Servacek/numeri/docs/pictures/dokumentacne_foto/final.jpg

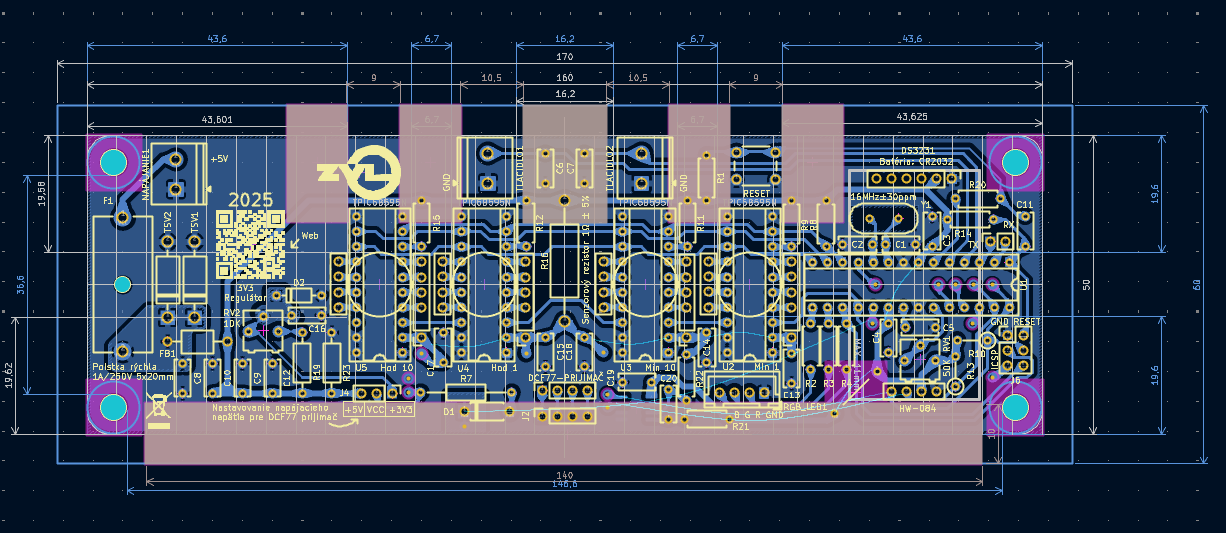
docs/pictures/dokumentacne_foto/final.jpg
