Servacek/numeri/docs/pictures/dokumentacne_foto/photo_1_2026-05-26_11-01-23.jpg

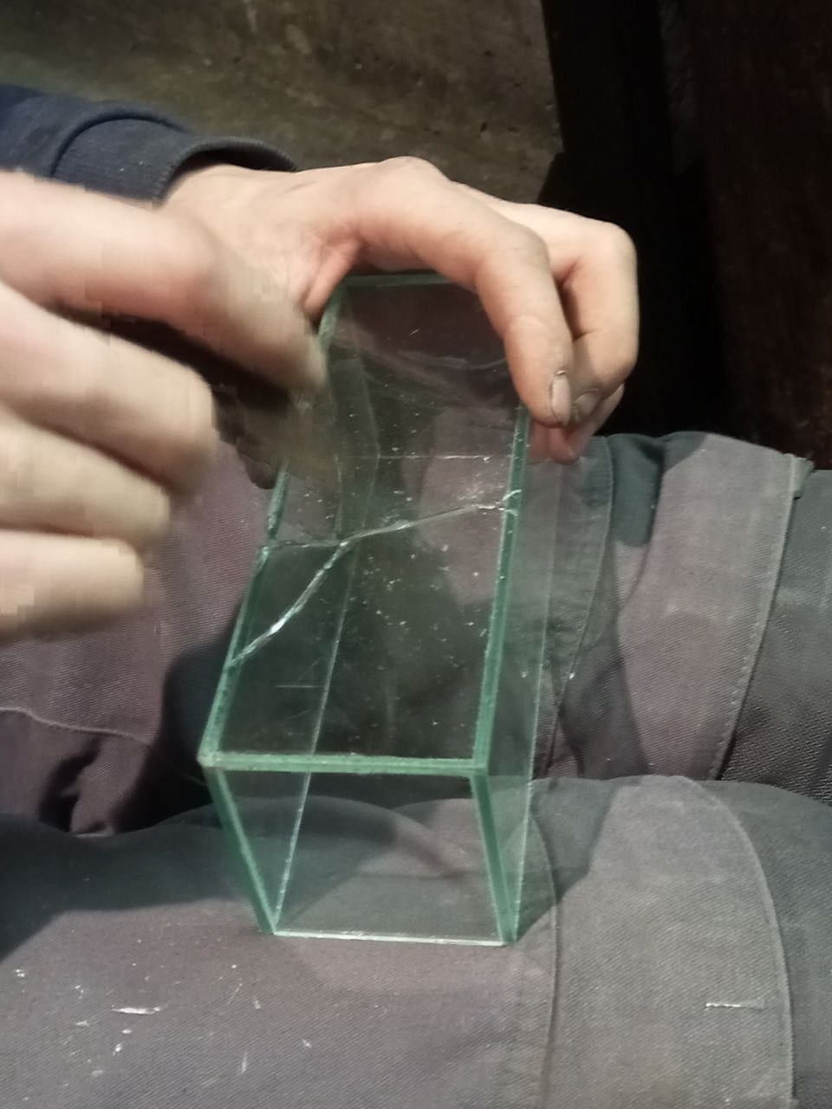
docs/pictures/dokumentacne_foto/photo_1_2026-05-26_11-01-23.jpg
