Servacek/numeri/docs/pictures/dokumentacne_foto/photo_1_2026-05-26_11-02-10.jpg

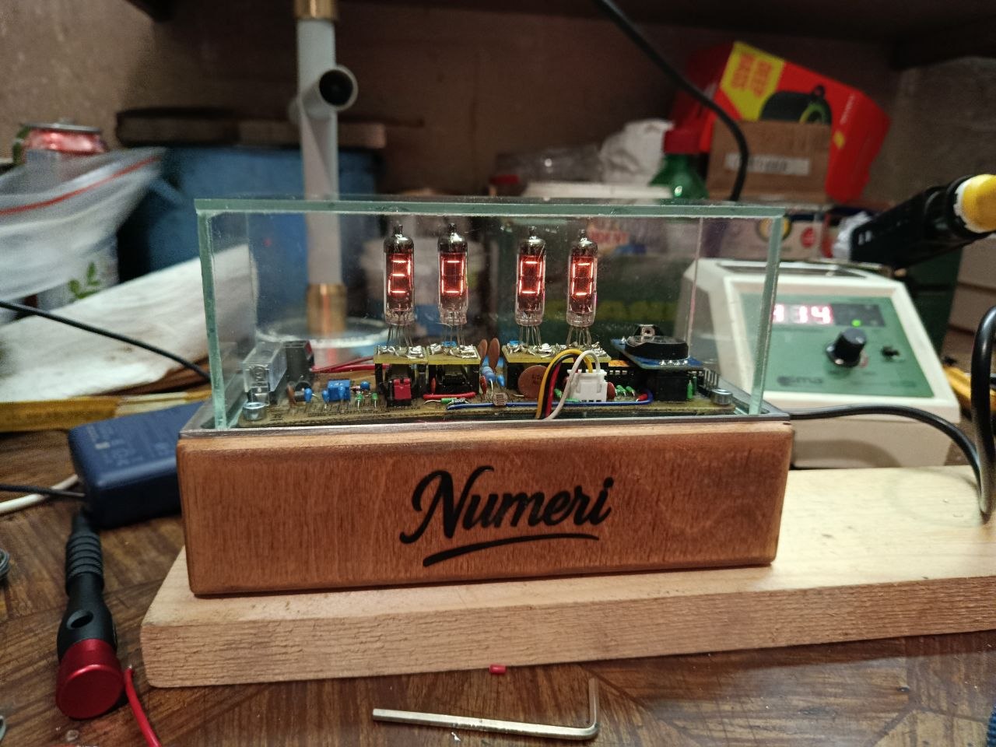
docs/pictures/dokumentacne_foto/photo_1_2026-05-26_11-02-10.jpg
