Servacek/numeri/docs/pictures/dokumentacne_foto/photo_3_2025-08-24_12-32-02.jpg

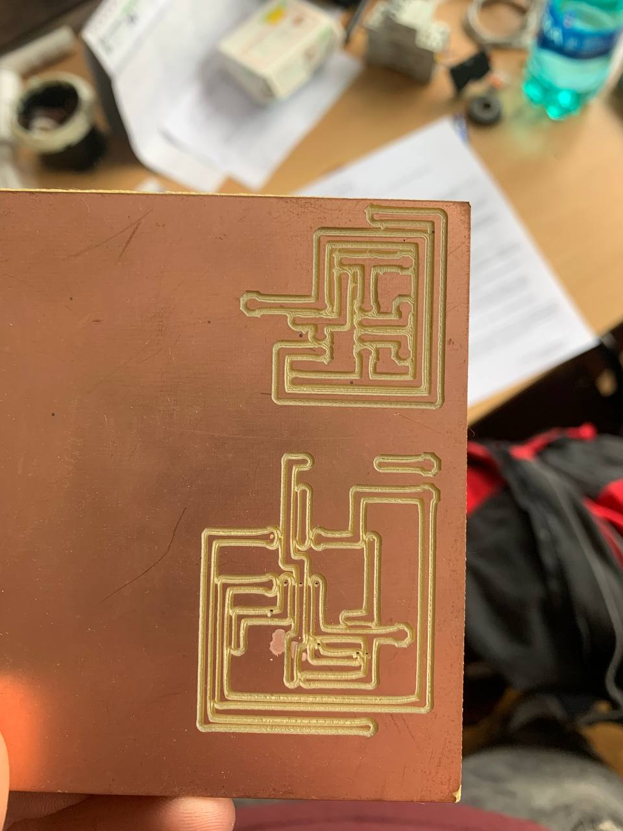
docs/pictures/dokumentacne_foto/photo_3_2025-08-24_12-32-02.jpg
