Servacek/numeri/docs/pictures/dokumentacne_foto/photo_3_2025-09-08_17-15-10.jpg

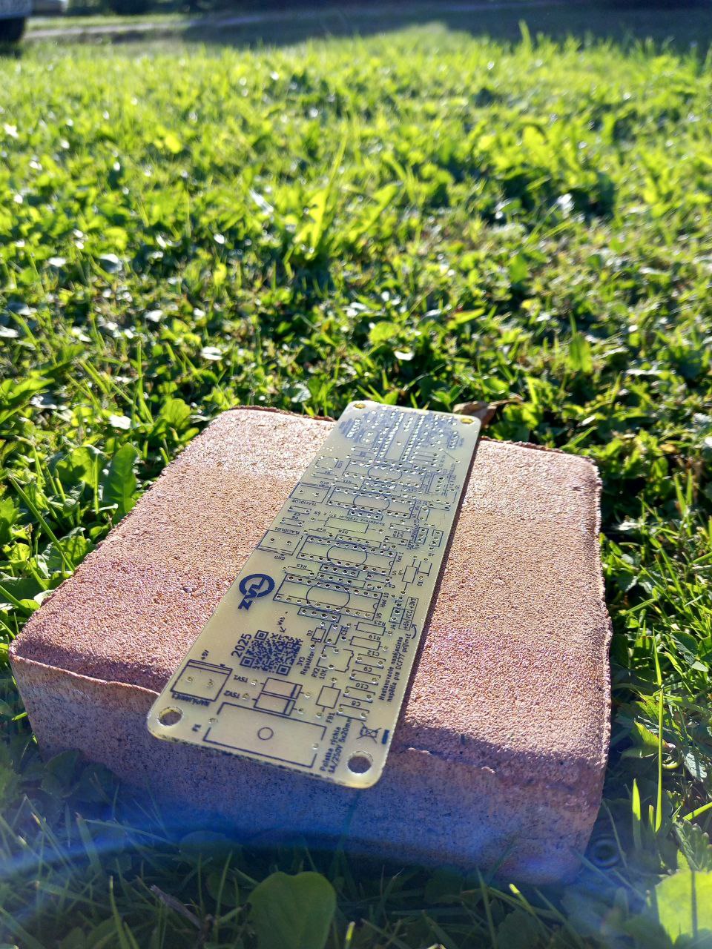
docs/pictures/dokumentacne_foto/photo_3_2025-09-08_17-15-10.jpg
