Servacek/numeri/docs/pictures/dokumentacne_foto/photo_6_2025-09-08_17-15-54.jpg

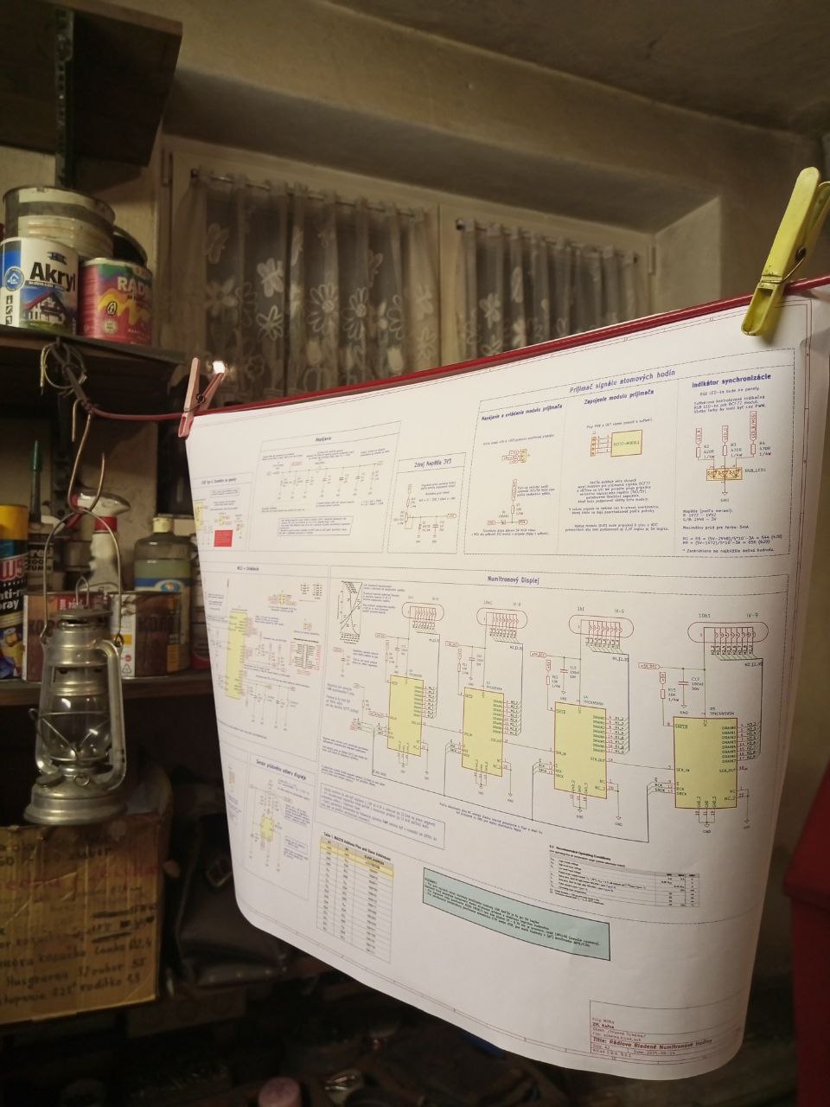
docs/pictures/dokumentacne_foto/photo_6_2025-09-08_17-15-54.jpg
