Servacek/numeri/docs/pictures/dokumentacne_foto/photo_15_2025-08-24_12-28-27.jpg

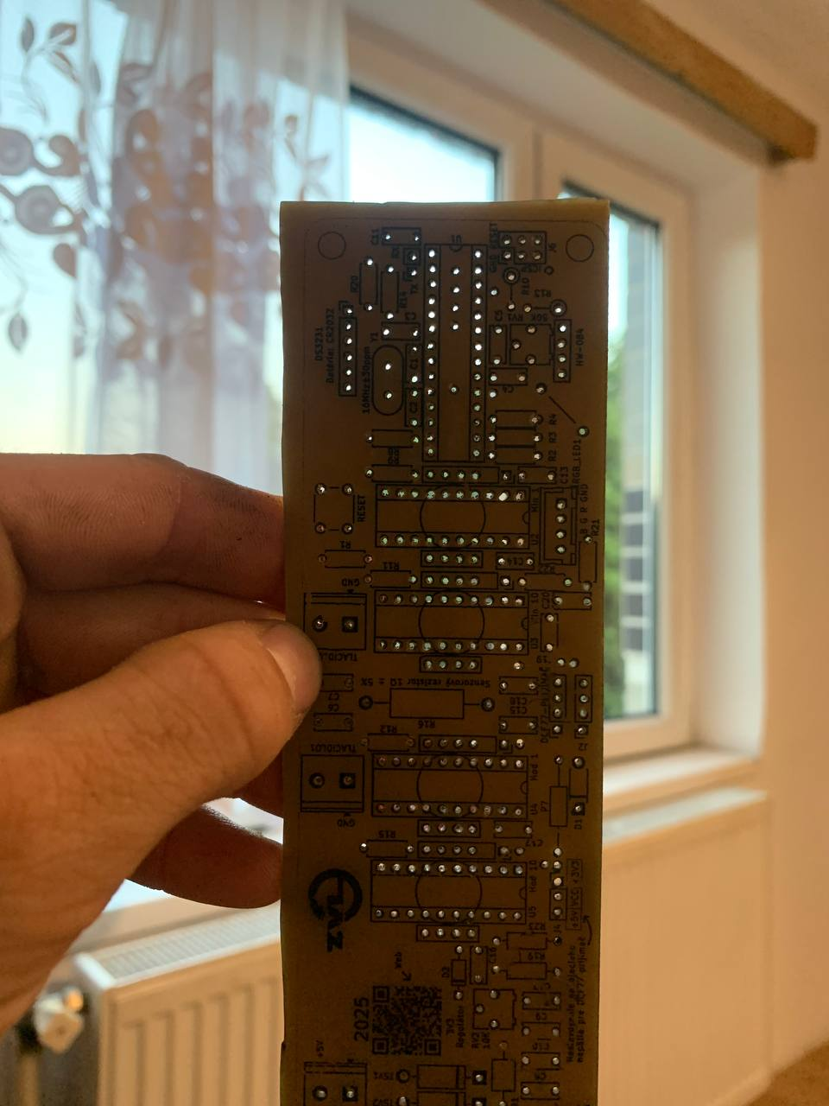
docs/pictures/dokumentacne_foto/photo_15_2025-08-24_12-28-27.jpg
