Servacek/numeri/docs/pictures/dokumentacne_foto/photo_2025-08-12_21-58-07.jpg

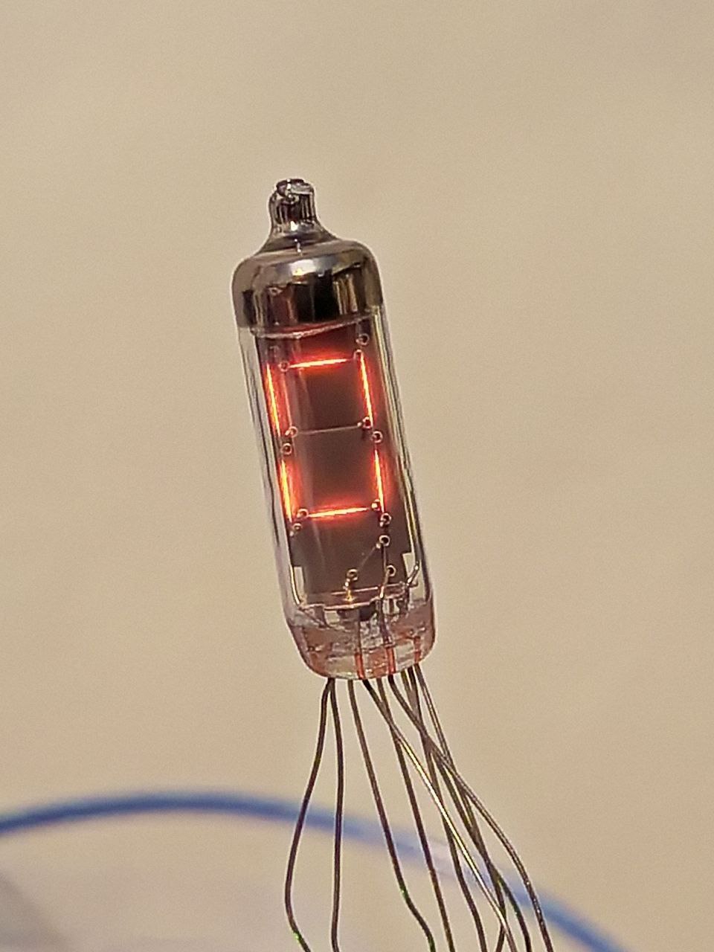
docs/pictures/dokumentacne_foto/photo_2025-08-12_21-58-07.jpg
