Servacek/numeri/docs/pictures/dokumentacne_foto/photo_2025-09-02_12-14-27.jpg

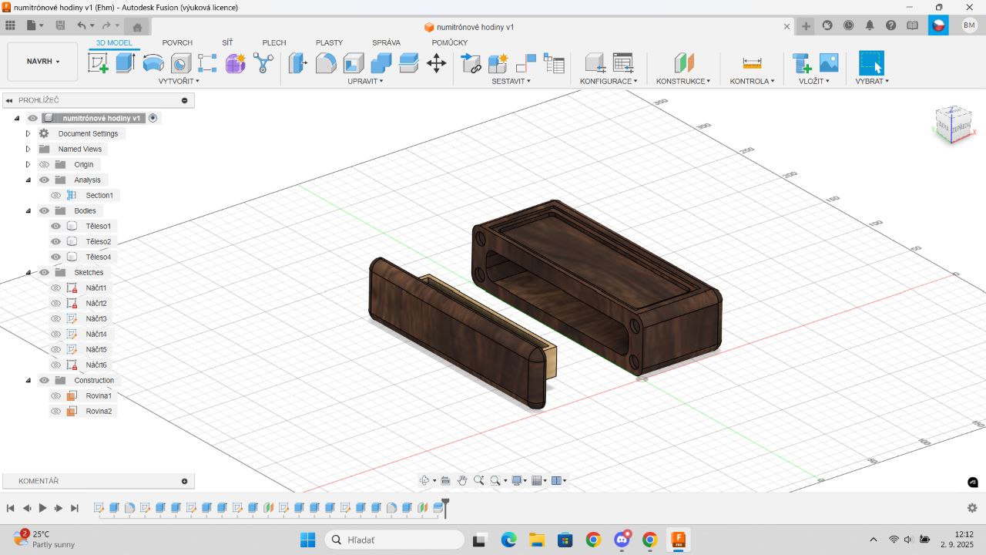
docs/pictures/dokumentacne_foto/photo_2025-09-02_12-14-27.jpg
