Servacek/numeri/docs/pictures/dokumentacne_foto/photo_2025-09-03_09-06-06.jpg

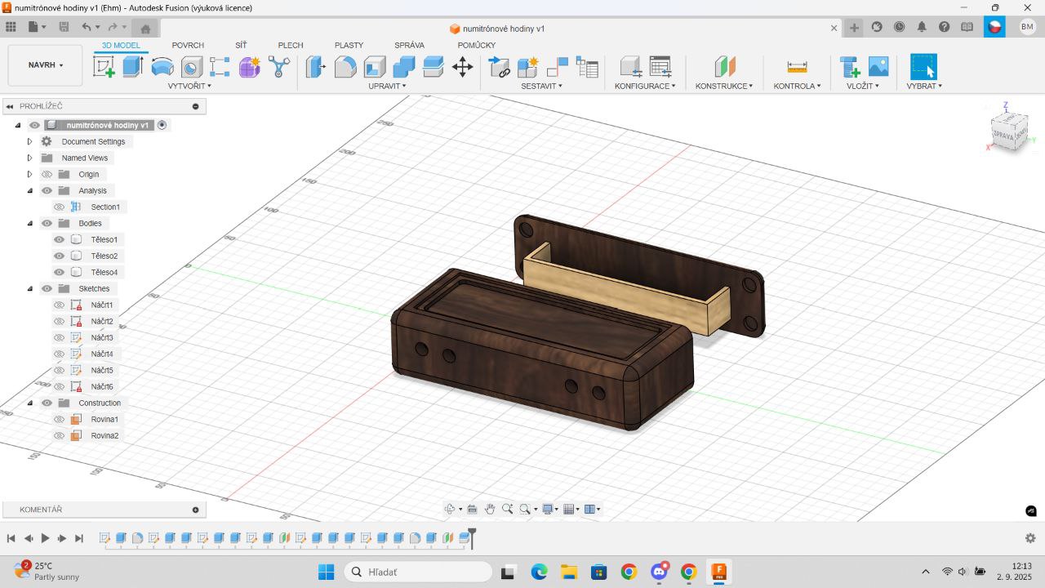
docs/pictures/dokumentacne_foto/photo_2025-09-03_09-06-06.jpg
