Servacek/numeri/docs/pictures/dokumentacne_foto/photo_2025-09-08_14-59-17.jpg

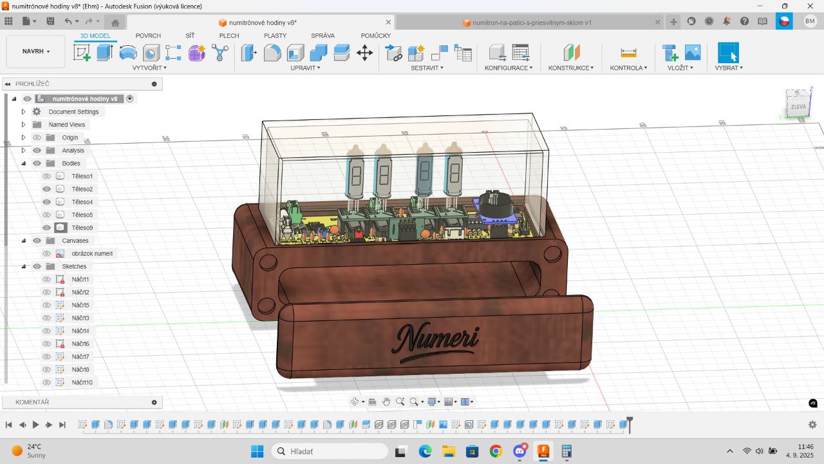
docs/pictures/dokumentacne_foto/photo_2025-09-08_14-59-17.jpg
