Servacek/numeri/docs/pictures/dokumentacne_foto/photo_2025-09-08_15-00-24.jpg

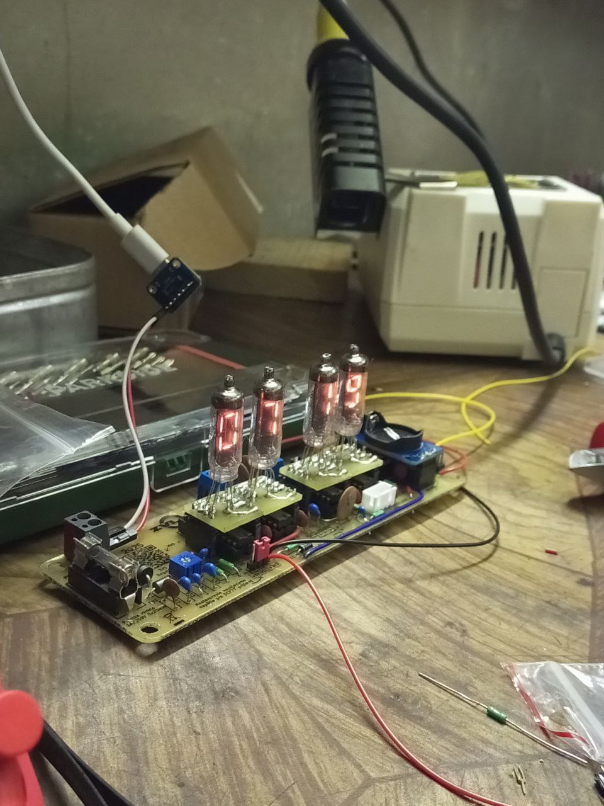
docs/pictures/dokumentacne_foto/photo_2025-09-08_15-00-24.jpg
