Servacek/numeri/docs/pictures/dokumentacne_foto/photo_2025-09-08_15-01-26.jpg

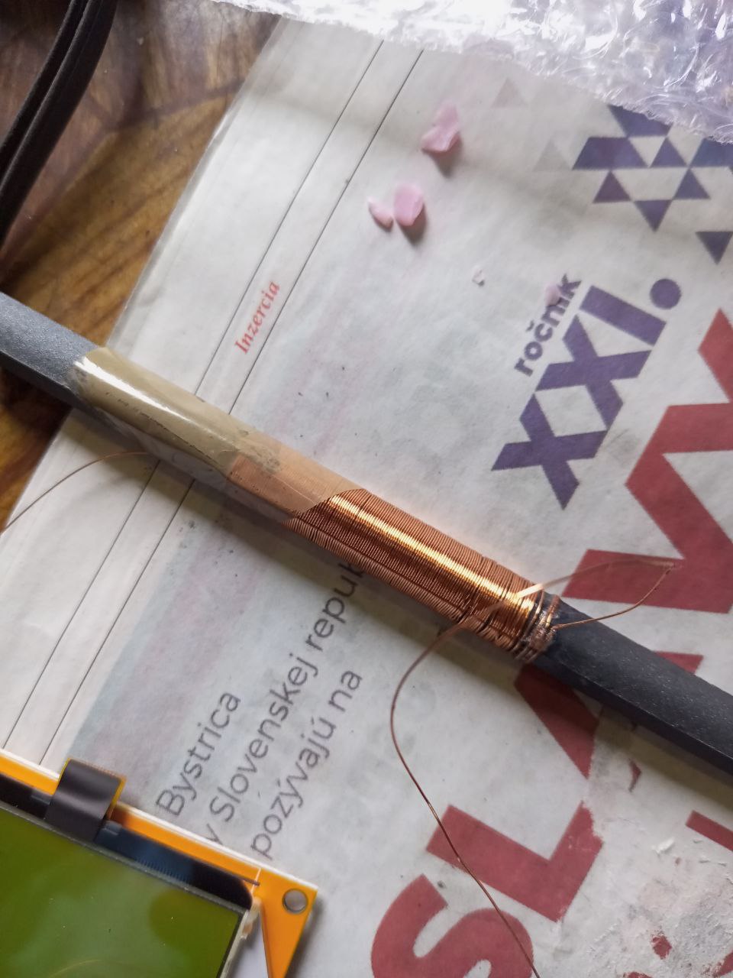
docs/pictures/dokumentacne_foto/photo_2025-09-08_15-01-26.jpg
