Servacek/numeri/docs/pictures/dokumentacne_foto/photo_2026-01-26_16-45-37.jpg

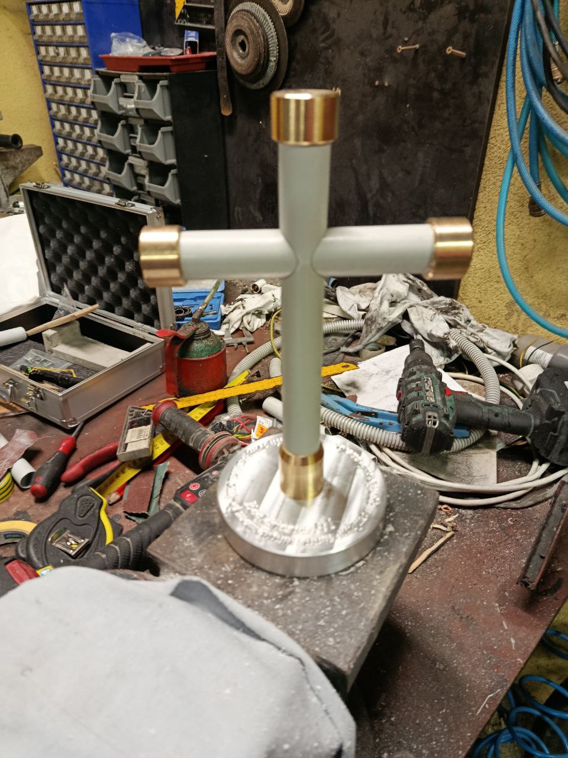
docs/pictures/dokumentacne_foto/photo_2026-01-26_16-45-37.jpg
