Servacek/numeri/docs/pictures/dokumentacne_foto/photo_2026-05-26_11-03-04.jpg

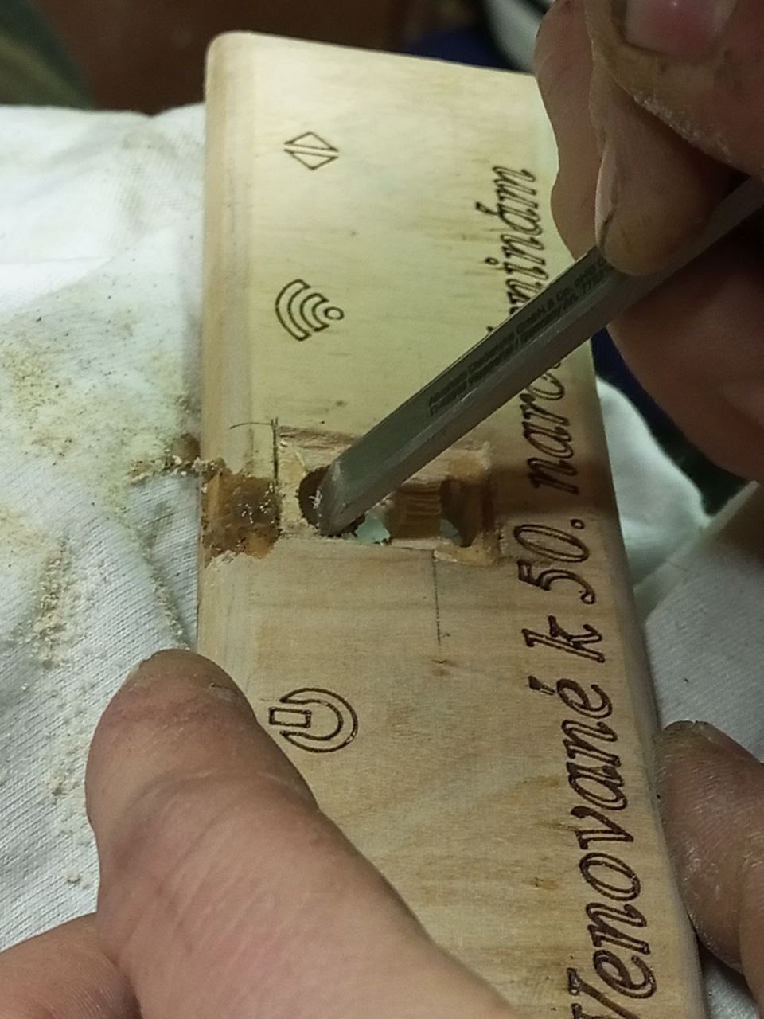
docs/pictures/dokumentacne_foto/photo_2026-05-26_11-03-04.jpg
