Servacek/numeri/docs/pictures/dokumentacne_foto/photo_2026-05-26_11-04-05.jpg

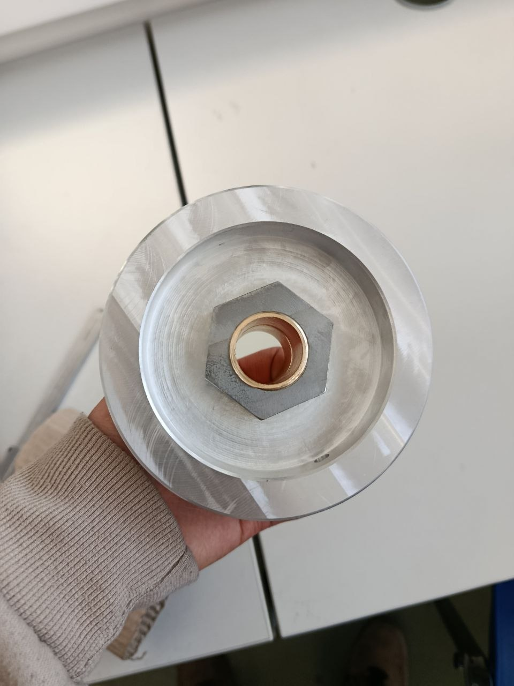
docs/pictures/dokumentacne_foto/photo_2026-05-26_11-04-05.jpg
