Servacek/numeri/docs/pictures/dokumentacne_foto/photo_2026-05-26_11-06-12.jpg

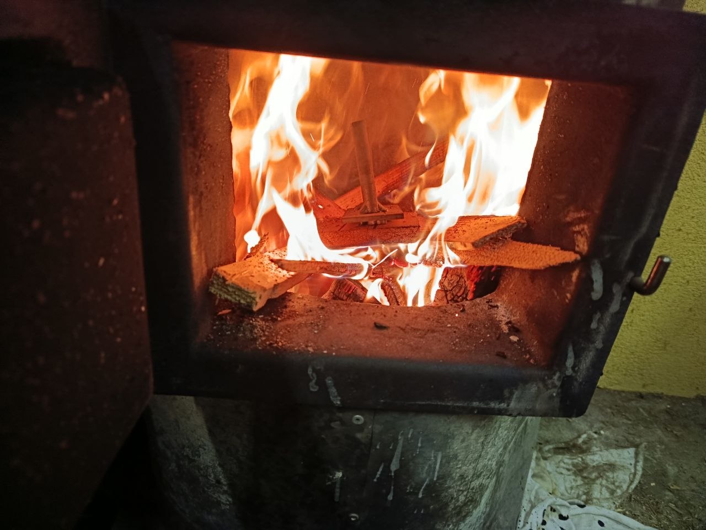
docs/pictures/dokumentacne_foto/photo_2026-05-26_11-06-12.jpg
