Servacek/numeri/docs/pictures/dokumentacne_foto/photo_2026-05-27_07-15-26.jpg

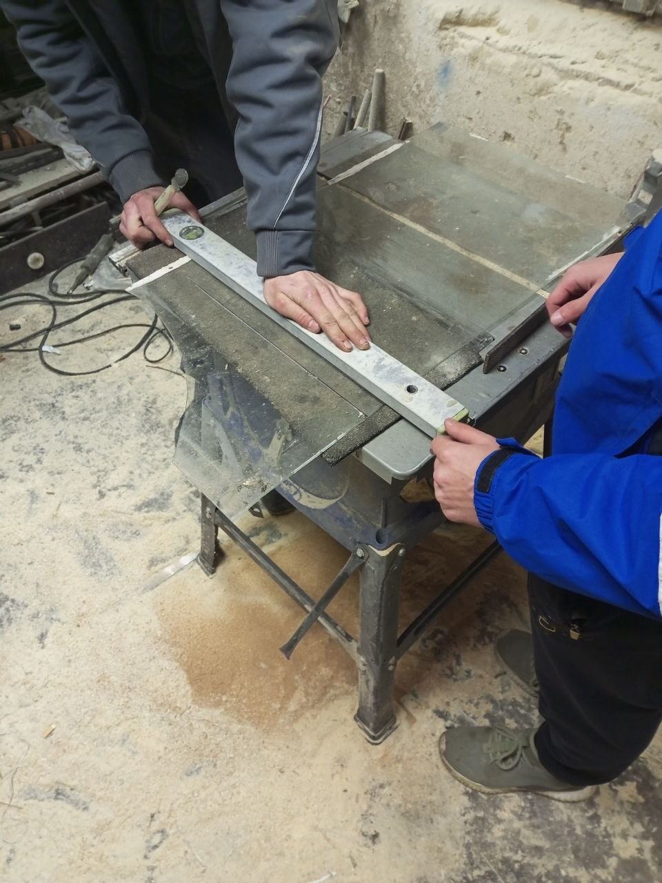
docs/pictures/dokumentacne_foto/photo_2026-05-27_07-15-26.jpg
