Servacek/numeri/docs/pictures/uvod.png

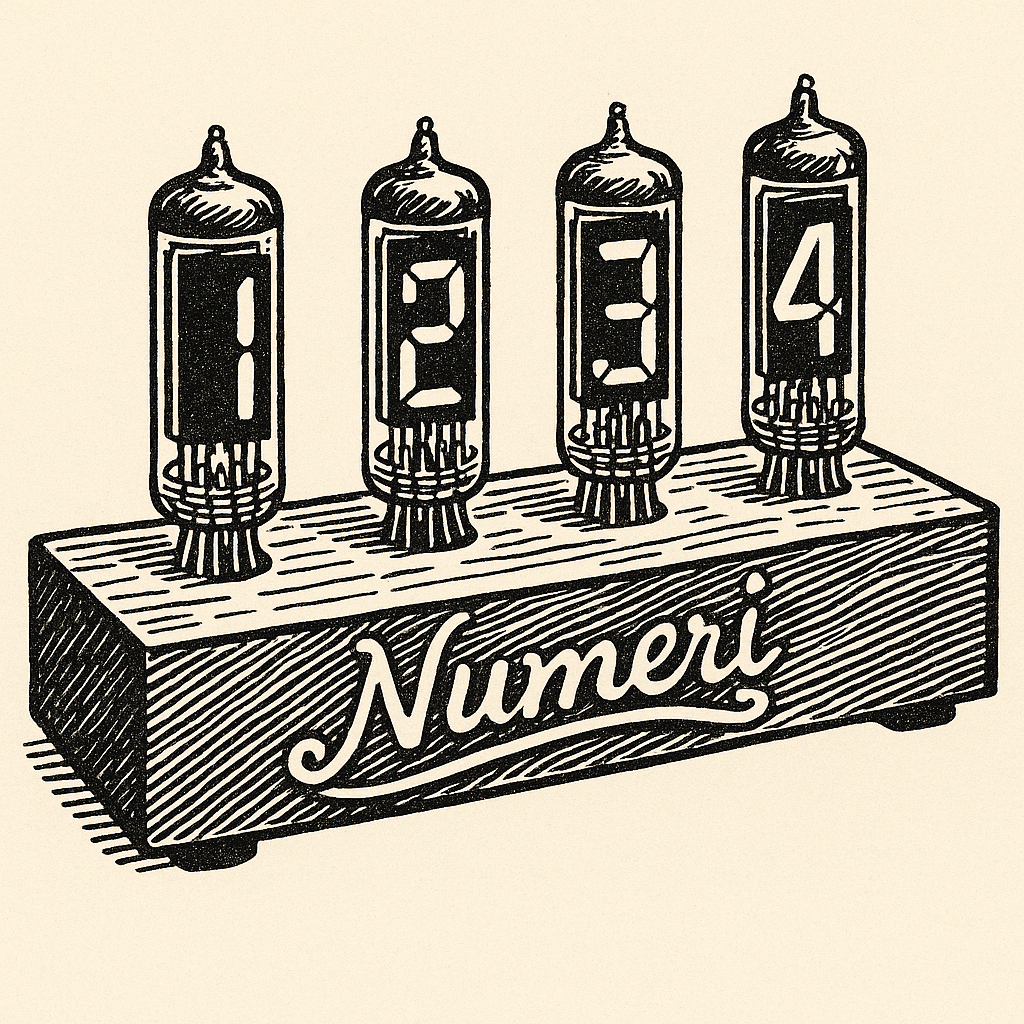
docs/pictures/uvod.png
