Servacek/numeri/3dmodels/external-iv9-socket v13 v6.step

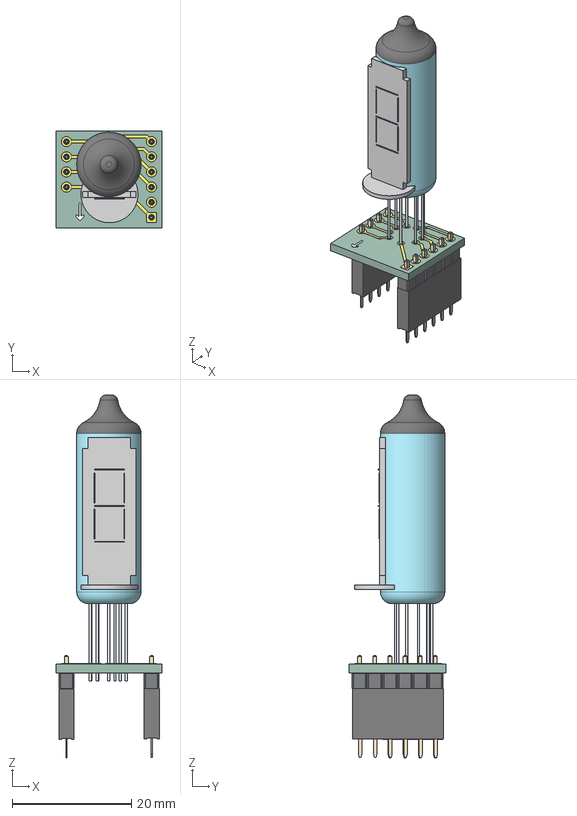
[picture p64: CAD file, 2025-06-27]
3dmodels/external-iv9-socket v13 v6.step
17.8 x 16.3 x 60.9 mm
PinHeader_1x04_P2.54mm_Vertical
PinHeader_1x06_P2.54mm_Vertical
external-iv9-socket_copper
external-iv9-socket_silkscreen
external-iv9-socket_PCB
PinSocket_1x06_P2.54mm_Vertical
PinSocket_1x04_P2.54mm_Vertical
podstava
segment-6 x 7
