Servacek/numeri/3dmodels/HW-84 v7.step

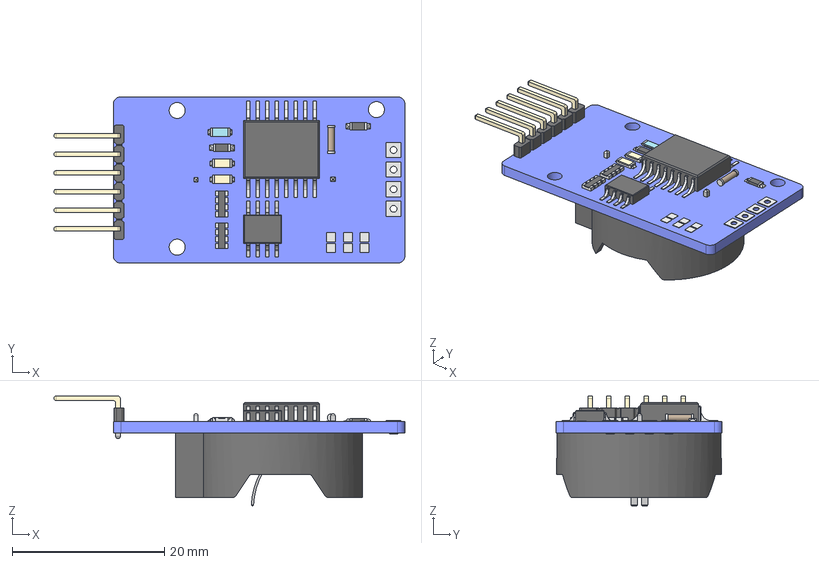
[picture p65: CAD file, 2025-06-27]
3dmodels/HW-84 v7.step
46.1 x 21.9 x 14.4 mm
