Servacek/numeri/3dmodels/Battery Holder Top with CR2032.stp

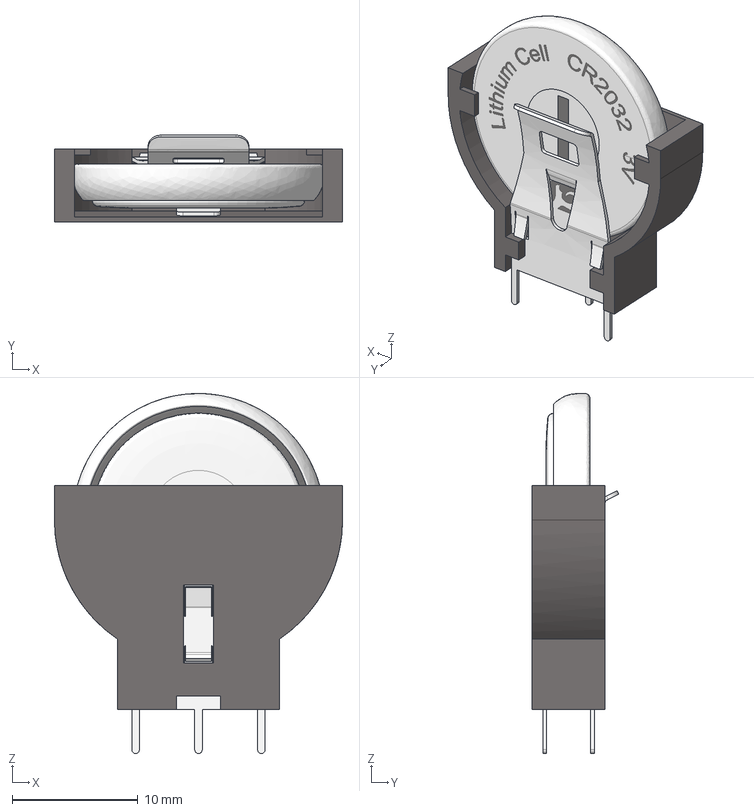
[picture p66: CAD file, 2025-06-18]
3dmodels/Battery Holder Top with CR2032.stp
22.9 x 6.89 x 28.6 mm
