Servacek/numeri/3dmodels/external-iv9-socket-exposed.step

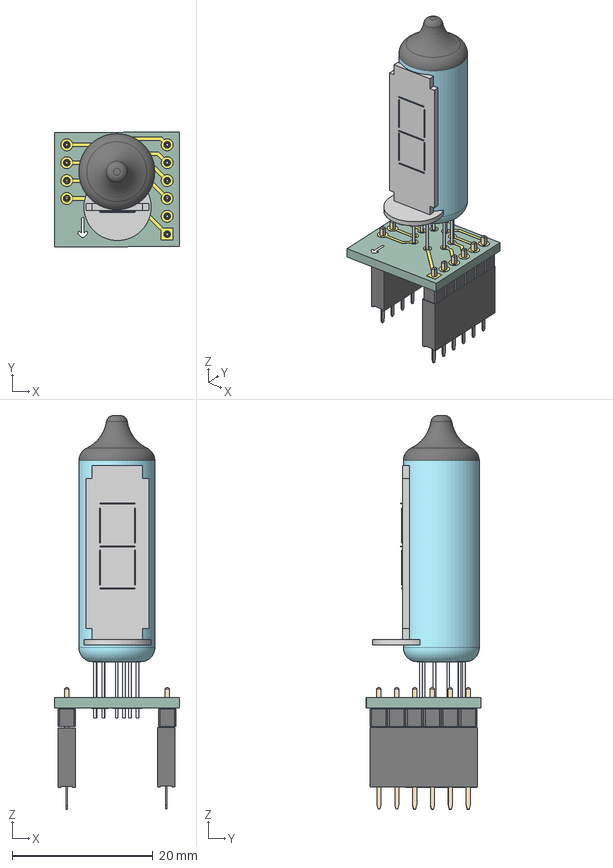
[picture p67: CAD file, 2025-06-18]
3dmodels/external-iv9-socket-exposed.step
17.8 x 16.3 x 56.0 mm
podstava
segment-6 x 7
PinHeader_1x04_P2.54mm_Vertical
PinHeader_1x06_P2.54mm_Vertical
external-iv9-socket_copper
external-iv9-socket_silkscreen
external-iv9-socket_PCB
PinSocket_1x06_P2.54mm_Vertical
PinSocket_1x04_P2.54mm_Vertical
