Servacek/numeri/3dmodels/BH-642.STEP

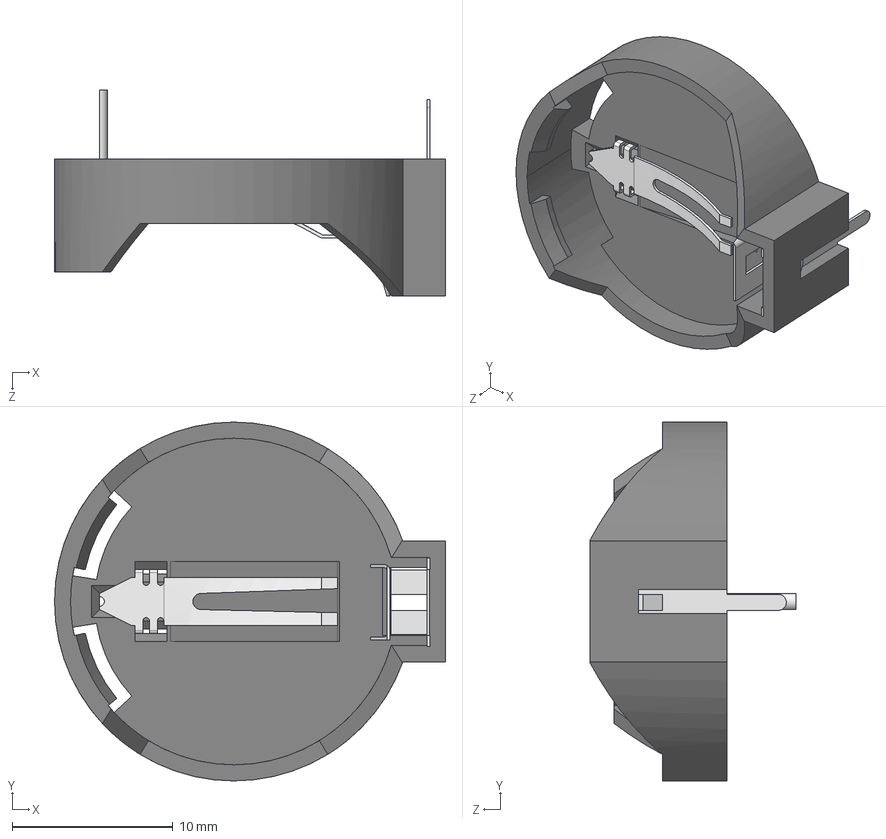
[picture p68: CAD file, 2025-06-18]
3dmodels/BH-642.STEP
24.3 x 22.3 x 12.8 mm
BH-642_Plastic
BH-642_Metal_minus
BH-642_Metal_plus
