Servacek/numeri/firmver/src/modules/dcf77.cpp

//
//  www.blinkenlight.net
//
//  Copyright 2016 Udo Klein
//
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
#include "modules/dcf77.h"


namespace Internal { namespace Debug {
    void debug_helper(char data) {
        (void)data; // Nepouzivame, ale nechceme warning.
        sprint(data == 0? 'S': data == 1? '?': data - 2 + '0', 0);
    }

    void bcddigit(uint8_t data) {
        if (data <= 0x09) {
            sprint(data, HEX);
        } else {
            sprint('?');
        }
    }

    void bcddigits(uint8_t data) {
        bcddigit(data >>  4);
        bcddigit(data & 0xf);
    }

    void hexdump(uint8_t data) {
        if (data < 0x10) { sprint('0'); }
        sprint(data, HEX);
    }

    void sprintpp16m(int16_t pp16m) {
        const int16_t ppm = pp16m / 16;
        sprint(ppm);
        sprint('.');
        const int16_t residue = ABS(pp16m - 16 * ppm);
        if (residue == 0) {
            sprint(F("0000"));
        } else
        if (residue == 1) {
            sprint(F("0625"));
        } else {
            // 1/16 = .0625
            sprint(residue * 625);
        }
        sprint(F(" ppm"));
    }
}}

namespace BCD {
    void print(const bcd_t value) {
        (void)value; // Nepouzivame, ale nechceme warning.
        sprint(value.val >> 4 & 0xF, HEX);
        sprint(value.val >> 0 & 0xF, HEX);
    }

    void increment(bcd_t &value) {
        if (value.digit.lo < 9) {
            ++value.digit.lo;
        } else {
            value.digit.lo = 0;

            if (value.digit.hi < 9) {
                ++value.digit.hi;
            } else {
                value.digit.hi = 0;
            }
        }
    }

    bcd_t int_to_bcd(const uint8_t value) {
        const uint8_t hi = value / 10;

        bcd_t result;
        result.digit.hi = hi;
        result.digit.lo = value-10*hi;

        return result;
    }

    uint8_t bcd_to_int(const bcd_t value) {
        return value.digit.lo + 10*value.digit.hi;
    }

    bool operator == (const bcd_t a, const bcd_t b) {
        return a.val == b.val;
    }
    bool operator != (const bcd_t a, const bcd_t b) {
        return a.val != b.val;
    }
    bool operator >= (const bcd_t a, const bcd_t b) {
        return a.val >= b.val;
    }
    bool operator <= (const bcd_t a, const bcd_t b) {
        return a.val <= b.val;
    }
    bool operator > (const bcd_t a, const bcd_t b) {
        return a.val > b.val;
    }
    bool operator < (const bcd_t a, const bcd_t b) {
        return a.val < b.val;
    }
}

namespace Internal { namespace Arithmetic_Tools {
    void bounded_add(uint8_t &value, const uint8_t amount) {
        if (value >= 255-amount) { value = 255; } else { value += amount; }
    }

    void bounded_sub(uint8_t &value, const uint8_t amount) {
        if (value <= amount) { value = 0; } else { value -= amount; }
    }

    uint8_t bit_count(const uint8_t value) {
        const uint8_t tmp1 = (value & 0x55) + ((value>>1) & 0x55);
        const uint8_t tmp2 = (tmp1  & 0x33) + ((tmp1>>2) & 0x33);
        return (tmp2 & 0x0f) + (tmp2>>4);
    }

    uint8_t parity(const uint8_t value) {
        uint8_t tmp = value;

        tmp = (tmp & 0xf) ^ (tmp >> 4);
        tmp = (tmp & 0x3) ^ (tmp >> 2);
        tmp = (tmp & 0x1) ^ (tmp >> 1);

        return tmp;
    }

    uint8_t set_bit(const uint8_t data, const uint8_t number, const uint8_t value) {
        return value? data|(1<<number): data & ~(1<<number);
    }
}}

namespace Internal {  // DCF77_Flag_Decoder
    void DCF77_Flag_Decoder::setup() {
        uses_summertime = 0;
        abnormal_transmitter_operation = 0;
        timezone_change_scheduled = 0;
        leap_second_scheduled = 0;
        date_parity = 0;
    }

    void DCF77_Flag_Decoder::cummulate(int8_t &average, const bool count_up) {
        if (count_up) {
            average += (average < 127);
        } else {
            average -= (average > -127);
        }
    }

    void DCF77_Flag_Decoder::process_tick(const uint8_t current_second, const uint8_t tick_value) {
        switch (current_second) {
            case 15: abnormal_transmitter_operation = tick_value;      break;
            case 16: cummulate(timezone_change_scheduled, tick_value); break;
            case 17: cummulate(uses_summertime, tick_value);           break;
            case 18: cummulate(uses_summertime, 1-tick_value);         break;
            case 19: cummulate(leap_second_scheduled, tick_value);     break;
            case 58: cummulate(date_parity, tick_value);               break;
        }
    }

    void DCF77_Flag_Decoder::reset_after_previous_hour() {
        // HH := hh+1
        // timezone_change_scheduled will be set from hh:01 to HH:00
        // leap_second_scheduled will be set from hh:01 to HH:00

        if (timezone_change_scheduled > 0) {
            uses_summertime = 0;
        }
        timezone_change_scheduled = 0;
        leap_second_scheduled = 0;
    }

    void DCF77_Flag_Decoder::reset_before_new_day() {
        // date_parity will stay the same 00:00-23:59
        date_parity = 0;
    }

    bool DCF77_Flag_Decoder::get_uses_summertime() {
        return uses_summertime >= 0;
    }

    bool DCF77_Flag_Decoder::get_abnormal_transmitter_operation() {
        return abnormal_transmitter_operation;
    }

    bool DCF77_Flag_Decoder::get_timezone_change_scheduled() {
        return timezone_change_scheduled > 0;
    }

    bool DCF77_Flag_Decoder::get_leap_second_scheduled() {
        return leap_second_scheduled > 0;
    }

    uint8_t DCF77_Flag_Decoder::get_date_parity() {
        return date_parity > 0;
    }


    void DCF77_Flag_Decoder::get_quality(uint8_t &uses_summertime_quality,
                                         uint8_t &timezone_change_scheduled_quality,
                                         uint8_t &leap_second_scheduled_quality) {
        uses_summertime_quality           = ABS(uses_summertime);
        timezone_change_scheduled_quality = ABS(timezone_change_scheduled);
        leap_second_scheduled_quality     = ABS(leap_second_scheduled);
    }

    void DCF77_Flag_Decoder::debug() {
        sprint(F("Backup Antenna, TZ change, TZ, Leap scheduled, Date parity: "));
        sprint(abnormal_transmitter_operation, BIN);
        sprint(',');
        sprint(timezone_change_scheduled, DEC);
        sprint(',');
        sprint(uses_summertime, DEC);
        sprint(',');
        sprint(leap_second_scheduled, DEC);
        sprint(',');
        sprintln(date_parity, DEC);
    }
}

namespace Internal {  // DCF77_Decade_Decoder
    /*
    void DCF77_Decade_Decoder::process_tick(const uint8_t current_second, const uint8_t tick_value) {
        switch (current_second) {
            case 54: decade_data.val +=      tick_value; break;
            case 55: decade_data.val += 0x02*tick_value; break;
            case 56: decade_data.val += 0x04*tick_value; break;
            case 57: decade_data.val += 0x08*tick_value;
            hamming_binning<4, false>(decade_data); break;

            case 58: compute_max_index();
            // fall through on purpose
            default: decade_data.val = 0;
        }
    }
    */

    void DCF77_Decade_Decoder::process_tick(const uint8_t current_second, const uint8_t tick_value) {
        BCD_binning<DCF77_Decade_template_parameters::BCD_binning_t> (current_second, tick_value);
    }

    void DCF77_Decade_Decoder::debug() {
        sprint(F("Decade: "));
        this->Binning::Decoder<DCF77_Decade_template_parameters::decoder_t::data_type,
                               DCF77_Decade_template_parameters::decoder_t::number_of_bins>::debug();
    }
}

namespace Internal { // DCF77_Year_Decoder
    void DCF77_Year_Decoder::advance_tick() {
        Binning::Decoder<DCF77_Year_template_parameters::decoder_t::data_type,
                         DCF77_Year_template_parameters::decoder_t::number_of_bins>::advance_tick();
        if (Binning::Decoder<DCF77_Year_template_parameters::decoder_t::data_type,
                             DCF77_Year_template_parameters::decoder_t::number_of_bins>::get_time_value().val == 0) {
            Decade_Decoder.advance_tick();
        }
    }

/*
    void DCF77_Year_Decoder::process_tick(const uint8_t current_second, const uint8_t tick_value) {
        switch (current_second) {
            case 50: year_data.val +=      tick_value; break;
            case 51: year_data.val +=  0x2*tick_value; break;
            case 52: year_data.val +=  0x4*tick_value; break;
            case 53: year_data.val +=  0x8*tick_value;
            hamming_binning<4, false>(year_data); break;

            case 54: compute_max_index();
            // fall through on purpose
            default: year_data.val = 0;
        }

        Decade_Decoder.process_tick(current_second, tick_value);
    }
*/
    void DCF77_Year_Decoder::process_tick(const uint8_t current_second, const uint8_t tick_value) {
        BCD_binning<DCF77_Year_template_parameters::BCD_binning_t> (current_second, tick_value);

        Decade_Decoder.process_tick(current_second, tick_value);
    }

    void DCF77_Year_Decoder::get_quality(lock_quality_t &lock_quality) {
        Binning::Decoder<DCF77_Year_template_parameters::decoder_t::data_type,
                         DCF77_Year_template_parameters::decoder_t::number_of_bins>::get_quality(lock_quality);

        lock_quality_t decade_lock_quality;
        Decade_Decoder.get_quality(decade_lock_quality);

        const uint8_t lock_max  = MAX(lock_quality.lock_max, decade_lock_quality.lock_max);
        const uint8_t noise_max = lock_max - MIN(lock_quality.lock_max - lock_quality.noise_max,
                                                 decade_lock_quality.lock_max - decade_lock_quality.noise_max);
        lock_quality.lock_max  = lock_max;
        lock_quality.noise_max = noise_max;
    }

    uint8_t DCF77_Year_Decoder::get_quality_factor() {
        const uint8_t qf_years = Binning::Decoder<DCF77_Year_template_parameters::decoder_t::data_type,
                                                  DCF77_Year_template_parameters::decoder_t::number_of_bins>::get_quality_factor();
        const uint8_t qf_decades = Decade_Decoder.get_quality_factor();
        return MIN(qf_years, qf_decades);
    }

    BCD::bcd_t DCF77_Year_Decoder::get_time_value() {
        BCD::bcd_t year = Binning::Decoder<DCF77_Year_template_parameters::decoder_t::data_type,
                                           DCF77_Year_template_parameters::decoder_t::number_of_bins>::get_time_value();
        BCD::bcd_t decade = Decade_Decoder.get_time_value();

        if (year.val == 0xff || decade.val == 0xff) {
            // undefined handling
            year.val = 0xff;
        } else {
            year.val += decade.val << 4;
        }

        return year;
    }

    void DCF77_Year_Decoder::setup() {
        Binning::Decoder<DCF77_Year_template_parameters::decoder_t::data_type,
                         DCF77_Year_template_parameters::decoder_t::number_of_bins>::setup();
        Decade_Decoder.setup();
    }

    void DCF77_Year_Decoder::dump() {
        Binning::Decoder<DCF77_Year_template_parameters::decoder_t::data_type,
                         DCF77_Year_template_parameters::decoder_t::number_of_bins>::dump();
        sprint('/');
        Decade_Decoder.dump();
    }

    void DCF77_Year_Decoder::debug() {
        sprint(F("Year: "));
        Binning::Decoder<DCF77_Year_template_parameters::decoder_t::data_type,
                         DCF77_Year_template_parameters::decoder_t::number_of_bins>::debug();
        Decade_Decoder.debug();
    }
}

namespace Internal {  // DCF77_Month_Decoder
/*
    void DCF77_Month_Decoder::process_tick(const uint8_t current_second, const uint8_t tick_value) {
        switch (current_second) {
            case 45: month_data.val +=      tick_value; break;
            case 46: month_data.val +=  0x2*tick_value; break;
            case 47: month_data.val +=  0x4*tick_value; break;
            case 48: month_data.val +=  0x8*tick_value; break;
            case 49: month_data.val += 0x10*tick_value;
            hamming_binning<5, false>(month_data); break;

            case 50: compute_max_index();
            // fall through on purpose
            default: month_data.val = 0;
        }
    }
*/
    void DCF77_Month_Decoder::process_tick(const uint8_t current_second, const uint8_t tick_value) {
        BCD_binning<DCF77_Month_template_parameters::BCD_binning_t> (current_second, tick_value);
    }

    void DCF77_Month_Decoder::debug() {
        sprint(F("Month: "));
        Binning::Decoder<DCF77_Month_template_parameters::decoder_t::data_type,
                         DCF77_Month_template_parameters::decoder_t::number_of_bins>::debug();
    }
}

namespace Internal {  // DCF77_Weekday_Decoder
/*
    void DCF77_Weekday_Decoder::process_tick(const uint8_t current_second, const uint8_t tick_value) {
        switch (current_second) {
            case 42: weekday_data.val +=      tick_value; break;
            case 43: weekday_data.val +=  0x2*tick_value; break;
            case 44: weekday_data.val +=  0x4*tick_value;
            hamming_binning<3, false>(weekday_data); break;
            case 45: compute_max_index();
            // fall through on purpose
            default: weekday_data.val = 0;
        }
    }
*/

    void DCF77_Weekday_Decoder::process_tick(const uint8_t current_second, const uint8_t tick_value) {
        BCD_binning<DCF77_Weekday_template_parameters::BCD_binning_t> (current_second, tick_value);
}

    void DCF77_Weekday_Decoder::debug() {
        sprint(F("Weekday: "));
        Binning::Decoder<DCF77_Weekday_template_parameters::decoder_t::data_type,
                         DCF77_Weekday_template_parameters::decoder_t::number_of_bins>::debug();
    }
}

namespace Internal {  // DCF77_Day_Decoder
/*
    void DCF77_Day_Decoder::process_tick(const uint8_t current_second, const uint8_t tick_value) {
        switch (current_second) {
            case 36: day_data.val +=      tick_value; break;
            case 37: day_data.val +=  0x2*tick_value; break;
            case 38: day_data.val +=  0x4*tick_value; break;
            case 39: day_data.val +=  0x8*tick_value; break;
            case 40: day_data.val += 0x10*tick_value; break;
            case 41: day_data.val += 0x20*tick_value;
            hamming_binning<6, false>(day_data); break;
            case 42: compute_max_index();
            // fall through on purpose
            default: day_data.val = 0;
        }
    }
*/

    void DCF77_Day_Decoder::process_tick(const uint8_t current_second, const uint8_t tick_value) {
        BCD_binning<DCF77_Day_template_parameters::BCD_binning_t> (current_second, tick_value);
    }

    void DCF77_Day_Decoder::debug() {
        sprint(F("Day: "));
        Binning::Decoder<DCF77_Day_template_parameters::decoder_t::data_type,
                         DCF77_Day_template_parameters::decoder_t::number_of_bins>::debug();
    }
}

namespace Internal {  // DCF77_Hour_Decoder
/*
    void DCF77_Hour_Decoder::process_tick(const uint8_t current_second, const uint8_t tick_value) {
        switch (current_second) {
            case 29: hour_data.val +=      tick_value; break;
            case 30: hour_data.val +=  0x2*tick_value; break;
            case 31: hour_data.val +=  0x4*tick_value; break;
            case 32: hour_data.val +=  0x8*tick_value; break;
            case 33: hour_data.val += 0x10*tick_value; break;
            case 34: hour_data.val += 0x20*tick_value; break;
            case 35: hour_data.val += 0x80*tick_value;        // Parity !!!
                    hamming_binning<7, true>(hour_data); break;

            case 36: compute_max_index();
            // fall through on purpose
            default: hour_data.val = 0;
        }
    }
*/
    void DCF77_Hour_Decoder::process_tick(const uint8_t current_second, const uint8_t tick_value) {
        BCD_binning<DCF77_Hour_template_parameters::BCD_binning_t> (current_second, tick_value);
    }

    void DCF77_Hour_Decoder::debug() {
        sprint(F("Hour: "));
        Binning::Decoder<DCF77_Hour_template_parameters::decoder_t::data_type,
                         DCF77_Hour_template_parameters::decoder_t::number_of_bins>::debug();
    }
}

namespace Internal {  // DCF77_Minute_Decoder
/*
    void DCF77_Minute_Decoder::process_tick(const uint8_t current_second, const uint8_t tick_value) {
        switch (current_second) {
            case 21: minute_data.val +=      tick_value; break;
            case 22: minute_data.val +=  0x2*tick_value; break;
            case 23: minute_data.val +=  0x4*tick_value; break;
            case 24: minute_data.val +=  0x8*tick_value; break;
            case 25: minute_data.val += 0x10*tick_value; break;
            case 26: minute_data.val += 0x20*tick_value; break;
            case 27: minute_data.val += 0x40*tick_value; break;
            case 28: minute_data.val += 0x80*tick_value;        // Parity !!!
                        hamming_binning<8, true>(minute_data);
                        break;
            case 29: compute_max_index();
            // fall through on purpose
            default: minute_data.val = 0;
        }
    }
*/

    void DCF77_Minute_Decoder::process_tick(const uint8_t current_second, const uint8_t tick_value) {
        BCD_binning<DCF77_Minute_template_parameters::BCD_binning_t> (current_second, tick_value);
    }

    void DCF77_Minute_Decoder::debug() {
        sprint(F("Minute: "));
        Binning::Decoder<DCF77_Minute_template_parameters::decoder_t::data_type,
                         DCF77_Minute_template_parameters::decoder_t::number_of_bins>::debug();
    }
}

namespace Internal {  // DCF77_Second_Decoder
    void DCF77_Second_Decoder::setup() {
        Binning::Decoder<DCF77_Second_template_parameters::decoder_t::data_type,
                         DCF77_Second_template_parameters::decoder_t::number_of_bins>::setup();
        prediction_match = convolution_binning_not_ready;
        buffered_match = convolution_binning_not_ready;
    }

    uint8_t DCF77_Second_Decoder::get_prediction_match() {
        return buffered_match;
    }

    void DCF77_Second_Decoder::set_convolution_time(const DCF77_Encoder &now) {
        DCF77_Encoder convolution_clock = now;

        // we are always decoding the data for the NEXT minute
        convolution_clock.advance_minute();

        // the convolution kernel shall have proper flag settings
        convolution_clock.autoset_control_bits();

        convolution_clock.get_serialized_clock_stream(convolution_kernel);
        prediction_match = 0;
    }

    void DCF77_Second_Decoder::convolution_binning(const uint8_t tick_data) {
        using namespace Arithmetic_Tools;

        // determine sync lock
        if (this->signal_max - this->noise_max <= lock_threshold || get_time_value() == 3) {
            // after a lock is acquired this happens only once per minute and it is
            // reasonable cheap to process,
            //
            // that is: after we have a "lock" this will be processed whenever
            // the sync mark was detected

            compute_max_index();

            const uint8_t convolution_weight = 50;
            if (this->signal_max > 255-convolution_weight) {
                // If we know we can not raise the maximum any further we
                // will lower the noise floor instead.
                for (uint8_t bin_index = 0; bin_index < seconds_per_minute; ++bin_index) {
                    bounded_decrement<convolution_weight>(this->data[bin_index]);
                }
                this->signal_max -= convolution_weight;
                bounded_decrement<convolution_weight>(this->noise_max);
            }

            buffered_match = prediction_match;
        }

        if (tick_data == DCF77::sync_mark) {
            bounded_increment<6>(this->data[this->tick]);
            if (this->tick == this->signal_max_index) {
                prediction_match += 6;
            }
        } else if (tick_data == DCF77::short_tick || tick_data == DCF77::long_tick) {
            uint8_t decoded_bit = (tick_data == DCF77::long_tick);

            // bit 0 always 0
            uint8_t bin = this->tick>0? this->tick-1: seconds_per_minute-1;
            const bool is_match = (decoded_bit == 0);
            this->data[bin] += is_match;
            if (bin == this->signal_max_index) {
                prediction_match += is_match;
            }

            // bit 16 is where the convolution kernel starts
            bin = bin>15? bin-16: bin + seconds_per_minute-16;
            uint8_t current_byte_index = 0;
            uint8_t current_bit_index = 3;
            uint8_t current_byte_value = convolution_kernel.byte_0 >> 3;
            while (current_byte_index < 6) {
                while (current_bit_index < 8) {
                    const uint8_t current_bit_value = current_byte_value & 1;
                    const bool is_match = (decoded_bit == current_bit_value);

                    this->data[bin] += is_match;
                    if (bin == this->signal_max_index) {
                        prediction_match += is_match;
                    }

                    bin = bin>0? bin-1: seconds_per_minute-1;

                    current_byte_value >>= 1;
                    ++current_bit_index;

                    if (current_byte_index == 5 && current_bit_index > 5) {
                        break;
                    }
                }
                current_bit_index = 0;
                ++current_byte_index;
                current_byte_value = (&(convolution_kernel.byte_0))[current_byte_index];
            }
        }

        this->tick = this->tick<seconds_per_minute-1? this->tick+1: 0;
    }

    void DCF77_Second_Decoder::sync_mark_binning(const uint8_t tick_data) {
        // We use a binning approach to find out the proper phase.
        // The goal is to localize the sync_mark. Due to noise
        // there may be wrong marks of course. The idea is to not
        // only look at the statistics of the marks but to exploit
        // additional data properties:

        // Bit position  0 after a proper sync is a 0.
        // Bit position 20 after a proper sync is a 1.

        // The binning will work as follows:

        //   1) A sync mark will score +6 points for the current bin
        //      it will also score -2 points for the previous bin
        //                         -2 points for the following bin
        //                     and -2 points 20 bins later
        //  In total this will ensure that a completely lost signal
        //  will not alter the buffer state (on average)

        //   2) A 0 will score +1 point for the previous bin
        //      it also scores -2 point 20 bins back
        //                 and -2 points for the current bin

        //   3) A 1 will score +1 point 20 bins back
        //      it will also score -2 point for the previous bin
        //                     and -2 points for the current bin

        //   4) An undefined value will score -2 point for the current bin
        //                                    -2 point for the previous bin
        //                                    -2 point 20 bins back

        //   5) Scores have an upper limit of 255 and a lower limit of 0.

        // Summary: sync mark earns 6 points, a 0 in position 0 and a 1 in position 20 earn 1 bonus point
        //          anything that allows to infer that any of the "connected" positions is not a sync will remove 2 points

        // It follows that the score of a sync mark (during good reception)
        // may move up/down the whole scale in slightly below 64 minutes.
        // If the receiver should glitch for whatever reason this implies
        // that the clock will take about 33 minutes to recover the proper
        // phase (during phases of good reception). During bad reception things
        // are more tricky.
        using namespace Arithmetic_Tools;

        const uint8_t previous_tick = this->tick>0? this->tick-1: seconds_per_minute-1;
        const uint8_t previous_21_tick = this->tick>20? this->tick-21: this->tick + seconds_per_minute-21;

        switch (tick_data) {
            case DCF77::sync_mark:
                bounded_increment<6>(this->data[this->tick]);

                bounded_decrement<2>(this->data[previous_tick]);
                bounded_decrement<2>(this->data[previous_21_tick]);

                { const uint8_t next_tick = this->tick< seconds_per_minute-1? this->tick+1: 0;
                bounded_decrement<2>(this->data[next_tick]); }
                break;

            case DCF77::short_tick:
                bounded_increment<1>(this->data[previous_tick]);

                bounded_decrement<2>(this->data[this->tick]);
                bounded_decrement<2>(this->data[previous_21_tick]);
                break;

            case DCF77::long_tick:
                bounded_increment<1>(this->data[previous_21_tick]);

                bounded_decrement<2>(this->data[this->tick]);
                bounded_decrement<2>(this->data[previous_tick]);
                break;

            case DCF77::undefined:
            default:
                bounded_decrement<2>(this->data[this->tick]);
                bounded_decrement<2>(this->data[previous_tick]);
                bounded_decrement<2>(this->data[previous_21_tick]);
        }
        this->tick = this->tick<seconds_per_minute-1? this->tick+1: 0;

        // determine sync lock
        if (this->signal_max - this->noise_max <=lock_threshold ||
            get_time_value() == 3) {
            // after a lock is acquired this happens only once per minute and it is
            // reasonable cheap to process,
            //
            // that is: after we have a "lock" this will be processed whenever
            // the sync mark was detected

            compute_max_index();
        }
    }

    uint8_t DCF77_Second_Decoder::get_time_value() {
        if (this->signal_max - this->noise_max >= lock_threshold) {
            // at least one sync mark and a 0 and a 1 seen
            // the threshold is tricky:
            //   higher --> takes longer to acquire an initial lock, but higher probability of an accurate lock
            //
            //   lower  --> higher probability that the lock will oscillate at the beginning
            //              and thus spoil the downstream stages

            // we have to subtract 2 seconds
            //   1 because the seconds already advanced by 1 tick
            //   1 because the sync mark is not second 0 but second 59

            uint8_t second = 2*seconds_per_minute + this->tick - 2 - this->signal_max_index;
            while (second >= seconds_per_minute) { second-= seconds_per_minute; }

            return second;
        } else {
            return 0xff;
        }
    }

    void DCF77_Second_Decoder::binning(const DCF77::tick_t tick_data) {
        if (prediction_match == convolution_binning_not_ready) {
            sync_mark_binning(tick_data);
        } else {
            convolution_binning(tick_data);
        }
    }

    void DCF77_Second_Decoder::debug() {
        static uint8_t prev_tick;

        if (prev_tick == this->tick) {
            return;
        } else {
            prev_tick = this->tick;

            sprint(F("second: "));
            sprint(get_time_value(), DEC);
            sprint(F(" Sync mark index "));
            Binning::Decoder<DCF77_Second_template_parameters::decoder_t::data_type,
                             DCF77_Second_template_parameters::decoder_t::number_of_bins>::debug();
            sprint(F("Prediction Match: "));
            sprintln(prediction_match, DEC);
            sprintln();
        }
    }
}

namespace Internal {  // DCF77_Encoder
    uint8_t DCF77_Encoder::days_per_month() const {
        switch (month.val) {
            case 0x02:
                // valid till 31.12.2399, but not for year 2000
                // notice year mod 4 == year & 0x03
                return 28 + ((year.val != 0) && ((bcd_to_int(year) & 0x03) == 0)? 1: 0);
            case 0x01: case 0x03: case 0x05: case 0x07: case 0x08: case 0x10: case 0x12: return 31;
            case 0x04: case 0x06: case 0x09: case 0x11:                                  return 30;
            default: return 0;
        }
    }

    void DCF77_Encoder::reset() {
        second      = 0;
        minute.val  = 0x00;
        hour.val    = 0x00;
        day.val     = 0x01;
        month.val   = 0x01;
        year.val    = 0x00;
        weekday.val = 0x01;
        uses_summertime                = false;
        abnormal_transmitter_operation = false;
        timezone_change_scheduled      = false;
        leap_second_scheduled          = false;

        undefined_minute_output                         = false;
        undefined_uses_summertime_output                = false;
        undefined_abnormal_transmitter_operation_output = false;
        undefined_timezone_change_scheduled_output      = false;
    }

    uint8_t DCF77_Encoder::get_weekday() const {
        // attention: sunday will be ==0 instead of 7
        using namespace BCD;

        if (day.val <= 0x31 && month.val <= 0x12 && year.val <= 0x99) {
            // This will compute the weekday for each year in 2001-2099.
            // If you really plan to use my code beyond 2099 take care of this
            // on your own. My assumption is that it is even unclear if DCF77
            // will still exist then.

            // http://de.wikipedia.org/wiki/Gau%C3%9Fsche_Wochentagsformel
            const uint8_t  d = bcd_to_int(day);
            const uint16_t m = month.val <= 0x02? month.val + 10:
            bcd_to_int(month) - 2;
            const uint8_t  y = bcd_to_int(year) - (month.val <= 0x02);
            // m must be of type uint16_t otherwise this will compute crap
            uint8_t day_mod_7 = d + (26*m - 2)/10 + y + y/4;
            // We exploit 8 mod 7 = 1
            while (day_mod_7 >= 7) {
                day_mod_7 -= 7;
                day_mod_7 = (day_mod_7 >> 3) + (day_mod_7 & 7);
            }

            return day_mod_7;  // attention: sunday will be == 0 instead of 7
        } else {
            return 0xff;
        }
    }

    BCD::bcd_t DCF77_Encoder::get_bcd_weekday() const {
        BCD::bcd_t today;

        today.val = get_weekday();
        if (today.val == 0) {
            today.val = 7;
        }

        return today;
    }

    void DCF77_Encoder::autoset_weekday() {
        weekday = get_bcd_weekday();
    }

    void DCF77_Encoder::autoset_timezone() {
        // timezone change may only happen at the last sunday of march / october
        // the last sunday is always somewhere in [25-31]

        // Wintertime --> Summertime happens at 01:00 UTC == 02:00 CET == 03:00 CEST,
        // Summertime --> Wintertime happens at 01:00 UTC == 02:00 CET == 03:00 CEST

        if (month.val < 0x03) {
            // January or February
            uses_summertime = false;
        } else
        if (month.val == 0x03) {
            // March
            if (day.val < 0x25) {
                // Last Sunday of March must be 0x25-0x31
                // Thus still to early for summertime
                uses_summertime = false;
            } else
            if (uint8_t wd = get_weekday()) {
                // wd != 0 --> not a Sunday
                if (day.val - wd < 0x25) {
                    // early March --> wintertime
                    uses_summertime = false;
                } else {
                    // late march summertime
                    uses_summertime = true;
                }
            } else {
                // last sunday of march
                // decision depends on the current hour
                uses_summertime = (hour.val >= 2);
            }
        } else
            if (month.val < 0x10) {
                // April - September
                uses_summertime = true;
            } else
            if (month.val == 0x10) {
                // October
                if (day.val < 0x25) {
                    // early October
                    uses_summertime = true;
                } else
                if (uint8_t wd = get_weekday()) {
                    // wd != 0 --> not a Sunday
                    if (day.val - wd < 0x25) {
                        // early October --> summertime
                        uses_summertime = true;
                    } else {
                        // late October --> wintertime
                        uses_summertime = false;
                    }
                } else {  // last sunday of october
                if (hour.val == 2) {
                    // can not derive the flag from time data
                    // this is the only time the flag is derived
                    // from the flag vector
                } else {
                    // decision depends on the current hour
                    uses_summertime = (hour.val < 2);
                }
            }
        } else {
            // November and December
            uses_summertime = false;
        }
    }

    void DCF77_Encoder::autoset_timezone_change_scheduled() {
        // summer/wintertime change will always happen
        // at clearly defined hours
        // http://www.gesetze-im-internet.de/sozv/__2.html
        // in doubt have a look here: http://www.dcf77logs.de/
        if (day.val < 0x25 || get_weekday() != 0) {
            // timezone change may only happen at the last sunday of march / october
            // the last sunday is always somewhere in [25-31]

            // notice that undefined (==0xff) day/weekday data will not cause any action
            timezone_change_scheduled = false;
        } else {
            if (month.val == 0x03) {
                if (uses_summertime) {
                    timezone_change_scheduled = (hour.val == 0x03 && minute.val == 0x00); // wintertime to summertime, preparing first minute of summertime
                } else {
                    timezone_change_scheduled = (hour.val == 0x01 && minute.val != 0x00); // wintertime to summertime
                }
            } else if (month.val == 0x10) {
                if (uses_summertime) {
                    timezone_change_scheduled = (hour.val == 0x02 && minute.val != 0x00); // summertime to wintertime
                } else {
                    timezone_change_scheduled = (hour.val == 0x02 && minute.val == 0x00); // summertime to wintertime, preparing first minute of wintertime
                }
            } else if (month.val <= 0x12) {
                timezone_change_scheduled = false;
            }
        }
    }

    bool DCF77_Encoder::verify_leap_second_scheduled(const bool assume_leap_second) const {
        // If day or month are unknown we default to "no leap second" because this is alway a very good guess.
        // If we do not know for sure we are either acquiring a lock right now --> we will easily recover from a wrong guess
        // or we have very noisy data --> the leap second bit is probably noisy as well --> we should assume the most likely case

        bool leap_second_scheduled = day.val == 0x01 && (assume_leap_second || this->leap_second_scheduled);

        // leap seconds will always happen
        // after 23:59:59 UTC and before 00:00 UTC == 01:00 CET == 02:00 CEST
        if (month.val == 0x01) {
            leap_second_scheduled &= ((hour.val == 0x00 && minute.val != 0x00) ||
                                      (hour.val == 0x01 && minute.val == 0x00));
        } else if (month.val == 0x07 || month.val == 0x04 || month.val == 0x10) {
            leap_second_scheduled &= ((hour.val == 0x01 && minute.val != 0x00) ||
                                      (hour.val == 0x02 && minute.val == 0x00));
        } else {
            leap_second_scheduled = false;
        }

        return leap_second_scheduled;
    }

    void DCF77_Encoder::autoset_control_bits() {
        autoset_weekday();
        autoset_timezone();
        autoset_timezone_change_scheduled();
        // we can not compute leap seconds, we can only verify if they might happen
        leap_second_scheduled = verify_leap_second_scheduled(false);
    }

    void DCF77_Encoder::advance_minute() {
        if (minute.val < 0x59) {
            increment(minute);
        } else if (minute.val == 0x59) {
            minute.val = 0x00;
            // in doubt have a look here: http://www.dcf77logs.de/
            if (timezone_change_scheduled && !uses_summertime && hour.val == 0x01) {
                // Wintertime --> Summertime happens at 01:00 UTC == 02:00 CET == 03:00 CEST,
                // the clock must be advanced from 01:59 CET to 03:00 CEST
                increment(hour);
                increment(hour);
                uses_summertime = true;
            }  else if (timezone_change_scheduled && uses_summertime && hour.val == 0x02) {
                // Summertime --> Wintertime happens at 01:00 UTC == 02:00 CET == 03:00,
                // the clock must be advanced from 02:59 CEST to 02:00 CET
                uses_summertime = false;
            } else {
                if (hour.val < 0x23) {
                    increment(hour);
                } else if (hour.val == 0x23) {
                    hour.val = 0x00;

                    if (weekday.val < 0x07) {
                        increment(weekday);
                    } else if (weekday.val == 0x07) {
                        weekday.val = 0x01;
                    }

                    if (bcd_to_int(day) < days_per_month()) {
                        increment(day);
                    } else if (bcd_to_int(day) == days_per_month()) {
                        day.val = 0x01;

                        if (month.val < 0x12) {
                            increment(month);
                        } else if (month.val == 0x12) {
                            month.val = 0x01;

                            if (year.val < 0x99) {
                                increment(year);
                            } else if (year.val == 0x99) {
                                year.val = 0x00;
                            }
                        }
                    }
                }
            }
        }
    }

    void DCF77_Encoder::advance_second() {
        // in case some value is out of range it will not be advanced
        // this is on purpose
        if (second < 59) {
            ++second;
            if (second == 15) {
                autoset_control_bits();
            }

        } else if (leap_second_scheduled && second == 59 && minute.val == 0x00) {
            second = 60;
            leap_second_scheduled = false;
        } else if (second == 59 || second == 60) {
            second = 0;
            advance_minute();
        }
    }

    DCF77::tick_t DCF77_Encoder::get_current_signal() const {
        using namespace DCF77;
        using namespace Arithmetic_Tools;

        if (second >= 1 && second <= 14) {
            // weather data or other stuff we can not compute
            return undefined;
        }

        bool result;
        switch (second) {
            case 0:  // start of minute
                return short_tick;

            case 15:
                if (undefined_abnormal_transmitter_operation_output) { return undefined; }
                result = abnormal_transmitter_operation; break;

            case 16:
                if (undefined_timezone_change_scheduled_output) { return undefined; }
                result = timezone_change_scheduled; break;

            case 17:
                if (undefined_uses_summertime_output) {return undefined; }
                result = uses_summertime; break;

            case 18:
                if (undefined_uses_summertime_output) {return undefined; }
                result = !uses_summertime; break;

            case 19:
                result = leap_second_scheduled; break;

            case 20:  // start of time information
                return long_tick;

            case 21:
                if (undefined_minute_output || minute.val > 0x59) { return undefined; }
                result = minute.digit.lo & 0x1; break;
            case 22:
                if (undefined_minute_output || minute.val > 0x59) { return undefined; }
                result = minute.digit.lo & 0x2; break;
            case 23:
                if (undefined_minute_output || minute.val > 0x59) { return undefined; }
                result = minute.digit.lo & 0x4; break;
            case 24:
                if (undefined_minute_output || minute.val > 0x59) { return undefined; }
                result = minute.digit.lo & 0x8; break;

            case 25:
                if (undefined_minute_output || minute.val > 0x59) { return undefined; }
                result = minute.digit.hi & 0x1; break;
            case 26:
                if (undefined_minute_output || minute.val > 0x59) { return undefined; }
                result = minute.digit.hi & 0x2; break;
            case 27:
                if (undefined_minute_output || minute.val > 0x59) { return undefined; }
                result = minute.digit.hi & 0x4; break;

            case 28:
                if (undefined_minute_output || minute.val > 0x59) { return undefined; }
                result = parity(minute.val); break;


            case 29:
                if (hour.val > 0x23) { return undefined; }
                result = hour.digit.lo & 0x1; break;
            case 30:
                if (hour.val > 0x23) { return undefined; }
                result = hour.digit.lo & 0x2; break;
            case 31:
                if (hour.val > 0x23) { return undefined; }
                result = hour.digit.lo & 0x4; break;
            case 32:
                if (hour.val > 0x23) { return undefined; }
                result = hour.digit.lo & 0x8; break;

            case 33:
                if (hour.val > 0x23) { return undefined; }
                result = hour.digit.hi & 0x1; break;
            case 34:
                if (hour.val > 0x23) { return undefined; }
                result = hour.digit.hi & 0x2; break;

            case 35:
                if (hour.val > 0x23) { return undefined; }
                result = parity(hour.val); break;

            case 36:
                if (day.val > 0x31) { return undefined; }
                result = day.digit.lo & 0x1; break;
            case 37:
                if (day.val > 0x31) { return undefined; }
                result = day.digit.lo & 0x2; break;
            case 38:
                if (day.val > 0x31) { return undefined; }
                result = day.digit.lo & 0x4; break;
            case 39:
                if (day.val > 0x31) { return undefined; }
                result = day.digit.lo & 0x8; break;

            case 40:
                if (day.val > 0x31) { return undefined; }
                result = day.digit.hi & 0x1; break;
            case 41:
                if (day.val > 0x31) { return undefined; }
                result = day.digit.hi & 0x2; break;

            case 42:
                if (weekday.val > 0x7) { return undefined; }
                result = weekday.val & 0x1; break;
            case 43:
                if (weekday.val > 0x7) { return undefined; }
                result = weekday.val & 0x2; break;
            case 44:
                if (weekday.val > 0x7) { return undefined; }
                result = weekday.val & 0x4; break;

            case 45:
                if (month.val > 0x12) { return undefined; }
                result = month.digit.lo & 0x1; break;
            case 46:
                if (month.val > 0x12) { return undefined; }
                result = month.digit.lo & 0x2; break;
            case 47:
                if (month.val > 0x12) { return undefined; }
                result = month.digit.lo & 0x4; break;
            case 48:
                if (month.val > 0x12) { return undefined; }
                result = month.digit.lo & 0x8; break;

            case 49:
                if (month.val > 0x12) { return undefined; }
                result = month.digit.hi & 0x1; break;

            case 50:
                if (year.val > 0x99) { return undefined; }
                result = year.digit.lo & 0x1; break;
            case 51:
                if (year.val > 0x99) { return undefined; }
                result = year.digit.lo & 0x2; break;
            case 52:
                if (year.val > 0x99) { return undefined; }
                result = year.digit.lo & 0x4; break;
            case 53:
                if (year.val > 0x99) { return undefined; }
                result = year.digit.lo & 0x8; break;

            case 54:
                if (year.val > 0x99) { return undefined; }
                result = year.digit.hi & 0x1; break;
            case 55:
                if (year.val > 0x99) { return undefined; }
                result = year.digit.hi & 0x2; break;
            case 56:
                if (year.val > 0x99) { return undefined; }
                result = year.digit.hi & 0x4; break;
            case 57:
                if (year.val > 0x99) { return undefined; }
                result = year.digit.hi & 0x8; break;

            case 58:
                if (weekday.val > 0x07 ||
                    day.val     > 0x31 ||
                    month.val   > 0x12 ||
                    year.val    > 0x99) { return undefined; }

                    result = parity(day.digit.lo)   ^
                             parity(day.digit.hi)   ^
                             parity(month.digit.lo) ^
                             parity(month.digit.hi) ^
                             parity(weekday.val)    ^
                             parity(year.digit.lo)  ^
                             parity(year.digit.hi); break;

            case 59:
                // special handling for leap seconds
                if (leap_second_scheduled && minute.val == 0) { result = 0; break; }
                return sync_mark;
            case 60:
                return sync_mark;

            default:
                return undefined;
        }

        return result? long_tick: short_tick;
    }

    void DCF77_Encoder::get_serialized_clock_stream(DCF77::serialized_clock_stream &data) const {
        using namespace Arithmetic_Tools;

        // bit 16-20  // flags
        data.byte_0 = 0;
        data.byte_0 = set_bit(data.byte_0, 3, timezone_change_scheduled );
        data.byte_0 = set_bit(data.byte_0, 4, uses_summertime);
        data.byte_0 = set_bit(data.byte_0, 5, !uses_summertime);
        data.byte_0 = set_bit(data.byte_0, 6, leap_second_scheduled);
        data.byte_0 = set_bit(data.byte_0, 7, 1);

        // bit 21-28  // minutes
        data.byte_1 = set_bit(minute.val, 7, parity(minute.val));

        // bit 29-36  // hours, bit 0 of day
        data.byte_2 = set_bit(hour.val, 6, parity(hour.val));
        data.byte_2 = set_bit(data.byte_2, 7, day.bit.b0);


        // bit 37-44  // day + weekday
        data.byte_3 = day.val>>1 | weekday.val<<5;

        // bit 45-52  // month + bit 0-2 of year
        data.byte_4 = month.val | year.val<<5;

        const uint8_t date_parity = parity(day.digit.lo)   ^
                                    parity(day.digit.hi)   ^
                                    parity(month.digit.lo) ^
                                    parity(month.digit.hi) ^
                                    parity(weekday.val)    ^
                                    parity(year.digit.lo)  ^
                                    parity(year.digit.hi);
        // bit 53-58  // year + parity
        data.byte_5 = set_bit(year.val>>3, 5, date_parity);
    }

    void DCF77_Encoder::debug() const {
        using namespace Debug;

        sprint(F("  "));
        bcddigits(year.val);
        sprint('.');
        bcddigits(month.val);
        sprint('.');
        bcddigits(day.val);
        sprint('(');
        bcddigit(weekday.val);
        sprint(',');
        bcddigit(get_weekday());
        sprint(')');
        bcddigits(hour.val);
        sprint(':');
        bcddigits(minute.val);
        sprint(':');
        if (second < 10) {
            sprint('0');
        }
        sprint(second, DEC);
        if (uses_summertime) {
            sprint(F(" CEST "));
        } else {
            sprint(F(" CET "));
        }
        sprint(leap_second_scheduled);
        sprint(',');
        sprint(timezone_change_scheduled);
        sprint(' ');
    }

    void DCF77_Encoder::debug(const uint16_t cycles) const {
        DCF77_Encoder local_clock = *this;
        DCF77_Encoder decoded_clock;

        sprint(F("M ?????????????? RAZZA S mmmmMMMP hhhhHHP ddddDD www mmmmM yyyyYYYYP S"));
        for (uint16_t second = 0; second < cycles; ++second) {
            switch (local_clock.second) {
                case  0: sprintln(); break;
                case  1: case 15: case 20: case 21: case 29:
                case 36: case 42: case 45: case 50: case 59: sprint(' ');
            }

            const DCF77::tick_t tick_data = local_clock.get_current_signal();
            Debug::debug_helper(tick_data);

            DCF77_Naive_Bitstream_Decoder::set_bit(local_clock.second, tick_data, decoded_clock);

            local_clock.advance_second();

            if (local_clock.second == 0) {
                decoded_clock.debug();
            }
        }

        sprintln();
        sprintln();
    }
}

namespace Internal {
    namespace DCF77_Naive_Bitstream_Decoder {
        using namespace DCF77;

        void set_bit(const uint8_t second, const uint8_t value, DCF77_Encoder &now) {
            // The naive value is a way to guess a value for unclean decoded data.
            // It is obvious that this is not necessarily a good value but better
            // than nothing.
            const uint8_t naive_value = (value == long_tick || value == undefined)? 1: 0;
            const uint8_t is_value_bad = value != long_tick && value != short_tick;

            now.second = second;

            switch (second) {
                case 15: now.abnormal_transmitter_operation = naive_value; break;
                case 16: now.timezone_change_scheduled      = naive_value; break;

                case 17:
                    now.uses_summertime = naive_value;
                    now.undefined_uses_summertime_output = is_value_bad;
                    break;

                case 18:
                    if (now.uses_summertime == naive_value) {
                        // if values of bit 17 and 18 match we will enforce a mapping
                        if (!is_value_bad) {
                            now.uses_summertime = !naive_value;
                        }
                    }
                    now.undefined_uses_summertime_output = false;
                    break;

                case 19:
                    // leap seconds are seldom, in doubt we assume none is scheduled
                    now.leap_second_scheduled = naive_value && !is_value_bad;
                    break;


                case 20:
                    // start to decode minute data
                    now.minute.val = 0x00;
                    now.undefined_minute_output = false;
                    break;

                case 21: now.minute.val +=      naive_value; break;
                case 22: now.minute.val +=  0x2*naive_value; break;
                case 23: now.minute.val +=  0x4*naive_value; break;
                case 24: now.minute.val +=  0x8*naive_value; break;
                case 25: now.minute.val += 0x10*naive_value; break;
                case 26: now.minute.val += 0x20*naive_value; break;
                case 27: now.minute.val += 0x40*naive_value; break;

                case 28: now.hour.val = 0; break;
                case 29: now.hour.val +=      naive_value; break;
                case 30: now.hour.val +=  0x2*naive_value; break;
                case 31: now.hour.val +=  0x4*naive_value; break;
                case 32: now.hour.val +=  0x8*naive_value; break;
                case 33: now.hour.val += 0x10*naive_value; break;
                case 34: now.hour.val += 0x20*naive_value; break;

                case 35:
                    now.day.val = 0x00;
                    now.month.val = 0x00;
                    now.year.val = 0x00;
                    now.weekday.val = 0x00;
                    break;

                case 36: now.day.val +=      naive_value; break;
                case 37: now.day.val +=  0x2*naive_value; break;
                case 38: now.day.val +=  0x4*naive_value; break;
                case 39: now.day.val +=  0x8*naive_value; break;
                case 40: now.day.val += 0x10*naive_value; break;
                case 41: now.day.val += 0x20*naive_value; break;

                case 42: now.weekday.val +=     naive_value; break;
                case 43: now.weekday.val += 0x2*naive_value; break;
                case 44: now.weekday.val += 0x4*naive_value; break;

                case 45: now.month.val +=      naive_value; break;
                case 46: now.month.val +=  0x2*naive_value; break;
                case 47: now.month.val +=  0x4*naive_value; break;
                case 48: now.month.val +=  0x8*naive_value; break;
                case 49: now.month.val += 0x10*naive_value; break;

                case 50: now.year.val +=      naive_value; break;
                case 51: now.year.val +=  0x2*naive_value; break;
                case 52: now.year.val +=  0x4*naive_value; break;
                case 53: now.year.val +=  0x8*naive_value; break;
                case 54: now.year.val += 0x10*naive_value; break;
                case 55: now.year.val += 0x20*naive_value; break;
                case 56: now.year.val += 0x40*naive_value; break;
                case 57: now.year.val += 0x80*naive_value; break;
            }
        }
    }
}

namespace Internal {  // DCF77_Clock_Controller<Configuration, Frequency_Control>
    // static member definitions for DCF77_Clock_Controller<Configuration, Frequency_Control>
    template <typename Configuration, typename Frequency_Control> Clock::output_handler_t DCF77_Clock_Controller<Configuration, Frequency_Control>::output_handler = 0;

    template <typename Configuration, typename Frequency_Control> DCF77_Second_Decoder  DCF77_Clock_Controller<Configuration, Frequency_Control>::Second_Decoder;
    template <typename Configuration, typename Frequency_Control> DCF77_Minute_Decoder  DCF77_Clock_Controller<Configuration, Frequency_Control>::Minute_Decoder;
    template <typename Configuration, typename Frequency_Control> DCF77_Hour_Decoder    DCF77_Clock_Controller<Configuration, Frequency_Control>::Hour_Decoder;
    template <typename Configuration, typename Frequency_Control> DCF77_Weekday_Decoder DCF77_Clock_Controller<Configuration, Frequency_Control>::Weekday_Decoder;
    template <typename Configuration, typename Frequency_Control> DCF77_Day_Decoder     DCF77_Clock_Controller<Configuration, Frequency_Control>::Day_Decoder;
    template <typename Configuration, typename Frequency_Control> DCF77_Month_Decoder   DCF77_Clock_Controller<Configuration, Frequency_Control>::Month_Decoder;
    template <typename Configuration, typename Frequency_Control> DCF77_Year_Decoder    DCF77_Clock_Controller<Configuration, Frequency_Control>::Year_Decoder;
    template <typename Configuration, typename Frequency_Control> DCF77_Flag_Decoder    DCF77_Clock_Controller<Configuration, Frequency_Control>::Flag_Decoder;

    template <typename Configuration, typename Frequency_Control> uint8_t       DCF77_Clock_Controller<Configuration, Frequency_Control>::leap_second;
    template <typename Configuration, typename Frequency_Control> DCF77_Encoder DCF77_Clock_Controller<Configuration, Frequency_Control>::decoded_time;

    template <typename Configuration, typename Frequency_Control> DCF77_Local_Clock<DCF77_Clock_Controller<Configuration, Frequency_Control> >
        DCF77_Clock_Controller<Configuration, Frequency_Control>::Local_Clock;

    template <typename Configuration, typename Frequency_Control> DCF77_Demodulator<DCF77_Clock_Controller<Configuration, Frequency_Control> >
        DCF77_Clock_Controller<Configuration, Frequency_Control>::Demodulator;
}

namespace DCF77_Clock {
    using namespace Internal;

    typedef DCF77_Clock_Controller<Configuration, DCF77_Frequency_Control> Clock_Controller;

    void setup() {
        Clock_Controller::setup();
    }

    void setup(const Clock::input_provider_t input_provider) {
        Clock_Controller::setup();
        // Clock_Controller::set_output_handler(output_handler);
        Generic_1_kHz_Generator::setup(input_provider);
    }

    void debug() {
        Clock_Controller::debug();
    }

    void set_input_provider(const Clock::input_provider_t input_provider) {
        Generic_1_kHz_Generator::setup(input_provider);
    }

    void set_output_handler(const Clock::output_handler_t output_handler) {
        Clock_Controller::set_output_handler(output_handler);
    }

    void convert_time(const DCF77_Encoder &current_time, Clock::time_t &now) {
        now.second                    = BCD::int_to_bcd(current_time.second);
        now.minute                    = current_time.minute;
        now.hour                      = current_time.hour;
        now.weekday                   = current_time.weekday;
        now.day                       = current_time.day;
        now.month                     = current_time.month;
        now.year                      = current_time.year;
        now.uses_summertime           = current_time.uses_summertime;
        now.leap_second_scheduled     = current_time.leap_second_scheduled;
        now.timezone_change_scheduled = current_time.timezone_change_scheduled;
    }

    void get_current_time(Clock::time_t &now) {
        DCF77_Encoder current_time;
        Clock_Controller::get_current_time(current_time);

        convert_time(current_time, now);
    }

    void read_current_time(Clock::time_t &now) {
        DCF77_Encoder current_time;
        Clock_Controller::read_current_time(current_time);

        convert_time(current_time, now);
    }

    void read_future_time(Clock::time_t &now_plus_1s) {
        DCF77_Encoder current_time;
        Clock_Controller::read_current_time(current_time);
        current_time.advance_second();

        convert_time(current_time, now_plus_1s);
    }

    void set_current_time(const Clock::time_t &time) {
        DCF77_Encoder encoder;
        encoder.reset();

        encoder.second  = BCD::bcd_to_int(time.second);
        encoder.minute  = time.minute;
        encoder.hour    = time.hour;
        encoder.day     = time.day;
        encoder.month   = time.month;
        encoder.year    = time.year;
        encoder.weekday = time.weekday;

        encoder.autoset_weekday();
        encoder.autoset_control_bits();

        CRITICAL_SECTION {
            Clock_Controller::Local_Clock.local_clock_time = encoder;
            Clock_Controller::Local_Clock.clock_state      = Clock::dirty;
            Clock_Controller::Local_Clock.tick             = 0;
        }
    }

    void print(Clock::time_t time) {
        BCD::print(time.year);
        sprint('-');
        BCD::print(time.month);
        sprint('-');
        BCD::print(time.day);
        sprint(' ');
        sprint(time.weekday.val & 0xF, HEX);
        sprint(' ');
        BCD::print(time.hour);
        sprint(':');
        BCD::print(time.minute);
        sprint(':');
        BCD::print(time.second);

        if (time.uses_summertime) {
            sprint(F(" CEST "));
        } else {
            sprint(F(" CET "));
        }

        sprint(time.timezone_change_scheduled? '*': '.');
        sprint(time.leap_second_scheduled    ? 'L': '.');
    }

    uint8_t get_overall_quality_factor() {
        return Clock_Controller::get_overall_quality_factor();
    }

    Clock::clock_state_t get_clock_state() {
        return Clock_Controller::get_clock_state();
    }

    uint8_t get_prediction_match() {
        return Clock_Controller::get_prediction_match();
    }
}

namespace Internal {  // DCF77_Frequency_Control
    volatile int8_t DCF77_Frequency_Control::confirmed_precision = 0;
    // get the adjust step that was used for the last adjustment
    //   if there was no adjustment or if the phase drift was poor it will return 0
    int8_t DCF77_Frequency_Control::get_confirmed_precision() {
        return confirmed_precision;
    }

    void DCF77_Frequency_Control::qualify_calibration() {
        calibration_state.qualified = true;
    }

    void DCF77_Frequency_Control::unqualify_calibration() {
        calibration_state.qualified = false;
    }

    DCF77_Frequency_Control::deviation_tracker_t DCF77_Frequency_Control::deviation_tracker;
    int16_t DCF77_Frequency_Control::compute_phase_deviation(uint8_t current_second, uint8_t current_minute_mod_10) {
        return deviation_tracker.compute_phase_deviation(current_second, current_minute_mod_10);
    }

    volatile DCF77_Frequency_Control::calibration_state_t DCF77_Frequency_Control::calibration_state = {false ,false};
    DCF77_Frequency_Control::calibration_state_t DCF77_Frequency_Control::get_calibration_state() {
        return *(calibration_state_t *)&calibration_state;
    }

    volatile int16_t DCF77_Frequency_Control::deviation;
    int16_t DCF77_Frequency_Control::get_current_deviation() {
        return deviation;
    }

    void DCF77_Frequency_Control::adjust() {
        int16_t total_adjust = Generic_1_kHz_Generator::read_adjustment();
        // The proper formula would be
        //     int32_t adjust == (16 000 000 / (elapsed_minutes * 60 * phase_lock_resolution)) * new_deviation;
        // The total error of the formula below is ~ 1/(3*elapsed_minutes)
        //     which is  ~ 1/1000 (for centisecond resolution) and ~1/100 for millisecond resolution
        // Also notice that 2667*deviation will not overflow even if the
        // local clock would deviate by more than 400 ppm or 6 kHz
        // from its nominal frequency.
        // Finally notice that the frequency_offset will always be rounded towards zero
        // while the confirmed_precision is rounded away from zero. The first should
        // be considered a kind of relaxation while the second should be considered
        // a defensive computation.
        const int16_t minutes_per_16000000_ticks = 16000000uL / 60 / Configuration::phase_lock_resolution;
        const int16_t frequency_offset = ((minutes_per_16000000_ticks * (int32_t)deviation) /
                                           deviation_tracker.elapsed_minutes);
        // In doubt confirmed precision will be slightly larger than the true value
        confirmed_precision = ((minutes_per_16000000_ticks - 1) + deviation_tracker.elapsed_minutes) /
                                deviation_tracker.elapsed_minutes;
        if (confirmed_precision == 0) { confirmed_precision = 1; }

        total_adjust -= frequency_offset;

        if (total_adjust >  max_total_adjust) { total_adjust =  max_total_adjust; }
        if (total_adjust < -max_total_adjust) { total_adjust = -max_total_adjust; }

        Generic_1_kHz_Generator::adjust(total_adjust);
    }

    void DCF77_Frequency_Control::process_1_Hz_tick(const DCF77_Encoder &decoded_time) {
        const int16_t deviation_to_trigger_readjust = 5;

        deviation = compute_phase_deviation(decoded_time.second, decoded_time.minute.digit.lo);

        if (decoded_time.second == calibration_second) {
            // We might be in an unqualified state and thus the leap second information
            // we have might be wrong.
            // However if we fail to detect an actual leap second, calibration will be wrong
            // by 1 second.
            // Therefore we assume a leap second and verify_leap_second_scheduled()
            // will tell us if our assumption could actually be a leap second.
            if (decoded_time.verify_leap_second_scheduled(true)) {
                // Leap seconds will mess up our frequency computations.
                // Handling them properly would be slightly more complicated.
                // Since leap seconds may only happen every 3 months we just
                // stop calibration for leap seconds and do nothing else.
                calibration_state.running = false;
            }

            if (calibration_state.running) {
                if (calibration_state.qualified) {
                    if ((Configuration::has_stable_ambient_temperature && deviation_tracker.good_enough() && ABS(deviation) >= deviation_to_trigger_readjust) ||
                         deviation_tracker.timeout()) {
                        adjust();
                        DCF77_Clock_Controller<Configuration, DCF77_Frequency_Control>::on_tuned_clock();

                        // restart calibration next second
                        calibration_state.running = false;
                    }
                } else {
                    // unqualified
                    if (deviation_tracker.timeout()) {
                        // running unqualified for more than tau minutes
                        //   --> the current calibration attempt is doomed
                        calibration_state.running = false;
                    }
                    // else running but unqualified --> wait for better state
                }
            } else {
                // (calibration_state.running == false) --> waiting
                if (calibration_state.qualified) {
                    deviation_tracker.start(decoded_time.minute.digit.lo);
                    calibration_state.running = true;
                }
                // else waiting but unqualified --> nothing to do
            }
        }
    }

    void DCF77_Frequency_Control::process_1_kHz_tick() {
        deviation_tracker.process_tick();
    }

    void DCF77_Frequency_Control::setup() {}

    void DCF77_Frequency_Control::debug() {
        using namespace Debug;
        sprintln(F("confirmed_precision ?? adjustment, deviation, elapsed"));
        sprintpp16m(confirmed_precision);
        sprint(F(", "));
        sprint(calibration_state.running? '@': '.');
        sprint(calibration_state.qualified? '+': '-');
        sprint(' ');

        sprint(F(", "));
        sprintpp16m(Generic_1_kHz_Generator::read_adjustment());
        sprint(F(", "));

        sprint(deviation);
        sprint(F(" ticks, "));

        sprint(deviation_tracker.elapsed_minutes);
        sprint(F(" min + "));
        sprint(deviation_tracker.elapsed_ticks_mod_60000);
        sprintln(F(" ticks mod 60000"));
    }

    void DCF77_No_Frequency_Control::process_1_Hz_tick() {}
    void DCF77_No_Frequency_Control::process_1_kHz_tick() {}
    void DCF77_No_Frequency_Control::qualify_calibration() {}
    void DCF77_No_Frequency_Control::unqualify_calibration() {}
    void DCF77_No_Frequency_Control::setup() {}
}

namespace Internal {
    namespace Generic_1_kHz_Generator {
        uint8_t zero_provider() {
            return 0;
        }

        static Clock::input_provider_t the_input_provider = zero_provider;
        static int16_t adjust_pp16m = 0;
        static int32_t cumulated_phase_deviation = 0;

        void adjust(const int16_t pp16m) {
             {
                // positive_value --> increase frequency
                adjust_pp16m = pp16m;
            }
        }

        int16_t read_adjustment() {
            // positive_value --> increase frequency
            CRITICAL_SECTION {
                const int16_t pp16m = adjust_pp16m;
                return pp16m;
            }
            // #if defined(ARDUINO_ARCH_ESP8266)
            //Workaround to [-Werror=return-type]
            return 0;
            // #endif
        }

        #if defined(__AVR_ATmega168__)  || \
            defined(__AVR_ATmega48__)   || \
            defined(__AVR_ATmega88__)   || \
            defined(__AVR_ATmega328P__) || \
            defined(__AVR_ATmega1280__) || \
            defined(__AVR_ATmega2560__) || \
            defined(__AVR_AT90USB646__) || \
            defined(__AVR_AT90USB1286__)

        // 249 + 1 == 250 == 250 000 / 1000 =  (16 000 000 / 64) / 1000
        // For 16 MHz this will result in 1 ms ticks, for 8 Mhz it will result
        // in 2 ms ticks.
        const uint8_t OCR2A_standard = 249;
        #if (F_CPU == 16000000L) or (F_CPU == 8000000L)
            // 250 / 16 000 000 = 1 / 64 000
            const uint16_t inverse_timer_resolution = 64000uL;
        #else
            #error Unsupported CPU clock frequency, only 8 MHz or 16 MHz clocks are supported.
        #endif
        const uint8_t OCR2A_slower = OCR2A_standard + 1;
        const uint8_t OCR2A_faster = OCR2A_standard - 1;

        void setup(const Clock::input_provider_t input_provider) {
            the_input_provider = input_provider;
        }

        void isr_handler() {
            cumulated_phase_deviation += adjust_pp16m;
            // 250 / 16 000 000 = 1 / 64 000
            if (cumulated_phase_deviation >= inverse_timer_resolution) {
                cumulated_phase_deviation -= inverse_timer_resolution;
                // cumulated drift exceeds 1 timer step
                // drop one timer step to realign
                OCR2A = OCR2A_faster;
            } else
            if (cumulated_phase_deviation <= -inverse_timer_resolution) {
                // cumulated drift exceeds 1 timer step
                // insert one timer step to realign
                cumulated_phase_deviation += inverse_timer_resolution;
                OCR2A = OCR2A_slower;
            } else {
                OCR2A = OCR2A_standard;
            }

            Clock_Controller::process_1_kHz_tick_data(the_input_provider());
        }
        #endif
    }
}
