Servacek/numeri/firmver/src/edit.cpp

#include "utils/math.h"

#include "utils/utils.h"
#include "clock.h"
#include "edit.h"
#include "services/logging.h"
#include "services/views.h"
#include "modules.h"
#include "drivers/display.h"
#include "drivers/led.h"
#include "timers.h"
#include "const.h"
#include "fading.h"
#include "state.h"
#include "night_mode.h"
#include "services/sync.h"


namespace Edit {

//////////////////////////////
/// Sukromne premenne
//////////////////////////////

static uint8_t  _cur_page_index = 0;
static uint16_t _idle_seconds   = 0;

// Zaciname nastavovat cas od desiatok hodin.
static uint8_t  _selected_digit = DIGIT_HOR_TENS;

// Pocet stranok dostupnych uzivatelovi (vynechava interne stranky ulozenia casovacov).
static constexpr uint8_t _USER_PAGE_COUNT = Config::YEAR_D1 / CONFIG_PAGE_SIZE + 1u;

// Dlhe drzanie prav. tlacidla pri minimalnom jase - vstup do nocneho rezimu.
static uint8_t _night_hold_cnt = 0;
static constexpr uint8_t _NIGHT_MODE_HOLD_TICKS = 3;

static bool _time_page_dirty = false;
static bool _date_page_dirty = false;
static bool _year_page_dirty = false;

//////////////////////////////
/// Sukromne funkcie
//////////////////////////////

bool isEditingLedBrightness() {
    return _cur_page_index == Config::page(Config::LED_BRIGHTNESS_LEVEL)
        && _selected_digit  == Config::indexInPage(Config::LED_BRIGHTNESS_LEVEL);
}

// Pocas editacie jasu LED-ky drzime LED-ku zamknutu na bielej, aby ju
// ziadny iny vlastnik (DCF77 sync, atd.) nemohol pocas preview prepisat.
static void _updateLedPreview() {
    Led::unlock(); // bezpecne aj ak nebola zamknuta
    if (isEditingLedBrightness()) {
        Led::setRGB(255, 255, 255);
        Led::lock();
    } else {
        Led::setRGB(0, 0, 0);
    }
}

static void _setSelectedDigit(uint8_t digit) {
    // Presunieme kurzor na novu vybranu cifru.
    Display::addNumitronSegmentMask(_selected_digit, S2, OFF);
    Display::addNumitronSegmentMask(digit, S2, ON);
    _selected_digit = digit;
    _updateLedPreview();
}

static void _setSymbolOnNumitronWithCursor(uint8_t numitron_index, uint8_t symbol_index) {
    Display::setSymbolOnNumitron(numitron_index, symbol_index);
    if (numitron_index == _selected_digit && Clock::State::inEditMode()) {
        Display::_DIGITS[numitron_index] |= S2; // Uistime sa, ze kurzor je vzdy viditelny.
    }
}

static void _displayConfigPage(uint8_t page_index) {
    sprint("STRANKA: ");
    sprint(page_index);
    sprint(" HODNOTY NUMITRONOV:");
    for (uint8_t conf_index = 0; conf_index < CONFIG_PAGE_SIZE; conf_index++) {
        sprint(" ");
        sprint(Config::get(Config::toID(page_index, conf_index)));
        _setSymbolOnNumitronWithCursor(
            conf_index, Config::get(Config::toID(page_index, conf_index))
        );
    }
    sprintln("");

    Display::Crossfading::startTransition();
    _updateLedPreview();
}

static void _signalizeInvalidConfig() {
    // Zablikame displejom pre signalizaciu neplatnych nastaveni.
    Display::setBrightnessRampDuration(300);
    Display::setBrightness(Display::MIN_BRIGHTNESS);
    Utils::waitUntil([]{ return !Display::isBrightnessTransitioning(); });
    Display::setBrightness(Display::MAX_BRIGHTNESS);
    Utils::waitUntil([]{ return !Display::isBrightnessTransitioning(); });
    Display::setBrightness(Display::getConfigBrightness());
    Utils::waitUntil([]{ return !Display::isBrightnessTransitioning(); });
    Display::setBrightnessRampDuration(BRIGHTNESS_MAX_RAMP_DUR);
}

static void _onLedBrightnessSet(uint8_t /*page_index*/, uint8_t /*conf_index*/) {
    // const uint8_t val = MAP_CLAMPED(
    //     Config::get(Config::LED_BRIGHTNESS_LEVEL),
    //     (uint8_t)0, (uint8_t)8,
    //     (uint8_t)0, (uint8_t)MAX_LED_BRIGHTNESS
    // );
    const uint8_t val = Led::getBrightnessForLevel(Config::get(Config::LED_BRIGHTNESS_LEVEL));
    // setBrightness obchadza zamok, takze sa prejavi aj pocas LED-brightness preview.
    Led::setBrightness(val);
}

static void _markTimeDirty(uint8_t, uint8_t) { _time_page_dirty = true; }
static void _markDateDirty(uint8_t, uint8_t) { _date_page_dirty = true; }
static void _markYearDirty(uint8_t, uint8_t) { _year_page_dirty = true; }

#if DCF77_ENABLED
static void _onDcf77SyncEnabledSet(uint8_t /*page*/, uint8_t /*conf_index*/) {
    if (!Config::get(Config::DCF77_SYNC_ENABLED)) {
        DCF77Sync::stopSynchronization();
    }
}
#endif

//////////////////////////////
/// Sprava konfiguracii
//////////////////////////////

static void loadTimePage(uint8_t page_index) {
    // Uistime sa, ze pocidla hodin a minut su aktualne.
    Clock::updateTimeCountersFromTimeSources();

    sprintln("Nastavujem cas...");
    for (uint8_t digit_index = 0; digit_index < DIGIT_COUNT; digit_index++) {
        Config::set(
            Config::toID(page_index, digit_index),
            Display::getTimeDigitWithIndex(
                digit_index, Clock::t_counter_minutes, Clock::t_counter_hours
            )
        );
    }
    _time_page_dirty = false;
}

static bool saveTimePage(uint8_t) {
    if (!_time_page_dirty) return true;
    // Je pocet hodin v nastavenom case platny? Minuty su platne vzdy (od 00-59).
    const uint8_t hours = Config::get(Config::TIME_H1) + Config::get(Config::TIME_H10) * 10u;
    if (hours >= MAX_HOURS_COUNT) {
        // Cas je neplatny,
        return false;
    }

    const uint8_t minutes = Config::get(Config::TIME_M1) + Config::get(Config::TIME_M10) * 10u;
    Clock::setCurrentTime(hours, minutes, 0); // V momente ulozenia zaciname pocitat od 0 sekund.

    Clock::updateTimeSourceFromTimeCounters(); // TODO: Hodne pochybna ficurka.
    return true;
}

static void loadDatePage(uint8_t page_index) {
    uint8_t month = 1, day = 1;
    Modules::DS3231::DateTime now{};
    if (Modules::DS3231::now(now)) {
        month = now.month;
        day   = now.day;
    }

    Config::set(Config::toID(page_index, 0), day / 10);
    Config::set(Config::toID(page_index, 1), day % 10);
    Config::set(Config::toID(page_index, 2), month / 10);
    Config::set(Config::toID(page_index, 3), month % 10);
    _date_page_dirty = false;
}

static bool saveDatePage(uint8_t) {
    if (!_date_page_dirty) return true;
    if (!Modules::isConnected(Modules::MODULE_DS3231)) {
        return true;
    }




    Modules::DS3231::DateTime now {};
    if (!Modules::DS3231::now(now)) {
        return false; // Neplatny datum.
    }

    Modules::DS3231::DateTime updated{
        /*second=*/now.second,
        /*minute=*/now.minute,
        /*hour=*/now.hour,
        /*day=*/(uint8_t)(Config::get(Config::DATE_DAY_D10) * 10 + Config::get(Config::DATE_DAY_D1)),
        /*month=*/(uint8_t)(Config::get(Config::DATE_MONTH_D10) * 10 + Config::get(Config::DATE_MONTH_D1)),
        /*year=*/now.year,
    };

    if (!Modules::DS3231::isDateTimeValid(updated)) {
        return false; // Neplatny datum.
    }

    Modules::DS3231::adjust(updated);
    return true;
}

static void loadYearPage(uint8_t page_index) {
    Modules::DS3231::DateTime now{};
    if (!Modules::DS3231::now(now)) {
        return;
    }

    const uint16_t year = now.year;

    Config::set(Config::toID(page_index, 0), (year / 1000) % 10);
    Config::set(Config::toID(page_index, 1), (year / 100) % 10);
    Config::set(Config::toID(page_index, 2), (year / 10) % 10);
    Config::set(Config::toID(page_index, 3), year % 10);
    _year_page_dirty = false;
}

static bool saveYearPage(uint8_t) {
    if (!_year_page_dirty) return true;
    const uint16_t year = Config::get(Config::YEAR_D1000) * 1000
                        + Config::get(Config::YEAR_D100) * 100
                        + Config::get(Config::YEAR_D10) * 10
                        + Config::get(Config::YEAR_D1);

    if (!Modules::isConnected(Modules::MODULE_DS3231)) {
        return true; // Nemame co riesit, modul nie je dostupny.
    }

    Modules::DS3231::DateTime now{};
    if (!Modules::DS3231::now(now)) {
        return true; // Nepodarilo sa nam ziskat referency cas, pustime uzivatela dalej.
    }

    Modules::DS3231::DateTime updated{
        /*second=*/now.second,
        /*minute=*/now.minute,
        /*hour=*/now.hour,
        /*day=*/now.day,
        /*month=*/now.month,
        /*year=*/year,
    };

    if (!Modules::DS3231::isDateTimeValid(updated)) {
        return false; // Neplatny datum.
    }

    Modules::DS3231::adjust(updated);
    return true;
}

//////////////////////////////
/// Verejne funkcie
//////////////////////////////

void enter() {
    sprintln(F("enterEditMode"));
    // Vybrany numitron sa uklada napriec nastavovacimi relaciami.
    _setSelectedDigit(_selected_digit);

    _idle_seconds   = 0;
    _cur_page_index = 0; // Zaciname vzdy od prvej stranky - nastavovanie casu.

    // Pocas editacneho rezimu svieti displej minimalne na DEFAULT_BRIGHTNESS
    // (napr. po prechode z nocneho rezimu kde je _target_brightness == 0).
    Display::setBrightness(
        Display::getConfigBrightness() < Display::DEFAULT_BRIGHTNESS
            ? Display::DEFAULT_BRIGHTNESS
            : Display::getConfigBrightness()
    );

    Config::loadForPage(_cur_page_index);
}

void exit() {
    sprintln(F("exitEditMode"));
    _cur_page_index = 0;
}

void setupAllConfigurations() {
    // Registrujeme vlastne save/load funkcie pre stranku casu,
    // ktore synchronizuju hodnoty s RTC / countrami namiesto priameho zapisu do EEPROM.
    Config::setSaveCallbackForPage(Config::page(Config::TIME_H10), saveTimePage);
    Config::setLoadCallbackForPage(Config::page(Config::TIME_H10), loadTimePage);

    Config::setSaveCallbackForPage(Config::page(Config::DATE_DAY_D10),     saveDatePage);
    Config::setLoadCallbackForPage(Config::page(Config::DATE_DAY_D10),     loadDatePage);

    Config::setLoadCallbackForPage(Config::page(Config::YEAR_D1000),         loadYearPage);
    Config::setSaveCallbackForPage(Config::page(Config::YEAR_D1000),         saveYearPage);

    Config::setCallback(Config::LED_BRIGHTNESS_LEVEL, _onLedBrightnessSet);
#if DCF77_ENABLED
    Config::setCallback(Config::DCF77_SYNC_ENABLED, _onDcf77SyncEnabledSet);
#endif
    Config::setCallbackForPage(Config::page(Config::TIME_H10),     _markTimeDirty);
    Config::setCallbackForPage(Config::page(Config::DATE_DAY_D10), _markDateDirty);
    Config::setCallbackForPage(Config::page(Config::YEAR_D1000),   _markYearDirty);

    Timers::setup();

    Config::loadAll(); // Nacitajme konfiguracie z EEPROM pri startupe.
    _onLedBrightnessSet(0, 0); // Aplikuj ulozenu hodnotu jasu LED.
}

//////////////////////////////
/// Sekundovy handler
//////////////////////////////

void onSecondTick() {
    if (Clock::State::inEditMode() && ++_idle_seconds >= _EDIT_MODE_TIMEOUT_S) {
        sprintln(F("Ukoncovanie edit rezimu kvoli casovemu limitu..."));
        Config::loadForPage(_cur_page_index);
        Clock::State::dispatch(Clock::State::EVT_EDIT_TIMEOUT);
        return;
    }

    if (Clock::updateTimeCountersFromTimeSources()) {
        if (Clock::State::inNormalMode()) {
            Display::displayTimeFromCounters(Clock::t_counter_minutes, Clock::t_counter_hours);
        }
    }
}

} // namespace Edit

//////////////////////////////
/// Handlery tlacidiel
//////////////////////////////
// Su mimo namespace pretoze ich deklaracie su v buttons.

using namespace Edit;

void onAnyButtonPressed() {
    sprintln(F("ANY BUTTON PRESSED"));

    if (Clock::State::inEditMode()) {
        _idle_seconds = 0;
    } else if (Clock::State::inNightMode()) {
        // V nocnom rezime kazde stlacenie zobrazi cas a obnovi odpocet preview.
        NightMode::startPreview();
    }
}

void onLeftButtonReleased() {
    sprintln(F("LEFT BUTTON RELEASED"));
    if (Clock::State::inEditMode()) {
        _setSelectedDigit((_selected_digit + 1) % DIGIT_COUNT);
        sprint(F("VYBRATY NUMITRON CISLO: "));
        sprintln(_selected_digit);
    } else if (!Clock::State::inNightMode()) {
        // Tlacidla upravuju jasovy strop v oboch rezimoch:
        // - MANUAL: strop = aktualny jas (setConfigBrightness ho aplikuje hned).
        // - AUTO:   strop = horna hranica pre LDR slucku (uplatni sa na nasl. ticku).
        const int16_t current = Display::getConfigBrightness();
        const int16_t next = CONSTRAIN(current + Display::BRIGHTNESS_STEP, 0, 255);
        Display::setConfigBrightness(uint8_t(next));
    }
}

void onLeftButtonLongPressed() {
    sprintln(F("LEFT BUTTON LONG PRESSED"));
    onLeftButtonReleased();
}

void onRightButtonReleased() {
    sprintln(F("RIGHT BUTTON RELEASED"));
    if (Clock::State::inEditMode()) {
        Config::increment(Config::toID(_cur_page_index, _selected_digit));
        _displayConfigPage(_cur_page_index);
    } else if (!Clock::State::inNightMode()) {
        // Znizenie stropu jasu (v oboch rezimoch).
        _night_hold_cnt = 0;
        const int16_t current = Display::getConfigBrightness();
        const int16_t next = CONSTRAIN(current - Display::BRIGHTNESS_STEP, 0, 255);
        Display::setConfigBrightness(uint8_t(next));
    }
}

void onRightButtonLongPressed() {
    sprintln(F("RIGHT BUTTON LONG PRESSED"));
    // Pri minimalnom strope dlhe drzanie vstupuje do nocneho rezimu (s oneskorenim).
    // Strop, nie target, aby v AUTO rezime tmavej miestnosti nehrozilo nahodne
    // prepnutie do noci ked LDR znizi jas k MIN_BRIGHTNESS.
    if (!Clock::State::inEditMode() &&
        !Clock::State::inNightMode() &&
        Display::getConfigBrightness() <= Display::MIN_BRIGHTNESS
    ) {
        if (++_night_hold_cnt >= _NIGHT_MODE_HOLD_TICKS) {
            _night_hold_cnt = 0;
            Clock::State::dispatch(Clock::State::EVT_ENTER_NIGHT);
        }
        return;
    }
    onRightButtonReleased();
}

// Kratke stlacenie oboch tlacidiel naraz, zobraz dalsi view
void onBothButtonsReleased() {
    sprintln(F("BOTH BUTTONS RELEASED"));

    if (!Clock::State::inEditMode()) {
        if (Clock::State::inViewMode()) {
            Views::showNextView();
        } else {
            Clock::State::dispatch(Clock::State::EVT_ENTER_VIEW);
        }
    }

    // V editacnom rezime kratkym stlacenim oboch tlacidiel prepiname medzi strankami nastaveni.
    if (Clock::State::inEditMode()) {
        if (!Config::saveForPage(_cur_page_index)) {
            _signalizeInvalidConfig();
            return; // Nepodarilo sa ulozit nastavenia pre danu stranku (su neplatne).
        }
        _cur_page_index = (_cur_page_index + 1u) % _USER_PAGE_COUNT;
        Config::loadForPage(_cur_page_index);
        _displayConfigPage(_cur_page_index);
    }
}

// Vykonavame bez opakovani
void onBothButtonsLongPressed() {
    sprintln(F("BOTH BUTTONS LONG PRESSED"));
    if (Clock::State::inEditMode()) {
        if (!Config::saveForPage(_cur_page_index)) {
            _signalizeInvalidConfig();
            return; // Nepodarilo sa ulozit nastavenia pre danu stranku (su neplatne).
        }

        Clock::State::dispatch(Clock::State::EVT_EXIT_EDIT);
    } else if (Clock::State::dispatch(Clock::State::EVT_ENTER_EDIT)) {
        _displayConfigPage(_cur_page_index);
    }
}
