Servacek/numeri/firmver/firmware.asm

.pio/build/uno_usbasp_dev/firmware.elf:     file format elf32-avr


Disassembly of section .text:

00000000 <__vectors>:
       0:	7d c0       	rjmp	.+250    	; 0xfc <__ctors_end>
       2:	00 00       	nop
       4:	0c 94 f8 13 	jmp	0x27f0	; 0x27f0 <__vector_1>
       8:	0c 94 02 14 	jmp	0x2804	; 0x2804 <__vector_2>
       c:	9f c0       	rjmp	.+318    	; 0x14c <__bad_interrupt>
       e:	00 00       	nop
      10:	9d c0       	rjmp	.+314    	; 0x14c <__bad_interrupt>
      12:	00 00       	nop
      14:	9b c0       	rjmp	.+310    	; 0x14c <__bad_interrupt>
      16:	00 00       	nop
      18:	99 c0       	rjmp	.+306    	; 0x14c <__bad_interrupt>
      1a:	00 00       	nop
      1c:	0c 94 0c 14 	jmp	0x2818	; 0x2818 <__vector_7>
      20:	95 c0       	rjmp	.+298    	; 0x14c <__bad_interrupt>
      22:	00 00       	nop
      24:	93 c0       	rjmp	.+294    	; 0x14c <__bad_interrupt>
      26:	00 00       	nop
      28:	91 c0       	rjmp	.+290    	; 0x14c <__bad_interrupt>
      2a:	00 00       	nop
      2c:	8f c0       	rjmp	.+286    	; 0x14c <__bad_interrupt>
      2e:	00 00       	nop
      30:	8d c0       	rjmp	.+282    	; 0x14c <__bad_interrupt>
      32:	00 00       	nop
      34:	8b c0       	rjmp	.+278    	; 0x14c <__bad_interrupt>
      36:	00 00       	nop
      38:	89 c0       	rjmp	.+274    	; 0x14c <__bad_interrupt>
      3a:	00 00       	nop
      3c:	87 c0       	rjmp	.+270    	; 0x14c <__bad_interrupt>
      3e:	00 00       	nop
      40:	85 c0       	rjmp	.+266    	; 0x14c <__bad_interrupt>
      42:	00 00       	nop
      44:	83 c0       	rjmp	.+262    	; 0x14c <__bad_interrupt>
      46:	00 00       	nop
      48:	81 c0       	rjmp	.+258    	; 0x14c <__bad_interrupt>
      4a:	00 00       	nop
      4c:	7f c0       	rjmp	.+254    	; 0x14c <__bad_interrupt>
      4e:	00 00       	nop
      50:	7d c0       	rjmp	.+250    	; 0x14c <__bad_interrupt>
      52:	00 00       	nop
      54:	7b c0       	rjmp	.+246    	; 0x14c <__bad_interrupt>
      56:	00 00       	nop
      58:	79 c0       	rjmp	.+242    	; 0x14c <__bad_interrupt>
      5a:	00 00       	nop
      5c:	77 c0       	rjmp	.+238    	; 0x14c <__bad_interrupt>
      5e:	00 00       	nop
      60:	0c 94 64 13 	jmp	0x26c8	; 0x26c8 <__vector_24>
      64:	73 c0       	rjmp	.+230    	; 0x14c <__bad_interrupt>
	...

00000068 <__trampolines_end>:
      68:	00 01       	movw	r0, r0
      6a:	02 03       	mulsu	r16, r18

0000006c <_ZN6ConfigL24TIME_HOUR_FORMAT_OPTIONSE>:
      6c:	02 04                                               ..

0000006e <_ZN5ViewsL5VIEWSE>:
      6e:	1e 11 a8 10                                         ....

00000072 <_ZL14SEGMENT_SYMBOL>:
      72:	7b 60 57 76 6c 3e 3f 70 7f 7e 5c 04 1b ff           {`Wvl>?p.~\...

00000080 <_ZZN7Modules17initializeModulesEvE3__c_0>:
      80:	52 54 43 20 6d 6f 64 75 6c 20 69 6e 69 63 69 61     RTC modul inicia
      90:	6c 69 7a 6f 76 61 6e c3 bd 2e 00                    lizovan....

0000009b <_ZZN7Modules17initializeModulesEvE3__c_1>:
      9b:	5b 56 61 72 6f 76 61 6e 69 65 5d 20 52 54 43 20     [Varovanie] RTC 
      ab:	6d 6f 64 75 6c 20 6e 65 62 6f 6c 20 6e c3 a1 6a     modul nebol n..j
      bb:	64 65 6e c3 bd 21 00                                den..!.

000000c2 <_ZZN7Modules17initializeModulesEvE3__c>:
      c2:	49 6e 69 63 69 61 6c 69 7a c3 a1 63 69 61 20 49     Inicializ..cia I
      d2:	32 43 20 7a 62 65 72 6e 69 63 65 2e 2e 2e 00        2C zbernice....

000000e1 <_ZZN7ModulesL21_onModuleStateChangedEhbE3__c_1>:
      e1:	6f 64 70 6f 6a 65 6e c3 bd 2e 00                    odpojen....

000000ec <_ZZN7ModulesL21_onModuleStateChangedEhbE3__c_0>:
      ec:	70 72 69 70 6f 6a 65 6e c3 bd 2e 00                 pripojen....

000000f8 <_ZZN7ModulesL21_onModuleStateChangedEhbE3__c>:
      f8:	20 00                                                .

000000fa <__ctors_start>:
      fa:	d5 1f       	adc	r29, r21

000000fc <__ctors_end>:
      fc:	11 24       	eor	r1, r1
      fe:	1f be       	out	0x3f, r1	; 63
     100:	cf ef       	ldi	r28, 0xFF	; 255
     102:	d8 e0       	ldi	r29, 0x08	; 8
     104:	de bf       	out	0x3e, r29	; 62
     106:	cd bf       	out	0x3d, r28	; 61

00000108 <__do_copy_data>:
     108:	13 e0       	ldi	r17, 0x03	; 3
     10a:	a0 e0       	ldi	r26, 0x00	; 0
     10c:	b1 e0       	ldi	r27, 0x01	; 1
     10e:	e8 e2       	ldi	r30, 0x28	; 40
     110:	ff e4       	ldi	r31, 0x4F	; 79
     112:	02 c0       	rjmp	.+4      	; 0x118 <__do_copy_data+0x10>
     114:	05 90       	lpm	r0, Z+
     116:	0d 92       	st	X+, r0
     118:	ae 30       	cpi	r26, 0x0E	; 14
     11a:	b1 07       	cpc	r27, r17
     11c:	d9 f7       	brne	.-10     	; 0x114 <__do_copy_data+0xc>

0000011e <__do_clear_bss>:
     11e:	26 e0       	ldi	r18, 0x06	; 6
     120:	ae e0       	ldi	r26, 0x0E	; 14
     122:	b3 e0       	ldi	r27, 0x03	; 3
     124:	01 c0       	rjmp	.+2      	; 0x128 <.do_clear_bss_start>

00000126 <.do_clear_bss_loop>:
     126:	1d 92       	st	X+, r1

00000128 <.do_clear_bss_start>:
     128:	a2 30       	cpi	r26, 0x02	; 2
     12a:	b2 07       	cpc	r27, r18
     12c:	e1 f7       	brne	.-8      	; 0x126 <.do_clear_bss_loop>

0000012e <__do_global_ctors>:
     12e:	10 e0       	ldi	r17, 0x00	; 0
     130:	ce e7       	ldi	r28, 0x7E	; 126
     132:	d0 e0       	ldi	r29, 0x00	; 0
     134:	04 c0       	rjmp	.+8      	; 0x13e <__do_global_ctors+0x10>
     136:	21 97       	sbiw	r28, 0x01	; 1
     138:	fe 01       	movw	r30, r28
     13a:	0e 94 2d 27 	call	0x4e5a	; 0x4e5a <__tablejump2__>
     13e:	cd 37       	cpi	r28, 0x7D	; 125
     140:	d1 07       	cpc	r29, r17
     142:	c9 f7       	brne	.-14     	; 0x136 <__do_global_ctors+0x8>
     144:	0e 94 2e 20 	call	0x405c	; 0x405c <main>
     148:	0c 94 92 27 	jmp	0x4f24	; 0x4f24 <_exit>

0000014c <__bad_interrupt>:
     14c:	59 cf       	rjmp	.-334    	; 0x0 <__vectors>

0000014e <_Z20putDigitsToInputRegsPKhh.constprop.78>:
     14e:	5f 98       	cbi	0x0b, 7	; 11
     150:	28 98       	cbi	0x05, 0	; 5
     152:	fc 01       	movw	r30, r24
     154:	94 e0       	ldi	r25, 0x04	; 4
     156:	50 e0       	ldi	r21, 0x00	; 0
     158:	40 e0       	ldi	r20, 0x00	; 0
     15a:	20 81       	ld	r18, Z
     15c:	30 e0       	ldi	r19, 0x00	; 0
     15e:	04 2e       	mov	r0, r20
     160:	02 c0       	rjmp	.+4      	; 0x166 <_Z20putDigitsToInputRegsPKhh.constprop.78+0x18>
     162:	35 95       	asr	r19
     164:	27 95       	ror	r18
     166:	0a 94       	dec	r0
     168:	e2 f7       	brpl	.-8      	; 0x162 <_Z20putDigitsToInputRegsPKhh.constprop.78+0x14>
     16a:	20 ff       	sbrs	r18, 0
     16c:	0d c0       	rjmp	.+26     	; 0x188 <_Z20putDigitsToInputRegsPKhh.constprop.78+0x3a>
     16e:	2c 9a       	sbi	0x05, 4	; 5
     170:	28 9a       	sbi	0x05, 0	; 5
     172:	28 98       	cbi	0x05, 0	; 5
     174:	4f 5f       	subi	r20, 0xFF	; 255
     176:	5f 4f       	sbci	r21, 0xFF	; 255
     178:	48 30       	cpi	r20, 0x08	; 8
     17a:	51 05       	cpc	r21, r1
     17c:	71 f7       	brne	.-36     	; 0x15a <_Z20putDigitsToInputRegsPKhh.constprop.78+0xc>
     17e:	91 50       	subi	r25, 0x01	; 1
     180:	31 96       	adiw	r30, 0x01	; 1
     182:	91 11       	cpse	r25, r1
     184:	e8 cf       	rjmp	.-48     	; 0x156 <_Z20putDigitsToInputRegsPKhh.constprop.78+0x8>
     186:	08 95       	ret
     188:	2c 98       	cbi	0x05, 4	; 5
     18a:	f2 cf       	rjmp	.-28     	; 0x170 <_Z20putDigitsToInputRegsPKhh.constprop.78+0x22>

0000018c <_ZN8Internal18DCF77_Year_Decoder5setupEv.constprop.68>:
     18c:	ea e5       	ldi	r30, 0x5A	; 90
     18e:	f4 e0       	ldi	r31, 0x04	; 4
     190:	11 92       	st	Z+, r1
     192:	84 e0       	ldi	r24, 0x04	; 4
     194:	e4 36       	cpi	r30, 0x64	; 100
     196:	f8 07       	cpc	r31, r24
     198:	d9 f7       	brne	.-10     	; 0x190 <_ZN8Internal18DCF77_Year_Decoder5setupEv.constprop.68+0x4>
     19a:	10 92 64 04 	sts	0x0464, r1	; 0x800464 <_ZN8Internal22DCF77_Clock_ControllerI13ConfigurationNS_23DCF77_Frequency_ControlEE12Year_DecoderE+0xa>
     19e:	10 92 66 04 	sts	0x0466, r1	; 0x800466 <_ZN8Internal22DCF77_Clock_ControllerI13ConfigurationNS_23DCF77_Frequency_ControlEE12Year_DecoderE+0xc>
     1a2:	8b e0       	ldi	r24, 0x0B	; 11
     1a4:	80 93 67 04 	sts	0x0467, r24	; 0x800467 <_ZN8Internal22DCF77_Clock_ControllerI13ConfigurationNS_23DCF77_Frequency_ControlEE12Year_DecoderE+0xd>
     1a8:	10 92 65 04 	sts	0x0465, r1	; 0x800465 <_ZN8Internal22DCF77_Clock_ControllerI13ConfigurationNS_23DCF77_Frequency_ControlEE12Year_DecoderE+0xb>
     1ac:	e8 e6       	ldi	r30, 0x68	; 104
     1ae:	f4 e0       	ldi	r31, 0x04	; 4
     1b0:	11 92       	st	Z+, r1
     1b2:	84 e0       	ldi	r24, 0x04	; 4
     1b4:	e2 37       	cpi	r30, 0x72	; 114
     1b6:	f8 07       	cpc	r31, r24
     1b8:	d9 f7       	brne	.-10     	; 0x1b0 <_ZN8Internal18DCF77_Year_Decoder5setupEv.constprop.68+0x24>
     1ba:	10 92 72 04 	sts	0x0472, r1	; 0x800472 <_ZN8Internal22DCF77_Clock_ControllerI13ConfigurationNS_23DCF77_Frequency_ControlEE12Year_DecoderE+0x18>
     1be:	10 92 74 04 	sts	0x0474, r1	; 0x800474 <_ZN8Internal22DCF77_Clock_ControllerI13ConfigurationNS_23DCF77_Frequency_ControlEE12Year_DecoderE+0x1a>
     1c2:	8b e0       	ldi	r24, 0x0B	; 11
     1c4:	80 93 75 04 	sts	0x0475, r24	; 0x800475 <_ZN8Internal22DCF77_Clock_ControllerI13ConfigurationNS_23DCF77_Frequency_ControlEE12Year_DecoderE+0x1b>
     1c8:	10 92 73 04 	sts	0x0473, r1	; 0x800473 <_ZN8Internal22DCF77_Clock_ControllerI13ConfigurationNS_23DCF77_Frequency_ControlEE12Year_DecoderE+0x19>
     1cc:	08 95       	ret

000001ce <_ZN8Internal20DCF77_Second_Decoder14get_time_valueEv.constprop.33>:
     1ce:	80 91 f6 03 	lds	r24, 0x03F6	; 0x8003f6 <_ZN8Internal22DCF77_Clock_ControllerI13ConfigurationNS_23DCF77_Frequency_ControlEE14Second_DecoderE+0x3e>
     1d2:	90 91 f5 03 	lds	r25, 0x03F5	; 0x8003f5 <_ZN8Internal22DCF77_Clock_ControllerI13ConfigurationNS_23DCF77_Frequency_ControlEE14Second_DecoderE+0x3d>
     1d6:	89 1b       	sub	r24, r25
     1d8:	99 0b       	sbc	r25, r25
     1da:	0c 97       	sbiw	r24, 0x0c	; 12
     1dc:	54 f0       	brlt	.+20     	; 0x1f2 <_ZN8Internal20DCF77_Second_Decoder14get_time_valueEv.constprop.33+0x24>
     1de:	80 91 f4 03 	lds	r24, 0x03F4	; 0x8003f4 <_ZN8Internal22DCF77_Clock_ControllerI13ConfigurationNS_23DCF77_Frequency_ControlEE14Second_DecoderE+0x3c>
     1e2:	8a 58       	subi	r24, 0x8A	; 138
     1e4:	90 91 f7 03 	lds	r25, 0x03F7	; 0x8003f7 <_ZN8Internal22DCF77_Clock_ControllerI13ConfigurationNS_23DCF77_Frequency_ControlEE14Second_DecoderE+0x3f>
     1e8:	89 1b       	sub	r24, r25
     1ea:	8c 33       	cpi	r24, 0x3C	; 60
     1ec:	18 f0       	brcs	.+6      	; 0x1f4 <_ZN8Internal20DCF77_Second_Decoder14get_time_valueEv.constprop.33+0x26>
     1ee:	8c 53       	subi	r24, 0x3C	; 60
     1f0:	fc cf       	rjmp	.-8      	; 0x1ea <_ZN8Internal20DCF77_Second_Decoder14get_time_valueEv.constprop.33+0x1c>
     1f2:	8f ef       	ldi	r24, 0xFF	; 255
     1f4:	08 95       	ret

000001f6 <_ZN8Internal7Binning6bins_tIjmLj100EE18get_quality_factorEv.constprop.24>:
     1f6:	ef 92       	push	r14
     1f8:	ff 92       	push	r15
     1fa:	0f 93       	push	r16
     1fc:	1f 93       	push	r17
     1fe:	2f b7       	in	r18, 0x3f	; 63
     200:	f8 94       	cli
     202:	40 91 d7 05 	lds	r20, 0x05D7	; 0x8005d7 <_ZN8Internal22DCF77_Clock_ControllerI13ConfigurationNS_23DCF77_Frequency_ControlEE11DemodulatorE+0xcd>
     206:	50 91 d8 05 	lds	r21, 0x05D8	; 0x8005d8 <_ZN8Internal22DCF77_Clock_ControllerI13ConfigurationNS_23DCF77_Frequency_ControlEE11DemodulatorE+0xce>
     20a:	60 91 d9 05 	lds	r22, 0x05D9	; 0x8005d9 <_ZN8Internal22DCF77_Clock_ControllerI13ConfigurationNS_23DCF77_Frequency_ControlEE11DemodulatorE+0xcf>
     20e:	70 91 da 05 	lds	r23, 0x05DA	; 0x8005da <_ZN8Internal22DCF77_Clock_ControllerI13ConfigurationNS_23DCF77_Frequency_ControlEE11DemodulatorE+0xd0>
     212:	80 91 d3 05 	lds	r24, 0x05D3	; 0x8005d3 <_ZN8Internal22DCF77_Clock_ControllerI13ConfigurationNS_23DCF77_Frequency_ControlEE11DemodulatorE+0xc9>
     216:	90 91 d4 05 	lds	r25, 0x05D4	; 0x8005d4 <_ZN8Internal22DCF77_Clock_ControllerI13ConfigurationNS_23DCF77_Frequency_ControlEE11DemodulatorE+0xca>
     21a:	a0 91 d5 05 	lds	r26, 0x05D5	; 0x8005d5 <_ZN8Internal22DCF77_Clock_ControllerI13ConfigurationNS_23DCF77_Frequency_ControlEE11DemodulatorE+0xcb>
     21e:	b0 91 d6 05 	lds	r27, 0x05D6	; 0x8005d6 <_ZN8Internal22DCF77_Clock_ControllerI13ConfigurationNS_23DCF77_Frequency_ControlEE11DemodulatorE+0xcc>
     222:	84 17       	cp	r24, r20
     224:	95 07       	cpc	r25, r21
     226:	a6 07       	cpc	r26, r22
     228:	b7 07       	cpc	r27, r23
     22a:	38 f0       	brcs	.+14     	; 0x23a <_ZN8Internal7Binning6bins_tIjmLj100EE18get_quality_factorEv.constprop.24+0x44>
     22c:	2f bf       	out	0x3f, r18	; 63
     22e:	80 e0       	ldi	r24, 0x00	; 0
     230:	1f 91       	pop	r17
     232:	0f 91       	pop	r16
     234:	ff 90       	pop	r15
     236:	ef 90       	pop	r14
     238:	08 95       	ret
     23a:	7a 01       	movw	r14, r20
     23c:	8b 01       	movw	r16, r22
     23e:	e8 1a       	sub	r14, r24
     240:	f9 0a       	sbc	r15, r25
     242:	0a 0b       	sbc	r16, r26
     244:	1b 0b       	sbc	r17, r27
     246:	d8 01       	movw	r26, r16
     248:	c7 01       	movw	r24, r14
     24a:	2f bf       	out	0x3f, r18	; 63
     24c:	20 e0       	ldi	r18, 0x00	; 0
     24e:	41 15       	cp	r20, r1
     250:	51 05       	cpc	r21, r1
     252:	61 05       	cpc	r22, r1
     254:	71 05       	cpc	r23, r1
     256:	31 f0       	breq	.+12     	; 0x264 <_ZN8Internal7Binning6bins_tIjmLj100EE18get_quality_factorEv.constprop.24+0x6e>
     258:	76 95       	lsr	r23
     25a:	67 95       	ror	r22
     25c:	57 95       	ror	r21
     25e:	47 95       	ror	r20
     260:	2f 5f       	subi	r18, 0xFF	; 255
     262:	f5 cf       	rjmp	.-22     	; 0x24e <_ZN8Internal7Binning6bins_tIjmLj100EE18get_quality_factorEv.constprop.24+0x58>
     264:	22 23       	and	r18, r18
     266:	31 f0       	breq	.+12     	; 0x274 <_ZN8Internal7Binning6bins_tIjmLj100EE18get_quality_factorEv.constprop.24+0x7e>
     268:	26 95       	lsr	r18
     26a:	b6 95       	lsr	r27
     26c:	a7 95       	ror	r26
     26e:	97 95       	ror	r25
     270:	87 95       	ror	r24
     272:	f8 cf       	rjmp	.-16     	; 0x264 <_ZN8Internal7Binning6bins_tIjmLj100EE18get_quality_factorEv.constprop.24+0x6e>
     274:	8f 3f       	cpi	r24, 0xFF	; 255
     276:	91 05       	cpc	r25, r1
     278:	a1 05       	cpc	r26, r1
     27a:	b1 05       	cpc	r27, r1
     27c:	c9 f2       	breq	.-78     	; 0x230 <_ZN8Internal7Binning6bins_tIjmLj100EE18get_quality_factorEv.constprop.24+0x3a>
     27e:	c0 f2       	brcs	.-80     	; 0x230 <_ZN8Internal7Binning6bins_tIjmLj100EE18get_quality_factorEv.constprop.24+0x3a>
     280:	8f ef       	ldi	r24, 0xFF	; 255
     282:	90 e0       	ldi	r25, 0x00	; 0
     284:	a0 e0       	ldi	r26, 0x00	; 0
     286:	b0 e0       	ldi	r27, 0x00	; 0
     288:	d3 cf       	rjmp	.-90     	; 0x230 <_ZN8Internal7Binning6bins_tIjmLj100EE18get_quality_factorEv.constprop.24+0x3a>

0000028a <_ZN8Internal7Binning6bins_tIhhLj12EE18get_quality_factorEv.constprop.21>:
     28a:	8f b7       	in	r24, 0x3f	; 63
     28c:	f8 94       	cli
     28e:	90 91 58 04 	lds	r25, 0x0458	; 0x800458 <_ZN8Internal22DCF77_Clock_ControllerI13ConfigurationNS_23DCF77_Frequency_ControlEE13Month_DecoderE+0xe>
     292:	20 91 57 04 	lds	r18, 0x0457	; 0x800457 <_ZN8Internal22DCF77_Clock_ControllerI13ConfigurationNS_23DCF77_Frequency_ControlEE13Month_DecoderE+0xd>
     296:	29 17       	cp	r18, r25
     298:	18 f0       	brcs	.+6      	; 0x2a0 <_ZN8Internal7Binning6bins_tIhhLj12EE18get_quality_factorEv.constprop.21+0x16>
     29a:	8f bf       	out	0x3f, r24	; 63
     29c:	80 e0       	ldi	r24, 0x00	; 0
     29e:	08 95       	ret
     2a0:	39 2f       	mov	r19, r25
     2a2:	32 1b       	sub	r19, r18
     2a4:	23 2f       	mov	r18, r19
     2a6:	8f bf       	out	0x3f, r24	; 63
     2a8:	80 e0       	ldi	r24, 0x00	; 0
     2aa:	9d 31       	cpi	r25, 0x1D	; 29
     2ac:	40 f4       	brcc	.+16     	; 0x2be <_ZN8Internal7Binning6bins_tIhhLj12EE18get_quality_factorEv.constprop.21+0x34>
     2ae:	9d 30       	cpi	r25, 0x0D	; 13
     2b0:	08 f4       	brcc	.+2      	; 0x2b4 <_ZN8Internal7Binning6bins_tIhhLj12EE18get_quality_factorEv.constprop.21+0x2a>
     2b2:	45 c0       	rjmp	.+138    	; 0x33e <_ZN8Internal7Binning6bins_tIhhLj12EE18get_quality_factorEv.constprop.21+0xb4>
     2b4:	83 2f       	mov	r24, r19
     2b6:	86 95       	lsr	r24
     2b8:	86 95       	lsr	r24
     2ba:	08 95       	ret
     2bc:	83 2f       	mov	r24, r19
     2be:	96 95       	lsr	r25
     2c0:	31 e0       	ldi	r19, 0x01	; 1
     2c2:	38 0f       	add	r19, r24
     2c4:	91 11       	cpse	r25, r1
     2c6:	fa cf       	rjmp	.-12     	; 0x2bc <_ZN8Internal7Binning6bins_tIhhLj12EE18get_quality_factorEv.constprop.21+0x32>
     2c8:	8d 30       	cpi	r24, 0x0D	; 13
     2ca:	68 f0       	brcs	.+26     	; 0x2e6 <_ZN8Internal7Binning6bins_tIhhLj12EE18get_quality_factorEv.constprop.21+0x5c>
     2cc:	8d 30       	cpi	r24, 0x0D	; 13
     2ce:	29 f1       	breq	.+74     	; 0x31a <_ZN8Internal7Binning6bins_tIhhLj12EE18get_quality_factorEv.constprop.21+0x90>
     2d0:	8e 30       	cpi	r24, 0x0E	; 14
     2d2:	31 f1       	breq	.+76     	; 0x320 <_ZN8Internal7Binning6bins_tIhhLj12EE18get_quality_factorEv.constprop.21+0x96>
     2d4:	81 e1       	ldi	r24, 0x11	; 17
     2d6:	90 e0       	ldi	r25, 0x00	; 0
     2d8:	28 9f       	mul	r18, r24
     2da:	a0 01       	movw	r20, r0
     2dc:	29 9f       	mul	r18, r25
     2de:	50 0d       	add	r21, r0
     2e0:	11 24       	eor	r1, r1
     2e2:	85 2f       	mov	r24, r21
     2e4:	08 95       	ret
     2e6:	89 30       	cpi	r24, 0x09	; 9
     2e8:	60 f0       	brcs	.+24     	; 0x302 <_ZN8Internal7Binning6bins_tIhhLj12EE18get_quality_factorEv.constprop.21+0x78>
     2ea:	8b 30       	cpi	r24, 0x0B	; 11
     2ec:	28 f0       	brcs	.+10     	; 0x2f8 <_ZN8Internal7Binning6bins_tIhhLj12EE18get_quality_factorEv.constprop.21+0x6e>
     2ee:	8c 30       	cpi	r24, 0x0C	; 12
     2f0:	d1 f4       	brne	.+52     	; 0x326 <_ZN8Internal7Binning6bins_tIhhLj12EE18get_quality_factorEv.constprop.21+0x9c>
     2f2:	85 e1       	ldi	r24, 0x15	; 21
     2f4:	90 e0       	ldi	r25, 0x00	; 0
     2f6:	f0 cf       	rjmp	.-32     	; 0x2d8 <_ZN8Internal7Binning6bins_tIhhLj12EE18get_quality_factorEv.constprop.21+0x4e>
     2f8:	8a 30       	cpi	r24, 0x0A	; 10
     2fa:	c1 f4       	brne	.+48     	; 0x32c <_ZN8Internal7Binning6bins_tIhhLj12EE18get_quality_factorEv.constprop.21+0xa2>
     2fc:	89 e1       	ldi	r24, 0x19	; 25
     2fe:	90 e0       	ldi	r25, 0x00	; 0
     300:	eb cf       	rjmp	.-42     	; 0x2d8 <_ZN8Internal7Binning6bins_tIhhLj12EE18get_quality_factorEv.constprop.21+0x4e>
     302:	87 30       	cpi	r24, 0x07	; 7
     304:	28 f0       	brcs	.+10     	; 0x310 <_ZN8Internal7Binning6bins_tIhhLj12EE18get_quality_factorEv.constprop.21+0x86>
     306:	88 30       	cpi	r24, 0x08	; 8
     308:	a1 f4       	brne	.+40     	; 0x332 <_ZN8Internal7Binning6bins_tIhhLj12EE18get_quality_factorEv.constprop.21+0xa8>
     30a:	80 e2       	ldi	r24, 0x20	; 32
     30c:	90 e0       	ldi	r25, 0x00	; 0
     30e:	e4 cf       	rjmp	.-56     	; 0x2d8 <_ZN8Internal7Binning6bins_tIhhLj12EE18get_quality_factorEv.constprop.21+0x4e>
     310:	86 30       	cpi	r24, 0x06	; 6
     312:	91 f4       	brne	.+36     	; 0x338 <_ZN8Internal7Binning6bins_tIhhLj12EE18get_quality_factorEv.constprop.21+0xae>
     314:	8a e2       	ldi	r24, 0x2A	; 42
     316:	90 e0       	ldi	r25, 0x00	; 0
     318:	df cf       	rjmp	.-66     	; 0x2d8 <_ZN8Internal7Binning6bins_tIhhLj12EE18get_quality_factorEv.constprop.21+0x4e>
     31a:	83 e1       	ldi	r24, 0x13	; 19
     31c:	90 e0       	ldi	r25, 0x00	; 0
     31e:	dc cf       	rjmp	.-72     	; 0x2d8 <_ZN8Internal7Binning6bins_tIhhLj12EE18get_quality_factorEv.constprop.21+0x4e>
     320:	82 e1       	ldi	r24, 0x12	; 18
     322:	90 e0       	ldi	r25, 0x00	; 0
     324:	d9 cf       	rjmp	.-78     	; 0x2d8 <_ZN8Internal7Binning6bins_tIhhLj12EE18get_quality_factorEv.constprop.21+0x4e>
     326:	87 e1       	ldi	r24, 0x17	; 23
     328:	90 e0       	ldi	r25, 0x00	; 0
     32a:	d6 cf       	rjmp	.-84     	; 0x2d8 <_ZN8Internal7Binning6bins_tIhhLj12EE18get_quality_factorEv.constprop.21+0x4e>
     32c:	8c e1       	ldi	r24, 0x1C	; 28
     32e:	90 e0       	ldi	r25, 0x00	; 0
     330:	d3 cf       	rjmp	.-90     	; 0x2d8 <_ZN8Internal7Binning6bins_tIhhLj12EE18get_quality_factorEv.constprop.21+0x4e>
     332:	84 e2       	ldi	r24, 0x24	; 36
     334:	90 e0       	ldi	r25, 0x00	; 0
     336:	d0 cf       	rjmp	.-96     	; 0x2d8 <_ZN8Internal7Binning6bins_tIhhLj12EE18get_quality_factorEv.constprop.21+0x4e>
     338:	83 e3       	ldi	r24, 0x33	; 51
     33a:	90 e0       	ldi	r25, 0x00	; 0
     33c:	cd cf       	rjmp	.-102    	; 0x2d8 <_ZN8Internal7Binning6bins_tIhhLj12EE18get_quality_factorEv.constprop.21+0x4e>
     33e:	99 30       	cpi	r25, 0x09	; 9
     340:	48 f0       	brcs	.+18     	; 0x354 <_ZN8Internal7Binning6bins_tIhhLj12EE18get_quality_factorEv.constprop.21+0xca>
     342:	3b 30       	cpi	r19, 0x0B	; 11
     344:	a0 f4       	brcc	.+40     	; 0x36e <_ZN8Internal7Binning6bins_tIhhLj12EE18get_quality_factorEv.constprop.21+0xe4>
     346:	37 30       	cpi	r19, 0x07	; 7
     348:	a0 f4       	brcc	.+40     	; 0x372 <_ZN8Internal7Binning6bins_tIhhLj12EE18get_quality_factorEv.constprop.21+0xe8>
     34a:	81 e0       	ldi	r24, 0x01	; 1
     34c:	34 30       	cpi	r19, 0x04	; 4
     34e:	08 f4       	brcc	.+2      	; 0x352 <_ZN8Internal7Binning6bins_tIhhLj12EE18get_quality_factorEv.constprop.21+0xc8>
     350:	a5 cf       	rjmp	.-182    	; 0x29c <_ZN8Internal7Binning6bins_tIhhLj12EE18get_quality_factorEv.constprop.21+0x12>
     352:	08 95       	ret
     354:	95 30       	cpi	r25, 0x05	; 5
     356:	30 f0       	brcs	.+12     	; 0x364 <_ZN8Internal7Binning6bins_tIhhLj12EE18get_quality_factorEv.constprop.21+0xda>
     358:	36 30       	cpi	r19, 0x06	; 6
     35a:	58 f4       	brcc	.+22     	; 0x372 <_ZN8Internal7Binning6bins_tIhhLj12EE18get_quality_factorEv.constprop.21+0xe8>
     35c:	81 e0       	ldi	r24, 0x01	; 1
     35e:	23 30       	cpi	r18, 0x03	; 3
     360:	c0 f7       	brcc	.-16     	; 0x352 <_ZN8Internal7Binning6bins_tIhhLj12EE18get_quality_factorEv.constprop.21+0xc8>
     362:	9c cf       	rjmp	.-200    	; 0x29c <_ZN8Internal7Binning6bins_tIhhLj12EE18get_quality_factorEv.constprop.21+0x12>
     364:	93 30       	cpi	r25, 0x03	; 3
     366:	d0 f7       	brcc	.-12     	; 0x35c <_ZN8Internal7Binning6bins_tIhhLj12EE18get_quality_factorEv.constprop.21+0xd2>
     368:	83 2f       	mov	r24, r19
     36a:	86 95       	lsr	r24
     36c:	08 95       	ret
     36e:	83 e0       	ldi	r24, 0x03	; 3
     370:	08 95       	ret
     372:	82 e0       	ldi	r24, 0x02	; 2
     374:	ee cf       	rjmp	.-36     	; 0x352 <_ZN8Internal7Binning6bins_tIhhLj12EE18get_quality_factorEv.constprop.21+0xc8>

00000376 <_ZN8Internal7Binning6bins_tIhhLj31EE18get_quality_factorEv.constprop.20>:
     376:	8f b7       	in	r24, 0x3f	; 63
     378:	f8 94       	cli
     37a:	90 91 48 04 	lds	r25, 0x0448	; 0x800448 <_ZN8Internal22DCF77_Clock_ControllerI13ConfigurationNS_23DCF77_Frequency_ControlEE11Day_DecoderE+0x21>
     37e:	20 91 47 04 	lds	r18, 0x0447	; 0x800447 <_ZN8Internal22DCF77_Clock_ControllerI13ConfigurationNS_23DCF77_Frequency_ControlEE11Day_DecoderE+0x20>
     382:	29 17       	cp	r18, r25
     384:	18 f0       	brcs	.+6      	; 0x38c <_ZN8Internal7Binning6bins_tIhhLj31EE18get_quality_factorEv.constprop.20+0x16>
     386:	8f bf       	out	0x3f, r24	; 63
     388:	80 e0       	ldi	r24, 0x00	; 0
     38a:	08 95       	ret
     38c:	39 2f       	mov	r19, r25
     38e:	32 1b       	sub	r19, r18
     390:	23 2f       	mov	r18, r19
     392:	8f bf       	out	0x3f, r24	; 63
     394:	80 e0       	ldi	r24, 0x00	; 0
     396:	9d 31       	cpi	r25, 0x1D	; 29
     398:	40 f4       	brcc	.+16     	; 0x3aa <_ZN8Internal7Binning6bins_tIhhLj31EE18get_quality_factorEv.constprop.20+0x34>
     39a:	9d 30       	cpi	r25, 0x0D	; 13
     39c:	08 f4       	brcc	.+2      	; 0x3a0 <_ZN8Internal7Binning6bins_tIhhLj31EE18get_quality_factorEv.constprop.20+0x2a>
     39e:	45 c0       	rjmp	.+138    	; 0x42a <__LOCK_REGION_LENGTH__+0x2a>
     3a0:	83 2f       	mov	r24, r19
     3a2:	86 95       	lsr	r24
     3a4:	86 95       	lsr	r24
     3a6:	08 95       	ret
     3a8:	83 2f       	mov	r24, r19
     3aa:	96 95       	lsr	r25
     3ac:	31 e0       	ldi	r19, 0x01	; 1
     3ae:	38 0f       	add	r19, r24
     3b0:	91 11       	cpse	r25, r1
     3b2:	fa cf       	rjmp	.-12     	; 0x3a8 <_ZN8Internal7Binning6bins_tIhhLj31EE18get_quality_factorEv.constprop.20+0x32>
     3b4:	8d 30       	cpi	r24, 0x0D	; 13
     3b6:	68 f0       	brcs	.+26     	; 0x3d2 <_ZN8Internal7Binning6bins_tIhhLj31EE18get_quality_factorEv.constprop.20+0x5c>
     3b8:	8d 30       	cpi	r24, 0x0D	; 13
     3ba:	29 f1       	breq	.+74     	; 0x406 <__LOCK_REGION_LENGTH__+0x6>
     3bc:	8e 30       	cpi	r24, 0x0E	; 14
     3be:	31 f1       	breq	.+76     	; 0x40c <__LOCK_REGION_LENGTH__+0xc>
     3c0:	81 e1       	ldi	r24, 0x11	; 17
     3c2:	90 e0       	ldi	r25, 0x00	; 0
     3c4:	28 9f       	mul	r18, r24
     3c6:	a0 01       	movw	r20, r0
     3c8:	29 9f       	mul	r18, r25
     3ca:	50 0d       	add	r21, r0
     3cc:	11 24       	eor	r1, r1
     3ce:	85 2f       	mov	r24, r21
     3d0:	08 95       	ret
     3d2:	89 30       	cpi	r24, 0x09	; 9
     3d4:	60 f0       	brcs	.+24     	; 0x3ee <_ZN8Internal7Binning6bins_tIhhLj31EE18get_quality_factorEv.constprop.20+0x78>
     3d6:	8b 30       	cpi	r24, 0x0B	; 11
     3d8:	28 f0       	brcs	.+10     	; 0x3e4 <_ZN8Internal7Binning6bins_tIhhLj31EE18get_quality_factorEv.constprop.20+0x6e>
     3da:	8c 30       	cpi	r24, 0x0C	; 12
     3dc:	d1 f4       	brne	.+52     	; 0x412 <__LOCK_REGION_LENGTH__+0x12>
     3de:	85 e1       	ldi	r24, 0x15	; 21
     3e0:	90 e0       	ldi	r25, 0x00	; 0
     3e2:	f0 cf       	rjmp	.-32     	; 0x3c4 <_ZN8Internal7Binning6bins_tIhhLj31EE18get_quality_factorEv.constprop.20+0x4e>
     3e4:	8a 30       	cpi	r24, 0x0A	; 10
     3e6:	c1 f4       	brne	.+48     	; 0x418 <__LOCK_REGION_LENGTH__+0x18>
     3e8:	89 e1       	ldi	r24, 0x19	; 25
     3ea:	90 e0       	ldi	r25, 0x00	; 0
     3ec:	eb cf       	rjmp	.-42     	; 0x3c4 <_ZN8Internal7Binning6bins_tIhhLj31EE18get_quality_factorEv.constprop.20+0x4e>
     3ee:	87 30       	cpi	r24, 0x07	; 7
     3f0:	28 f0       	brcs	.+10     	; 0x3fc <_ZN8Internal7Binning6bins_tIhhLj31EE18get_quality_factorEv.constprop.20+0x86>
     3f2:	88 30       	cpi	r24, 0x08	; 8
     3f4:	a1 f4       	brne	.+40     	; 0x41e <__LOCK_REGION_LENGTH__+0x1e>
     3f6:	80 e2       	ldi	r24, 0x20	; 32
     3f8:	90 e0       	ldi	r25, 0x00	; 0
     3fa:	e4 cf       	rjmp	.-56     	; 0x3c4 <_ZN8Internal7Binning6bins_tIhhLj31EE18get_quality_factorEv.constprop.20+0x4e>
     3fc:	86 30       	cpi	r24, 0x06	; 6
     3fe:	91 f4       	brne	.+36     	; 0x424 <__LOCK_REGION_LENGTH__+0x24>
     400:	8a e2       	ldi	r24, 0x2A	; 42
     402:	90 e0       	ldi	r25, 0x00	; 0
     404:	df cf       	rjmp	.-66     	; 0x3c4 <_ZN8Internal7Binning6bins_tIhhLj31EE18get_quality_factorEv.constprop.20+0x4e>
     406:	83 e1       	ldi	r24, 0x13	; 19
     408:	90 e0       	ldi	r25, 0x00	; 0
     40a:	dc cf       	rjmp	.-72     	; 0x3c4 <_ZN8Internal7Binning6bins_tIhhLj31EE18get_quality_factorEv.constprop.20+0x4e>
     40c:	82 e1       	ldi	r24, 0x12	; 18
     40e:	90 e0       	ldi	r25, 0x00	; 0
     410:	d9 cf       	rjmp	.-78     	; 0x3c4 <_ZN8Internal7Binning6bins_tIhhLj31EE18get_quality_factorEv.constprop.20+0x4e>
     412:	87 e1       	ldi	r24, 0x17	; 23
     414:	90 e0       	ldi	r25, 0x00	; 0
     416:	d6 cf       	rjmp	.-84     	; 0x3c4 <_ZN8Internal7Binning6bins_tIhhLj31EE18get_quality_factorEv.constprop.20+0x4e>
     418:	8c e1       	ldi	r24, 0x1C	; 28
     41a:	90 e0       	ldi	r25, 0x00	; 0
     41c:	d3 cf       	rjmp	.-90     	; 0x3c4 <_ZN8Internal7Binning6bins_tIhhLj31EE18get_quality_factorEv.constprop.20+0x4e>
     41e:	84 e2       	ldi	r24, 0x24	; 36
     420:	90 e0       	ldi	r25, 0x00	; 0
     422:	d0 cf       	rjmp	.-96     	; 0x3c4 <_ZN8Internal7Binning6bins_tIhhLj31EE18get_quality_factorEv.constprop.20+0x4e>
     424:	83 e3       	ldi	r24, 0x33	; 51
     426:	90 e0       	ldi	r25, 0x00	; 0
     428:	cd cf       	rjmp	.-102    	; 0x3c4 <_ZN8Internal7Binning6bins_tIhhLj31EE18get_quality_factorEv.constprop.20+0x4e>
     42a:	99 30       	cpi	r25, 0x09	; 9
     42c:	48 f0       	brcs	.+18     	; 0x440 <__LOCK_REGION_LENGTH__+0x40>
     42e:	3b 30       	cpi	r19, 0x0B	; 11
     430:	a0 f4       	brcc	.+40     	; 0x45a <__LOCK_REGION_LENGTH__+0x5a>
     432:	37 30       	cpi	r19, 0x07	; 7
     434:	a0 f4       	brcc	.+40     	; 0x45e <__LOCK_REGION_LENGTH__+0x5e>
     436:	81 e0       	ldi	r24, 0x01	; 1
     438:	34 30       	cpi	r19, 0x04	; 4
     43a:	08 f4       	brcc	.+2      	; 0x43e <__LOCK_REGION_LENGTH__+0x3e>
     43c:	a5 cf       	rjmp	.-182    	; 0x388 <_ZN8Internal7Binning6bins_tIhhLj31EE18get_quality_factorEv.constprop.20+0x12>
     43e:	08 95       	ret
     440:	95 30       	cpi	r25, 0x05	; 5
     442:	30 f0       	brcs	.+12     	; 0x450 <__LOCK_REGION_LENGTH__+0x50>
     444:	36 30       	cpi	r19, 0x06	; 6
     446:	58 f4       	brcc	.+22     	; 0x45e <__LOCK_REGION_LENGTH__+0x5e>
     448:	81 e0       	ldi	r24, 0x01	; 1
     44a:	23 30       	cpi	r18, 0x03	; 3
     44c:	c0 f7       	brcc	.-16     	; 0x43e <__LOCK_REGION_LENGTH__+0x3e>
     44e:	9c cf       	rjmp	.-200    	; 0x388 <_ZN8Internal7Binning6bins_tIhhLj31EE18get_quality_factorEv.constprop.20+0x12>
     450:	93 30       	cpi	r25, 0x03	; 3
     452:	d0 f7       	brcc	.-12     	; 0x448 <__LOCK_REGION_LENGTH__+0x48>
     454:	83 2f       	mov	r24, r19
     456:	86 95       	lsr	r24
     458:	08 95       	ret
     45a:	83 e0       	ldi	r24, 0x03	; 3
     45c:	08 95       	ret
     45e:	82 e0       	ldi	r24, 0x02	; 2
     460:	ee cf       	rjmp	.-36     	; 0x43e <__LOCK_REGION_LENGTH__+0x3e>

00000462 <_ZN8Internal7Binning6bins_tIhhLj24EE18get_quality_factorEv.constprop.19>:
     462:	8f b7       	in	r24, 0x3f	; 63
     464:	f8 94       	cli
     466:	90 91 1a 04 	lds	r25, 0x041A	; 0x80041a <_ZN8Internal22DCF77_Clock_ControllerI13ConfigurationNS_23DCF77_Frequency_ControlEE12Hour_DecoderE+0x1a>
     46a:	20 91 19 04 	lds	r18, 0x0419	; 0x800419 <_ZN8Internal22DCF77_Clock_ControllerI13ConfigurationNS_23DCF77_Frequency_ControlEE12Hour_DecoderE+0x19>
     46e:	29 17       	cp	r18, r25
     470:	18 f0       	brcs	.+6      	; 0x478 <_ZN8Internal7Binning6bins_tIhhLj24EE18get_quality_factorEv.constprop.19+0x16>
     472:	8f bf       	out	0x3f, r24	; 63
     474:	80 e0       	ldi	r24, 0x00	; 0
     476:	08 95       	ret
     478:	39 2f       	mov	r19, r25
     47a:	32 1b       	sub	r19, r18
     47c:	23 2f       	mov	r18, r19
     47e:	8f bf       	out	0x3f, r24	; 63
     480:	80 e0       	ldi	r24, 0x00	; 0
     482:	9d 31       	cpi	r25, 0x1D	; 29
     484:	40 f4       	brcc	.+16     	; 0x496 <_ZN8Internal7Binning6bins_tIhhLj24EE18get_quality_factorEv.constprop.19+0x34>
     486:	9d 30       	cpi	r25, 0x0D	; 13
     488:	08 f4       	brcc	.+2      	; 0x48c <_ZN8Internal7Binning6bins_tIhhLj24EE18get_quality_factorEv.constprop.19+0x2a>
     48a:	45 c0       	rjmp	.+138    	; 0x516 <_ZN8Internal7Binning6bins_tIhhLj24EE18get_quality_factorEv.constprop.19+0xb4>
     48c:	83 2f       	mov	r24, r19
     48e:	86 95       	lsr	r24
     490:	86 95       	lsr	r24
     492:	08 95       	ret
     494:	83 2f       	mov	r24, r19
     496:	96 95       	lsr	r25
     498:	31 e0       	ldi	r19, 0x01	; 1
     49a:	38 0f       	add	r19, r24
     49c:	91 11       	cpse	r25, r1
     49e:	fa cf       	rjmp	.-12     	; 0x494 <_ZN8Internal7Binning6bins_tIhhLj24EE18get_quality_factorEv.constprop.19+0x32>
     4a0:	8d 30       	cpi	r24, 0x0D	; 13
     4a2:	68 f0       	brcs	.+26     	; 0x4be <_ZN8Internal7Binning6bins_tIhhLj24EE18get_quality_factorEv.constprop.19+0x5c>
     4a4:	8d 30       	cpi	r24, 0x0D	; 13
     4a6:	29 f1       	breq	.+74     	; 0x4f2 <_ZN8Internal7Binning6bins_tIhhLj24EE18get_quality_factorEv.constprop.19+0x90>
     4a8:	8e 30       	cpi	r24, 0x0E	; 14
     4aa:	31 f1       	breq	.+76     	; 0x4f8 <_ZN8Internal7Binning6bins_tIhhLj24EE18get_quality_factorEv.constprop.19+0x96>
     4ac:	81 e1       	ldi	r24, 0x11	; 17
     4ae:	90 e0       	ldi	r25, 0x00	; 0
     4b0:	28 9f       	mul	r18, r24
     4b2:	a0 01       	movw	r20, r0
     4b4:	29 9f       	mul	r18, r25
     4b6:	50 0d       	add	r21, r0
     4b8:	11 24       	eor	r1, r1
     4ba:	85 2f       	mov	r24, r21
     4bc:	08 95       	ret
     4be:	89 30       	cpi	r24, 0x09	; 9
     4c0:	60 f0       	brcs	.+24     	; 0x4da <_ZN8Internal7Binning6bins_tIhhLj24EE18get_quality_factorEv.constprop.19+0x78>
     4c2:	8b 30       	cpi	r24, 0x0B	; 11
     4c4:	28 f0       	brcs	.+10     	; 0x4d0 <_ZN8Internal7Binning6bins_tIhhLj24EE18get_quality_factorEv.constprop.19+0x6e>
     4c6:	8c 30       	cpi	r24, 0x0C	; 12
     4c8:	d1 f4       	brne	.+52     	; 0x4fe <_ZN8Internal7Binning6bins_tIhhLj24EE18get_quality_factorEv.constprop.19+0x9c>
     4ca:	85 e1       	ldi	r24, 0x15	; 21
     4cc:	90 e0       	ldi	r25, 0x00	; 0
     4ce:	f0 cf       	rjmp	.-32     	; 0x4b0 <_ZN8Internal7Binning6bins_tIhhLj24EE18get_quality_factorEv.constprop.19+0x4e>
     4d0:	8a 30       	cpi	r24, 0x0A	; 10
     4d2:	c1 f4       	brne	.+48     	; 0x504 <_ZN8Internal7Binning6bins_tIhhLj24EE18get_quality_factorEv.constprop.19+0xa2>
     4d4:	89 e1       	ldi	r24, 0x19	; 25
     4d6:	90 e0       	ldi	r25, 0x00	; 0
     4d8:	eb cf       	rjmp	.-42     	; 0x4b0 <_ZN8Internal7Binning6bins_tIhhLj24EE18get_quality_factorEv.constprop.19+0x4e>
     4da:	87 30       	cpi	r24, 0x07	; 7
     4dc:	28 f0       	brcs	.+10     	; 0x4e8 <_ZN8Internal7Binning6bins_tIhhLj24EE18get_quality_factorEv.constprop.19+0x86>
     4de:	88 30       	cpi	r24, 0x08	; 8
     4e0:	a1 f4       	brne	.+40     	; 0x50a <_ZN8Internal7Binning6bins_tIhhLj24EE18get_quality_factorEv.constprop.19+0xa8>
     4e2:	80 e2       	ldi	r24, 0x20	; 32
     4e4:	90 e0       	ldi	r25, 0x00	; 0
     4e6:	e4 cf       	rjmp	.-56     	; 0x4b0 <_ZN8Internal7Binning6bins_tIhhLj24EE18get_quality_factorEv.constprop.19+0x4e>
     4e8:	86 30       	cpi	r24, 0x06	; 6
     4ea:	91 f4       	brne	.+36     	; 0x510 <_ZN8Internal7Binning6bins_tIhhLj24EE18get_quality_factorEv.constprop.19+0xae>
     4ec:	8a e2       	ldi	r24, 0x2A	; 42
     4ee:	90 e0       	ldi	r25, 0x00	; 0
     4f0:	df cf       	rjmp	.-66     	; 0x4b0 <_ZN8Internal7Binning6bins_tIhhLj24EE18get_quality_factorEv.constprop.19+0x4e>
     4f2:	83 e1       	ldi	r24, 0x13	; 19
     4f4:	90 e0       	ldi	r25, 0x00	; 0
     4f6:	dc cf       	rjmp	.-72     	; 0x4b0 <_ZN8Internal7Binning6bins_tIhhLj24EE18get_quality_factorEv.constprop.19+0x4e>
     4f8:	82 e1       	ldi	r24, 0x12	; 18
     4fa:	90 e0       	ldi	r25, 0x00	; 0
     4fc:	d9 cf       	rjmp	.-78     	; 0x4b0 <_ZN8Internal7Binning6bins_tIhhLj24EE18get_quality_factorEv.constprop.19+0x4e>
     4fe:	87 e1       	ldi	r24, 0x17	; 23
     500:	90 e0       	ldi	r25, 0x00	; 0
     502:	d6 cf       	rjmp	.-84     	; 0x4b0 <_ZN8Internal7Binning6bins_tIhhLj24EE18get_quality_factorEv.constprop.19+0x4e>
     504:	8c e1       	ldi	r24, 0x1C	; 28
     506:	90 e0       	ldi	r25, 0x00	; 0
     508:	d3 cf       	rjmp	.-90     	; 0x4b0 <_ZN8Internal7Binning6bins_tIhhLj24EE18get_quality_factorEv.constprop.19+0x4e>
     50a:	84 e2       	ldi	r24, 0x24	; 36
     50c:	90 e0       	ldi	r25, 0x00	; 0
     50e:	d0 cf       	rjmp	.-96     	; 0x4b0 <_ZN8Internal7Binning6bins_tIhhLj24EE18get_quality_factorEv.constprop.19+0x4e>
     510:	83 e3       	ldi	r24, 0x33	; 51
     512:	90 e0       	ldi	r25, 0x00	; 0
     514:	cd cf       	rjmp	.-102    	; 0x4b0 <_ZN8Internal7Binning6bins_tIhhLj24EE18get_quality_factorEv.constprop.19+0x4e>
     516:	99 30       	cpi	r25, 0x09	; 9
     518:	48 f0       	brcs	.+18     	; 0x52c <_ZN8Internal7Binning6bins_tIhhLj24EE18get_quality_factorEv.constprop.19+0xca>
     51a:	3b 30       	cpi	r19, 0x0B	; 11
     51c:	a0 f4       	brcc	.+40     	; 0x546 <_ZN8Internal7Binning6bins_tIhhLj24EE18get_quality_factorEv.constprop.19+0xe4>
     51e:	37 30       	cpi	r19, 0x07	; 7
     520:	a0 f4       	brcc	.+40     	; 0x54a <_ZN8Internal7Binning6bins_tIhhLj24EE18get_quality_factorEv.constprop.19+0xe8>
     522:	81 e0       	ldi	r24, 0x01	; 1
     524:	34 30       	cpi	r19, 0x04	; 4
     526:	08 f4       	brcc	.+2      	; 0x52a <_ZN8Internal7Binning6bins_tIhhLj24EE18get_quality_factorEv.constprop.19+0xc8>
     528:	a5 cf       	rjmp	.-182    	; 0x474 <_ZN8Internal7Binning6bins_tIhhLj24EE18get_quality_factorEv.constprop.19+0x12>
     52a:	08 95       	ret
     52c:	95 30       	cpi	r25, 0x05	; 5
     52e:	30 f0       	brcs	.+12     	; 0x53c <_ZN8Internal7Binning6bins_tIhhLj24EE18get_quality_factorEv.constprop.19+0xda>
     530:	36 30       	cpi	r19, 0x06	; 6
     532:	58 f4       	brcc	.+22     	; 0x54a <_ZN8Internal7Binning6bins_tIhhLj24EE18get_quality_factorEv.constprop.19+0xe8>
     534:	81 e0       	ldi	r24, 0x01	; 1
     536:	23 30       	cpi	r18, 0x03	; 3
     538:	c0 f7       	brcc	.-16     	; 0x52a <_ZN8Internal7Binning6bins_tIhhLj24EE18get_quality_factorEv.constprop.19+0xc8>
     53a:	9c cf       	rjmp	.-200    	; 0x474 <_ZN8Internal7Binning6bins_tIhhLj24EE18get_quality_factorEv.constprop.19+0x12>
     53c:	93 30       	cpi	r25, 0x03	; 3
     53e:	d0 f7       	brcc	.-12     	; 0x534 <_ZN8Internal7Binning6bins_tIhhLj24EE18get_quality_factorEv.constprop.19+0xd2>
     540:	83 2f       	mov	r24, r19
     542:	86 95       	lsr	r24
     544:	08 95       	ret
     546:	83 e0       	ldi	r24, 0x03	; 3
     548:	08 95       	ret
     54a:	82 e0       	ldi	r24, 0x02	; 2
     54c:	ee cf       	rjmp	.-36     	; 0x52a <_ZN8Internal7Binning6bins_tIhhLj24EE18get_quality_factorEv.constprop.19+0xc8>

0000054e <twi_init>:
     54e:	10 92 9c 04 	sts	0x049C, r1	; 0x80049c <_state>
     552:	81 e0       	ldi	r24, 0x01	; 1
     554:	80 93 9b 04 	sts	0x049B, r24	; 0x80049b <_send_stop>
     558:	10 92 96 04 	sts	0x0496, r1	; 0x800496 <_rep_start>
     55c:	3c 98       	cbi	0x07, 4	; 7
     55e:	3d 98       	cbi	0x07, 5	; 7
     560:	44 9a       	sbi	0x08, 4	; 8
     562:	45 9a       	sbi	0x08, 5	; 8
     564:	e9 eb       	ldi	r30, 0xB9	; 185
     566:	f0 e0       	ldi	r31, 0x00	; 0
     568:	80 81       	ld	r24, Z
     56a:	8c 7f       	andi	r24, 0xFC	; 252
     56c:	80 83       	st	Z, r24
     56e:	88 e4       	ldi	r24, 0x48	; 72
     570:	80 93 b8 00 	sts	0x00B8, r24	; 0x8000b8 <__TEXT_REGION_LENGTH__+0x7e00b8>
     574:	85 e4       	ldi	r24, 0x45	; 69
     576:	80 93 bc 00 	sts	0x00BC, r24	; 0x8000bc <__TEXT_REGION_LENGTH__+0x7e00bc>
     57a:	08 95       	ret

0000057c <_twi_handle_timeout>:
     57c:	cf 93       	push	r28
     57e:	df 93       	push	r29
     580:	81 e0       	ldi	r24, 0x01	; 1
     582:	80 93 77 03 	sts	0x0377, r24	; 0x800377 <_timed_out>
     586:	80 91 76 03 	lds	r24, 0x0376	; 0x800376 <_reset_on_timeout>
     58a:	88 23       	and	r24, r24
     58c:	91 f0       	breq	.+36     	; 0x5b2 <_twi_handle_timeout+0x36>
     58e:	d0 91 b8 00 	lds	r29, 0x00B8	; 0x8000b8 <__TEXT_REGION_LENGTH__+0x7e00b8>
     592:	c0 91 ba 00 	lds	r28, 0x00BA	; 0x8000ba <__TEXT_REGION_LENGTH__+0x7e00ba>
     596:	80 91 bc 00 	lds	r24, 0x00BC	; 0x8000bc <__TEXT_REGION_LENGTH__+0x7e00bc>
     59a:	8a 7b       	andi	r24, 0xBA	; 186
     59c:	80 93 bc 00 	sts	0x00BC, r24	; 0x8000bc <__TEXT_REGION_LENGTH__+0x7e00bc>
     5a0:	3c 98       	cbi	0x07, 4	; 7
     5a2:	3d 98       	cbi	0x07, 5	; 7
     5a4:	44 98       	cbi	0x08, 4	; 8
     5a6:	45 98       	cbi	0x08, 5	; 8
     5a8:	d2 df       	rcall	.-92     	; 0x54e <twi_init>
     5aa:	d0 93 b8 00 	sts	0x00B8, r29	; 0x8000b8 <__TEXT_REGION_LENGTH__+0x7e00b8>
     5ae:	c0 93 ba 00 	sts	0x00BA, r28	; 0x8000ba <__TEXT_REGION_LENGTH__+0x7e00ba>
     5b2:	df 91       	pop	r29
     5b4:	cf 91       	pop	r28
     5b6:	08 95       	ret

000005b8 <_ZN9DCF77SyncL15_sampleInputPinEv>:
     5b8:	00 b6       	in	r0, 0x30	; 48
     5ba:	05 fe       	sbrs	r0, 5
     5bc:	07 c0       	rjmp	.+14     	; 0x5cc <_ZN9DCF77SyncL15_sampleInputPinEv+0x14>
     5be:	80 91 74 03 	lds	r24, 0x0374	; 0x800374 <FLAG>
     5c2:	87 7f       	andi	r24, 0xF7	; 247
     5c4:	80 93 74 03 	sts	0x0374, r24	; 0x800374 <FLAG>
     5c8:	80 e0       	ldi	r24, 0x00	; 0
     5ca:	08 95       	ret
     5cc:	80 91 74 03 	lds	r24, 0x0374	; 0x800374 <FLAG>
     5d0:	88 60       	ori	r24, 0x08	; 8
     5d2:	80 93 74 03 	sts	0x0374, r24	; 0x800374 <FLAG>
     5d6:	81 e0       	ldi	r24, 0x01	; 1
     5d8:	08 95       	ret

000005da <_ZN7Modules6DS3231L7isValidERKNS0_8DateTimeE>:
     5da:	fc 01       	movw	r30, r24
     5dc:	80 81       	ld	r24, Z
     5de:	8c 33       	cpi	r24, 0x3C	; 60
     5e0:	98 f4       	brcc	.+38     	; 0x608 <_ZN7Modules6DS3231L7isValidERKNS0_8DateTimeE+0x2e>
     5e2:	81 81       	ldd	r24, Z+1	; 0x01
     5e4:	88 31       	cpi	r24, 0x18	; 24
     5e6:	80 f4       	brcc	.+32     	; 0x608 <_ZN7Modules6DS3231L7isValidERKNS0_8DateTimeE+0x2e>
     5e8:	82 81       	ldd	r24, Z+2	; 0x02
     5ea:	81 50       	subi	r24, 0x01	; 1
     5ec:	8f 31       	cpi	r24, 0x1F	; 31
     5ee:	60 f4       	brcc	.+24     	; 0x608 <_ZN7Modules6DS3231L7isValidERKNS0_8DateTimeE+0x2e>
     5f0:	83 81       	ldd	r24, Z+3	; 0x03
     5f2:	81 50       	subi	r24, 0x01	; 1
     5f4:	8c 30       	cpi	r24, 0x0C	; 12
     5f6:	40 f4       	brcc	.+16     	; 0x608 <_ZN7Modules6DS3231L7isValidERKNS0_8DateTimeE+0x2e>
     5f8:	24 81       	ldd	r18, Z+4	; 0x04
     5fa:	35 81       	ldd	r19, Z+5	; 0x05
     5fc:	20 5d       	subi	r18, 0xD0	; 208
     5fe:	37 40       	sbci	r19, 0x07	; 7
     600:	81 e0       	ldi	r24, 0x01	; 1
     602:	24 36       	cpi	r18, 0x64	; 100
     604:	31 05       	cpc	r19, r1
     606:	08 f0       	brcs	.+2      	; 0x60a <_ZN7Modules6DS3231L7isValidERKNS0_8DateTimeE+0x30>
     608:	80 e0       	ldi	r24, 0x00	; 0
     60a:	08 95       	ret

0000060c <_ZN7Modules6DS3231L8decToBcdEh>:
     60c:	9d ec       	ldi	r25, 0xCD	; 205
     60e:	89 9f       	mul	r24, r25
     610:	90 01       	movw	r18, r0
     612:	11 24       	eor	r1, r1
     614:	23 2f       	mov	r18, r19
     616:	33 27       	eor	r19, r19
     618:	26 95       	lsr	r18
     61a:	26 95       	lsr	r18
     61c:	26 95       	lsr	r18
     61e:	96 ef       	ldi	r25, 0xF6	; 246
     620:	29 9f       	mul	r18, r25
     622:	80 0d       	add	r24, r0
     624:	11 24       	eor	r1, r1
     626:	44 e0       	ldi	r20, 0x04	; 4
     628:	22 0f       	add	r18, r18
     62a:	33 1f       	adc	r19, r19
     62c:	4a 95       	dec	r20
     62e:	e1 f7       	brne	.-8      	; 0x628 <_ZN7Modules6DS3231L8decToBcdEh+0x1c>
     630:	82 2b       	or	r24, r18
     632:	08 95       	ret

00000634 <_ZN7Modules6DS3231L8bcdToDecEh>:
     634:	98 2f       	mov	r25, r24
     636:	92 95       	swap	r25
     638:	9f 70       	andi	r25, 0x0F	; 15
     63a:	8f 70       	andi	r24, 0x0F	; 15
     63c:	2a e0       	ldi	r18, 0x0A	; 10
     63e:	92 9f       	mul	r25, r18
     640:	80 0d       	add	r24, r0
     642:	11 24       	eor	r1, r1
     644:	08 95       	ret

00000646 <_ZN8Internal7Binning6bins_tIhhLj60EE18get_quality_factorEv>:
     646:	fc 01       	movw	r30, r24
     648:	3f b7       	in	r19, 0x3f	; 63
     64a:	f8 94       	cli
     64c:	96 ad       	ldd	r25, Z+62	; 0x3e
     64e:	85 ad       	ldd	r24, Z+61	; 0x3d
     650:	89 17       	cp	r24, r25
     652:	18 f0       	brcs	.+6      	; 0x65a <_ZN8Internal7Binning6bins_tIhhLj60EE18get_quality_factorEv+0x14>
     654:	3f bf       	out	0x3f, r19	; 63
     656:	80 e0       	ldi	r24, 0x00	; 0
     658:	08 95       	ret
     65a:	29 2f       	mov	r18, r25
     65c:	28 1b       	sub	r18, r24
     65e:	3f bf       	out	0x3f, r19	; 63
     660:	80 e0       	ldi	r24, 0x00	; 0
     662:	9d 31       	cpi	r25, 0x1D	; 29
     664:	40 f4       	brcc	.+16     	; 0x676 <_ZN8Internal7Binning6bins_tIhhLj60EE18get_quality_factorEv+0x30>
     666:	9d 30       	cpi	r25, 0x0D	; 13
     668:	08 f4       	brcc	.+2      	; 0x66c <_ZN8Internal7Binning6bins_tIhhLj60EE18get_quality_factorEv+0x26>
     66a:	45 c0       	rjmp	.+138    	; 0x6f6 <_ZN8Internal7Binning6bins_tIhhLj60EE18get_quality_factorEv+0xb0>
     66c:	82 2f       	mov	r24, r18
     66e:	86 95       	lsr	r24
     670:	86 95       	lsr	r24
     672:	08 95       	ret
     674:	83 2f       	mov	r24, r19
     676:	96 95       	lsr	r25
     678:	31 e0       	ldi	r19, 0x01	; 1
     67a:	38 0f       	add	r19, r24
     67c:	91 11       	cpse	r25, r1
     67e:	fa cf       	rjmp	.-12     	; 0x674 <_ZN8Internal7Binning6bins_tIhhLj60EE18get_quality_factorEv+0x2e>
     680:	8d 30       	cpi	r24, 0x0D	; 13
     682:	68 f0       	brcs	.+26     	; 0x69e <_ZN8Internal7Binning6bins_tIhhLj60EE18get_quality_factorEv+0x58>
     684:	8d 30       	cpi	r24, 0x0D	; 13
     686:	29 f1       	breq	.+74     	; 0x6d2 <_ZN8Internal7Binning6bins_tIhhLj60EE18get_quality_factorEv+0x8c>
     688:	8e 30       	cpi	r24, 0x0E	; 14
     68a:	31 f1       	breq	.+76     	; 0x6d8 <_ZN8Internal7Binning6bins_tIhhLj60EE18get_quality_factorEv+0x92>
     68c:	81 e1       	ldi	r24, 0x11	; 17
     68e:	90 e0       	ldi	r25, 0x00	; 0
     690:	28 9f       	mul	r18, r24
     692:	a0 01       	movw	r20, r0
     694:	29 9f       	mul	r18, r25
     696:	50 0d       	add	r21, r0
     698:	11 24       	eor	r1, r1
     69a:	85 2f       	mov	r24, r21
     69c:	08 95       	ret
     69e:	89 30       	cpi	r24, 0x09	; 9
     6a0:	60 f0       	brcs	.+24     	; 0x6ba <_ZN8Internal7Binning6bins_tIhhLj60EE18get_quality_factorEv+0x74>
     6a2:	8b 30       	cpi	r24, 0x0B	; 11
     6a4:	28 f0       	brcs	.+10     	; 0x6b0 <_ZN8Internal7Binning6bins_tIhhLj60EE18get_quality_factorEv+0x6a>
     6a6:	8c 30       	cpi	r24, 0x0C	; 12
     6a8:	d1 f4       	brne	.+52     	; 0x6de <_ZN8Internal7Binning6bins_tIhhLj60EE18get_quality_factorEv+0x98>
     6aa:	85 e1       	ldi	r24, 0x15	; 21
     6ac:	90 e0       	ldi	r25, 0x00	; 0
     6ae:	f0 cf       	rjmp	.-32     	; 0x690 <_ZN8Internal7Binning6bins_tIhhLj60EE18get_quality_factorEv+0x4a>
     6b0:	8a 30       	cpi	r24, 0x0A	; 10
     6b2:	c1 f4       	brne	.+48     	; 0x6e4 <_ZN8Internal7Binning6bins_tIhhLj60EE18get_quality_factorEv+0x9e>
     6b4:	89 e1       	ldi	r24, 0x19	; 25
     6b6:	90 e0       	ldi	r25, 0x00	; 0
     6b8:	eb cf       	rjmp	.-42     	; 0x690 <_ZN8Internal7Binning6bins_tIhhLj60EE18get_quality_factorEv+0x4a>
     6ba:	87 30       	cpi	r24, 0x07	; 7
     6bc:	28 f0       	brcs	.+10     	; 0x6c8 <_ZN8Internal7Binning6bins_tIhhLj60EE18get_quality_factorEv+0x82>
     6be:	88 30       	cpi	r24, 0x08	; 8
     6c0:	a1 f4       	brne	.+40     	; 0x6ea <_ZN8Internal7Binning6bins_tIhhLj60EE18get_quality_factorEv+0xa4>
     6c2:	80 e2       	ldi	r24, 0x20	; 32
     6c4:	90 e0       	ldi	r25, 0x00	; 0
     6c6:	e4 cf       	rjmp	.-56     	; 0x690 <_ZN8Internal7Binning6bins_tIhhLj60EE18get_quality_factorEv+0x4a>
     6c8:	86 30       	cpi	r24, 0x06	; 6
     6ca:	91 f4       	brne	.+36     	; 0x6f0 <_ZN8Internal7Binning6bins_tIhhLj60EE18get_quality_factorEv+0xaa>
     6cc:	8a e2       	ldi	r24, 0x2A	; 42
     6ce:	90 e0       	ldi	r25, 0x00	; 0
     6d0:	df cf       	rjmp	.-66     	; 0x690 <_ZN8Internal7Binning6bins_tIhhLj60EE18get_quality_factorEv+0x4a>
     6d2:	83 e1       	ldi	r24, 0x13	; 19
     6d4:	90 e0       	ldi	r25, 0x00	; 0
     6d6:	dc cf       	rjmp	.-72     	; 0x690 <_ZN8Internal7Binning6bins_tIhhLj60EE18get_quality_factorEv+0x4a>
     6d8:	82 e1       	ldi	r24, 0x12	; 18
     6da:	90 e0       	ldi	r25, 0x00	; 0
     6dc:	d9 cf       	rjmp	.-78     	; 0x690 <_ZN8Internal7Binning6bins_tIhhLj60EE18get_quality_factorEv+0x4a>
     6de:	87 e1       	ldi	r24, 0x17	; 23
     6e0:	90 e0       	ldi	r25, 0x00	; 0
     6e2:	d6 cf       	rjmp	.-84     	; 0x690 <_ZN8Internal7Binning6bins_tIhhLj60EE18get_quality_factorEv+0x4a>
     6e4:	8c e1       	ldi	r24, 0x1C	; 28
     6e6:	90 e0       	ldi	r25, 0x00	; 0
     6e8:	d3 cf       	rjmp	.-90     	; 0x690 <_ZN8Internal7Binning6bins_tIhhLj60EE18get_quality_factorEv+0x4a>
     6ea:	84 e2       	ldi	r24, 0x24	; 36
     6ec:	90 e0       	ldi	r25, 0x00	; 0
     6ee:	d0 cf       	rjmp	.-96     	; 0x690 <_ZN8Internal7Binning6bins_tIhhLj60EE18get_quality_factorEv+0x4a>
     6f0:	83 e3       	ldi	r24, 0x33	; 51
     6f2:	90 e0       	ldi	r25, 0x00	; 0
     6f4:	cd cf       	rjmp	.-102    	; 0x690 <_ZN8Internal7Binning6bins_tIhhLj60EE18get_quality_factorEv+0x4a>
     6f6:	99 30       	cpi	r25, 0x09	; 9
     6f8:	48 f0       	brcs	.+18     	; 0x70c <_ZN8Internal7Binning6bins_tIhhLj60EE18get_quality_factorEv+0xc6>
     6fa:	2b 30       	cpi	r18, 0x0B	; 11
     6fc:	a0 f4       	brcc	.+40     	; 0x726 <_ZN8Internal7Binning6bins_tIhhLj60EE18get_quality_factorEv+0xe0>
     6fe:	27 30       	cpi	r18, 0x07	; 7
     700:	a0 f4       	brcc	.+40     	; 0x72a <_ZN8Internal7Binning6bins_tIhhLj60EE18get_quality_factorEv+0xe4>
     702:	81 e0       	ldi	r24, 0x01	; 1
     704:	24 30       	cpi	r18, 0x04	; 4
     706:	08 f4       	brcc	.+2      	; 0x70a <_ZN8Internal7Binning6bins_tIhhLj60EE18get_quality_factorEv+0xc4>
     708:	a6 cf       	rjmp	.-180    	; 0x656 <_ZN8Internal7Binning6bins_tIhhLj60EE18get_quality_factorEv+0x10>
     70a:	08 95       	ret
     70c:	95 30       	cpi	r25, 0x05	; 5
     70e:	30 f0       	brcs	.+12     	; 0x71c <_ZN8Internal7Binning6bins_tIhhLj60EE18get_quality_factorEv+0xd6>
     710:	26 30       	cpi	r18, 0x06	; 6
     712:	58 f4       	brcc	.+22     	; 0x72a <_ZN8Internal7Binning6bins_tIhhLj60EE18get_quality_factorEv+0xe4>
     714:	81 e0       	ldi	r24, 0x01	; 1
     716:	23 30       	cpi	r18, 0x03	; 3
     718:	c0 f7       	brcc	.-16     	; 0x70a <_ZN8Internal7Binning6bins_tIhhLj60EE18get_quality_factorEv+0xc4>
     71a:	9d cf       	rjmp	.-198    	; 0x656 <_ZN8Internal7Binning6bins_tIhhLj60EE18get_quality_factorEv+0x10>
     71c:	93 30       	cpi	r25, 0x03	; 3
     71e:	d0 f7       	brcc	.-12     	; 0x714 <_ZN8Internal7Binning6bins_tIhhLj60EE18get_quality_factorEv+0xce>
     720:	82 2f       	mov	r24, r18
     722:	86 95       	lsr	r24
     724:	08 95       	ret
     726:	83 e0       	ldi	r24, 0x03	; 3
     728:	08 95       	ret
     72a:	82 e0       	ldi	r24, 0x02	; 2
     72c:	ee cf       	rjmp	.-36     	; 0x70a <_ZN8Internal7Binning6bins_tIhhLj60EE18get_quality_factorEv+0xc4>

0000072e <_ZN8Internal7Binning5scoreIhhLh1EEEvRT_T0_b>:
     72e:	fc 01       	movw	r30, r24
     730:	90 81       	ld	r25, Z
     732:	44 23       	and	r20, r20
     734:	19 f0       	breq	.+6      	; 0x73c <_ZN8Internal7Binning5scoreIhhLh1EEEvRT_T0_b+0xe>
     736:	69 0f       	add	r22, r25
     738:	60 83       	st	Z, r22
     73a:	08 95       	ret
     73c:	96 1b       	sub	r25, r22
     73e:	9f 5f       	subi	r25, 0xFF	; 255
     740:	90 83       	st	Z, r25
     742:	08 95       	ret

00000744 <_ZN8Internal7Binning7DecoderIhLj60EE17compute_max_indexEv>:
     744:	fc 01       	movw	r30, r24
     746:	15 ae       	std	Z+61, r1	; 0x3d
     748:	16 ae       	std	Z+62, r1	; 0x3e
     74a:	8d e3       	ldi	r24, 0x3D	; 61
     74c:	87 af       	std	Z+63, r24	; 0x3f
     74e:	df 01       	movw	r26, r30
     750:	80 e0       	ldi	r24, 0x00	; 0
     752:	9d 91       	ld	r25, X+
     754:	26 ad       	ldd	r18, Z+62	; 0x3e
     756:	92 17       	cp	r25, r18
     758:	38 f0       	brcs	.+14     	; 0x768 <_ZN8Internal7Binning7DecoderIhLj60EE17compute_max_indexEv+0x24>
     75a:	25 af       	std	Z+61, r18	; 0x3d
     75c:	96 af       	std	Z+62, r25	; 0x3e
     75e:	87 af       	std	Z+63, r24	; 0x3f
     760:	8f 5f       	subi	r24, 0xFF	; 255
     762:	8c 33       	cpi	r24, 0x3C	; 60
     764:	b1 f7       	brne	.-20     	; 0x752 <_ZN8Internal7Binning7DecoderIhLj60EE17compute_max_indexEv+0xe>
     766:	08 95       	ret
     768:	25 ad       	ldd	r18, Z+61	; 0x3d
     76a:	29 17       	cp	r18, r25
     76c:	c8 f7       	brcc	.-14     	; 0x760 <_ZN8Internal7Binning7DecoderIhLj60EE17compute_max_indexEv+0x1c>
     76e:	95 af       	std	Z+61, r25	; 0x3d
     770:	f7 cf       	rjmp	.-18     	; 0x760 <_ZN8Internal7Binning7DecoderIhLj60EE17compute_max_indexEv+0x1c>

00000772 <_ZN8Internal7Binning6bins_tIhhLj60EE5setupEv>:
     772:	fc 01       	movw	r30, r24
     774:	dc 01       	movw	r26, r24
     776:	cc 96       	adiw	r24, 0x3c	; 60
     778:	1d 92       	st	X+, r1
     77a:	a8 17       	cp	r26, r24
     77c:	b9 07       	cpc	r27, r25
     77e:	e1 f7       	brne	.-8      	; 0x778 <_ZN8Internal7Binning6bins_tIhhLj60EE5setupEv+0x6>
     780:	14 ae       	std	Z+60, r1	; 0x3c
     782:	16 ae       	std	Z+62, r1	; 0x3e
     784:	8d e3       	ldi	r24, 0x3D	; 61
     786:	87 af       	std	Z+63, r24	; 0x3f
     788:	15 ae       	std	Z+61, r1	; 0x3d
     78a:	08 95       	ret

0000078c <_ZN8Internal22DCF77_Clock_ControllerI13ConfigurationNS_23DCF77_Frequency_ControlEE24phase_lost_event_handlerEv>:
     78c:	8c e2       	ldi	r24, 0x2C	; 44
     78e:	91 e0       	ldi	r25, 0x01	; 1
     790:	90 93 dd 05 	sts	0x05DD, r25	; 0x8005dd <_ZN8Internal22DCF77_Clock_ControllerI13ConfigurationNS_23DCF77_Frequency_ControlEE11DemodulatorE+0xd3>
     794:	80 93 dc 05 	sts	0x05DC, r24	; 0x8005dc <_ZN8Internal22DCF77_Clock_ControllerI13ConfigurationNS_23DCF77_Frequency_ControlEE11DemodulatorE+0xd2>
     798:	88 eb       	ldi	r24, 0xB8	; 184
     79a:	93 e0       	ldi	r25, 0x03	; 3
     79c:	ea df       	rcall	.-44     	; 0x772 <_ZN8Internal7Binning6bins_tIhhLj60EE5setupEv>
     79e:	8f ef       	ldi	r24, 0xFF	; 255
     7a0:	80 93 fe 03 	sts	0x03FE, r24	; 0x8003fe <_ZN8Internal22DCF77_Clock_ControllerI13ConfigurationNS_23DCF77_Frequency_ControlEE14Second_DecoderE+0x46>
     7a4:	80 93 ff 03 	sts	0x03FF, r24	; 0x8003ff <_ZN8Internal22DCF77_Clock_ControllerI13ConfigurationNS_23DCF77_Frequency_ControlEE14Second_DecoderE+0x47>
     7a8:	88 e7       	ldi	r24, 0x78	; 120
     7aa:	93 e0       	ldi	r25, 0x03	; 3
     7ac:	e2 df       	rcall	.-60     	; 0x772 <_ZN8Internal7Binning6bins_tIhhLj60EE5setupEv>
     7ae:	e0 e0       	ldi	r30, 0x00	; 0
     7b0:	f4 e0       	ldi	r31, 0x04	; 4
     7b2:	88 e1       	ldi	r24, 0x18	; 24
     7b4:	94 e0       	ldi	r25, 0x04	; 4
     7b6:	11 92       	st	Z+, r1
     7b8:	8e 17       	cp	r24, r30
     7ba:	9f 07       	cpc	r25, r31
     7bc:	e1 f7       	brne	.-8      	; 0x7b6 <_ZN8Internal22DCF77_Clock_ControllerI13ConfigurationNS_23DCF77_Frequency_ControlEE24phase_lost_event_handlerEv+0x2a>
     7be:	10 92 18 04 	sts	0x0418, r1	; 0x800418 <_ZN8Internal22DCF77_Clock_ControllerI13ConfigurationNS_23DCF77_Frequency_ControlEE12Hour_DecoderE+0x18>
     7c2:	10 92 1a 04 	sts	0x041A, r1	; 0x80041a <_ZN8Internal22DCF77_Clock_ControllerI13ConfigurationNS_23DCF77_Frequency_ControlEE12Hour_DecoderE+0x1a>
     7c6:	89 e1       	ldi	r24, 0x19	; 25
     7c8:	80 93 1b 04 	sts	0x041B, r24	; 0x80041b <_ZN8Internal22DCF77_Clock_ControllerI13ConfigurationNS_23DCF77_Frequency_ControlEE12Hour_DecoderE+0x1b>
     7cc:	10 92 19 04 	sts	0x0419, r1	; 0x800419 <_ZN8Internal22DCF77_Clock_ControllerI13ConfigurationNS_23DCF77_Frequency_ControlEE12Hour_DecoderE+0x19>
     7d0:	e7 e2       	ldi	r30, 0x27	; 39
     7d2:	f4 e0       	ldi	r31, 0x04	; 4
     7d4:	11 92       	st	Z+, r1
     7d6:	84 e0       	ldi	r24, 0x04	; 4
     7d8:	e6 34       	cpi	r30, 0x46	; 70
     7da:	f8 07       	cpc	r31, r24
     7dc:	d9 f7       	brne	.-10     	; 0x7d4 <_ZN8Internal22DCF77_Clock_ControllerI13ConfigurationNS_23DCF77_Frequency_ControlEE24phase_lost_event_handlerEv+0x48>
     7de:	10 92 46 04 	sts	0x0446, r1	; 0x800446 <_ZN8Internal22DCF77_Clock_ControllerI13ConfigurationNS_23DCF77_Frequency_ControlEE11Day_DecoderE+0x1f>
     7e2:	10 92 48 04 	sts	0x0448, r1	; 0x800448 <_ZN8Internal22DCF77_Clock_ControllerI13ConfigurationNS_23DCF77_Frequency_ControlEE11Day_DecoderE+0x21>
     7e6:	80 e2       	ldi	r24, 0x20	; 32
     7e8:	80 93 49 04 	sts	0x0449, r24	; 0x800449 <_ZN8Internal22DCF77_Clock_ControllerI13ConfigurationNS_23DCF77_Frequency_ControlEE11Day_DecoderE+0x22>
     7ec:	10 92 47 04 	sts	0x0447, r1	; 0x800447 <_ZN8Internal22DCF77_Clock_ControllerI13ConfigurationNS_23DCF77_Frequency_ControlEE11Day_DecoderE+0x20>
     7f0:	10 92 1c 04 	sts	0x041C, r1	; 0x80041c <_ZN8Internal22DCF77_Clock_ControllerI13ConfigurationNS_23DCF77_Frequency_ControlEE15Weekday_DecoderE>
     7f4:	10 92 1d 04 	sts	0x041D, r1	; 0x80041d <_ZN8Internal22DCF77_Clock_ControllerI13ConfigurationNS_23DCF77_Frequency_ControlEE15Weekday_DecoderE+0x1>
     7f8:	10 92 1e 04 	sts	0x041E, r1	; 0x80041e <_ZN8Internal22DCF77_Clock_ControllerI13ConfigurationNS_23DCF77_Frequency_ControlEE15Weekday_DecoderE+0x2>
     7fc:	10 92 1f 04 	sts	0x041F, r1	; 0x80041f <_ZN8Internal22DCF77_Clock_ControllerI13ConfigurationNS_23DCF77_Frequency_ControlEE15Weekday_DecoderE+0x3>
     800:	10 92 20 04 	sts	0x0420, r1	; 0x800420 <_ZN8Internal22DCF77_Clock_ControllerI13ConfigurationNS_23DCF77_Frequency_ControlEE15Weekday_DecoderE+0x4>
     804:	10 92 21 04 	sts	0x0421, r1	; 0x800421 <_ZN8Internal22DCF77_Clock_ControllerI13ConfigurationNS_23DCF77_Frequency_ControlEE15Weekday_DecoderE+0x5>
     808:	10 92 22 04 	sts	0x0422, r1	; 0x800422 <_ZN8Internal22DCF77_Clock_ControllerI13ConfigurationNS_23DCF77_Frequency_ControlEE15Weekday_DecoderE+0x6>
     80c:	10 92 23 04 	sts	0x0423, r1	; 0x800423 <_ZN8Internal22DCF77_Clock_ControllerI13ConfigurationNS_23DCF77_Frequency_ControlEE15Weekday_DecoderE+0x7>
     810:	10 92 25 04 	sts	0x0425, r1	; 0x800425 <_ZN8Internal22DCF77_Clock_ControllerI13ConfigurationNS_23DCF77_Frequency_ControlEE15Weekday_DecoderE+0x9>
     814:	88 e0       	ldi	r24, 0x08	; 8
     816:	80 93 26 04 	sts	0x0426, r24	; 0x800426 <_ZN8Internal22DCF77_Clock_ControllerI13ConfigurationNS_23DCF77_Frequency_ControlEE15Weekday_DecoderE+0xa>
     81a:	10 92 24 04 	sts	0x0424, r1	; 0x800424 <_ZN8Internal22DCF77_Clock_ControllerI13ConfigurationNS_23DCF77_Frequency_ControlEE15Weekday_DecoderE+0x8>
     81e:	ea e4       	ldi	r30, 0x4A	; 74
     820:	f4 e0       	ldi	r31, 0x04	; 4
     822:	86 e5       	ldi	r24, 0x56	; 86
     824:	94 e0       	ldi	r25, 0x04	; 4
     826:	11 92       	st	Z+, r1
     828:	8e 17       	cp	r24, r30
     82a:	9f 07       	cpc	r25, r31
     82c:	e1 f7       	brne	.-8      	; 0x826 <_ZN8Internal22DCF77_Clock_ControllerI13ConfigurationNS_23DCF77_Frequency_ControlEE24phase_lost_event_handlerEv+0x9a>
     82e:	10 92 56 04 	sts	0x0456, r1	; 0x800456 <_ZN8Internal22DCF77_Clock_ControllerI13ConfigurationNS_23DCF77_Frequency_ControlEE13Month_DecoderE+0xc>
     832:	10 92 58 04 	sts	0x0458, r1	; 0x800458 <_ZN8Internal22DCF77_Clock_ControllerI13ConfigurationNS_23DCF77_Frequency_ControlEE13Month_DecoderE+0xe>
     836:	8d e0       	ldi	r24, 0x0D	; 13
     838:	80 93 59 04 	sts	0x0459, r24	; 0x800459 <_ZN8Internal22DCF77_Clock_ControllerI13ConfigurationNS_23DCF77_Frequency_ControlEE13Month_DecoderE+0xf>
     83c:	10 92 57 04 	sts	0x0457, r1	; 0x800457 <_ZN8Internal22DCF77_Clock_ControllerI13ConfigurationNS_23DCF77_Frequency_ControlEE13Month_DecoderE+0xd>
     840:	a5 cc       	rjmp	.-1718   	; 0x18c <_ZN8Internal18DCF77_Year_Decoder5setupEv.constprop.68>

00000842 <_ZN8Internal7Binning6bins_tIhhLj10EE18get_quality_factorEv>:
     842:	fc 01       	movw	r30, r24
     844:	3f b7       	in	r19, 0x3f	; 63
     846:	f8 94       	cli
     848:	94 85       	ldd	r25, Z+12	; 0x0c
     84a:	83 85       	ldd	r24, Z+11	; 0x0b
     84c:	89 17       	cp	r24, r25
     84e:	18 f0       	brcs	.+6      	; 0x856 <_ZN8Internal7Binning6bins_tIhhLj10EE18get_quality_factorEv+0x14>
     850:	3f bf       	out	0x3f, r19	; 63
     852:	80 e0       	ldi	r24, 0x00	; 0
     854:	08 95       	ret
     856:	29 2f       	mov	r18, r25
     858:	28 1b       	sub	r18, r24
     85a:	3f bf       	out	0x3f, r19	; 63
     85c:	80 e0       	ldi	r24, 0x00	; 0
     85e:	9d 31       	cpi	r25, 0x1D	; 29
     860:	40 f4       	brcc	.+16     	; 0x872 <_ZN8Internal7Binning6bins_tIhhLj10EE18get_quality_factorEv+0x30>
     862:	9d 30       	cpi	r25, 0x0D	; 13
     864:	08 f4       	brcc	.+2      	; 0x868 <_ZN8Internal7Binning6bins_tIhhLj10EE18get_quality_factorEv+0x26>
     866:	45 c0       	rjmp	.+138    	; 0x8f2 <_ZN8Internal7Binning6bins_tIhhLj10EE18get_quality_factorEv+0xb0>
     868:	82 2f       	mov	r24, r18
     86a:	86 95       	lsr	r24
     86c:	86 95       	lsr	r24
     86e:	08 95       	ret
     870:	83 2f       	mov	r24, r19
     872:	96 95       	lsr	r25
     874:	31 e0       	ldi	r19, 0x01	; 1
     876:	38 0f       	add	r19, r24
     878:	91 11       	cpse	r25, r1
     87a:	fa cf       	rjmp	.-12     	; 0x870 <_ZN8Internal7Binning6bins_tIhhLj10EE18get_quality_factorEv+0x2e>
     87c:	8d 30       	cpi	r24, 0x0D	; 13
     87e:	68 f0       	brcs	.+26     	; 0x89a <_ZN8Internal7Binning6bins_tIhhLj10EE18get_quality_factorEv+0x58>
     880:	8d 30       	cpi	r24, 0x0D	; 13
     882:	29 f1       	breq	.+74     	; 0x8ce <_ZN8Internal7Binning6bins_tIhhLj10EE18get_quality_factorEv+0x8c>
     884:	8e 30       	cpi	r24, 0x0E	; 14
     886:	31 f1       	breq	.+76     	; 0x8d4 <_ZN8Internal7Binning6bins_tIhhLj10EE18get_quality_factorEv+0x92>
     888:	81 e1       	ldi	r24, 0x11	; 17
     88a:	90 e0       	ldi	r25, 0x00	; 0
     88c:	28 9f       	mul	r18, r24
     88e:	a0 01       	movw	r20, r0
     890:	29 9f       	mul	r18, r25
     892:	50 0d       	add	r21, r0
     894:	11 24       	eor	r1, r1
     896:	85 2f       	mov	r24, r21
     898:	08 95       	ret
     89a:	89 30       	cpi	r24, 0x09	; 9
     89c:	60 f0       	brcs	.+24     	; 0x8b6 <_ZN8Internal7Binning6bins_tIhhLj10EE18get_quality_factorEv+0x74>
     89e:	8b 30       	cpi	r24, 0x0B	; 11
     8a0:	28 f0       	brcs	.+10     	; 0x8ac <_ZN8Internal7Binning6bins_tIhhLj10EE18get_quality_factorEv+0x6a>
     8a2:	8c 30       	cpi	r24, 0x0C	; 12
     8a4:	d1 f4       	brne	.+52     	; 0x8da <_ZN8Internal7Binning6bins_tIhhLj10EE18get_quality_factorEv+0x98>
     8a6:	85 e1       	ldi	r24, 0x15	; 21
     8a8:	90 e0       	ldi	r25, 0x00	; 0
     8aa:	f0 cf       	rjmp	.-32     	; 0x88c <_ZN8Internal7Binning6bins_tIhhLj10EE18get_quality_factorEv+0x4a>
     8ac:	8a 30       	cpi	r24, 0x0A	; 10
     8ae:	c1 f4       	brne	.+48     	; 0x8e0 <_ZN8Internal7Binning6bins_tIhhLj10EE18get_quality_factorEv+0x9e>
     8b0:	89 e1       	ldi	r24, 0x19	; 25
     8b2:	90 e0       	ldi	r25, 0x00	; 0
     8b4:	eb cf       	rjmp	.-42     	; 0x88c <_ZN8Internal7Binning6bins_tIhhLj10EE18get_quality_factorEv+0x4a>
     8b6:	87 30       	cpi	r24, 0x07	; 7
     8b8:	28 f0       	brcs	.+10     	; 0x8c4 <_ZN8Internal7Binning6bins_tIhhLj10EE18get_quality_factorEv+0x82>
     8ba:	88 30       	cpi	r24, 0x08	; 8
     8bc:	a1 f4       	brne	.+40     	; 0x8e6 <_ZN8Internal7Binning6bins_tIhhLj10EE18get_quality_factorEv+0xa4>
     8be:	80 e2       	ldi	r24, 0x20	; 32
     8c0:	90 e0       	ldi	r25, 0x00	; 0
     8c2:	e4 cf       	rjmp	.-56     	; 0x88c <_ZN8Internal7Binning6bins_tIhhLj10EE18get_quality_factorEv+0x4a>
     8c4:	86 30       	cpi	r24, 0x06	; 6
     8c6:	91 f4       	brne	.+36     	; 0x8ec <_ZN8Internal7Binning6bins_tIhhLj10EE18get_quality_factorEv+0xaa>
     8c8:	8a e2       	ldi	r24, 0x2A	; 42
     8ca:	90 e0       	ldi	r25, 0x00	; 0
     8cc:	df cf       	rjmp	.-66     	; 0x88c <_ZN8Internal7Binning6bins_tIhhLj10EE18get_quality_factorEv+0x4a>
     8ce:	83 e1       	ldi	r24, 0x13	; 19
     8d0:	90 e0       	ldi	r25, 0x00	; 0
     8d2:	dc cf       	rjmp	.-72     	; 0x88c <_ZN8Internal7Binning6bins_tIhhLj10EE18get_quality_factorEv+0x4a>
     8d4:	82 e1       	ldi	r24, 0x12	; 18
     8d6:	90 e0       	ldi	r25, 0x00	; 0
     8d8:	d9 cf       	rjmp	.-78     	; 0x88c <_ZN8Internal7Binning6bins_tIhhLj10EE18get_quality_factorEv+0x4a>
     8da:	87 e1       	ldi	r24, 0x17	; 23
     8dc:	90 e0       	ldi	r25, 0x00	; 0
     8de:	d6 cf       	rjmp	.-84     	; 0x88c <_ZN8Internal7Binning6bins_tIhhLj10EE18get_quality_factorEv+0x4a>
     8e0:	8c e1       	ldi	r24, 0x1C	; 28
     8e2:	90 e0       	ldi	r25, 0x00	; 0
     8e4:	d3 cf       	rjmp	.-90     	; 0x88c <_ZN8Internal7Binning6bins_tIhhLj10EE18get_quality_factorEv+0x4a>
     8e6:	84 e2       	ldi	r24, 0x24	; 36
     8e8:	90 e0       	ldi	r25, 0x00	; 0
     8ea:	d0 cf       	rjmp	.-96     	; 0x88c <_ZN8Internal7Binning6bins_tIhhLj10EE18get_quality_factorEv+0x4a>
     8ec:	83 e3       	ldi	r24, 0x33	; 51
     8ee:	90 e0       	ldi	r25, 0x00	; 0
     8f0:	cd cf       	rjmp	.-102    	; 0x88c <_ZN8Internal7Binning6bins_tIhhLj10EE18get_quality_factorEv+0x4a>
     8f2:	99 30       	cpi	r25, 0x09	; 9
     8f4:	48 f0       	brcs	.+18     	; 0x908 <__stack+0x9>
     8f6:	2b 30       	cpi	r18, 0x0B	; 11
     8f8:	a0 f4       	brcc	.+40     	; 0x922 <__stack+0x23>
     8fa:	27 30       	cpi	r18, 0x07	; 7
     8fc:	a0 f4       	brcc	.+40     	; 0x926 <__stack+0x27>
     8fe:	81 e0       	ldi	r24, 0x01	; 1
     900:	24 30       	cpi	r18, 0x04	; 4
     902:	08 f4       	brcc	.+2      	; 0x906 <__stack+0x7>
     904:	a6 cf       	rjmp	.-180    	; 0x852 <_ZN8Internal7Binning6bins_tIhhLj10EE18get_quality_factorEv+0x10>
     906:	08 95       	ret
     908:	95 30       	cpi	r25, 0x05	; 5
     90a:	30 f0       	brcs	.+12     	; 0x918 <__stack+0x19>
     90c:	26 30       	cpi	r18, 0x06	; 6
     90e:	58 f4       	brcc	.+22     	; 0x926 <__stack+0x27>
     910:	81 e0       	ldi	r24, 0x01	; 1
     912:	23 30       	cpi	r18, 0x03	; 3
     914:	c0 f7       	brcc	.-16     	; 0x906 <__stack+0x7>
     916:	9d cf       	rjmp	.-198    	; 0x852 <_ZN8Internal7Binning6bins_tIhhLj10EE18get_quality_factorEv+0x10>
     918:	93 30       	cpi	r25, 0x03	; 3
     91a:	d0 f7       	brcc	.-12     	; 0x910 <__stack+0x11>
     91c:	82 2f       	mov	r24, r18
     91e:	86 95       	lsr	r24
     920:	08 95       	ret
     922:	83 e0       	ldi	r24, 0x03	; 3
     924:	08 95       	ret
     926:	82 e0       	ldi	r24, 0x02	; 2
     928:	ee cf       	rjmp	.-36     	; 0x906 <__stack+0x7>

0000092a <_ZN8Internal23Generic_1_kHz_Generator13zero_providerEv>:
     92a:	80 e0       	ldi	r24, 0x00	; 0
     92c:	08 95       	ret

0000092e <_ZNK8Internal13DCF77_Encoder28verify_leap_second_scheduledEb>:
     92e:	fc 01       	movw	r30, r24
     930:	82 81       	ldd	r24, Z+2	; 0x02
     932:	90 e0       	ldi	r25, 0x00	; 0
     934:	81 30       	cpi	r24, 0x01	; 1
     936:	39 f4       	brne	.+14     	; 0x946 <_ZNK8Internal13DCF77_Encoder28verify_leap_second_scheduledEb+0x18>
     938:	91 e0       	ldi	r25, 0x01	; 1
     93a:	61 11       	cpse	r22, r1
     93c:	04 c0       	rjmp	.+8      	; 0x946 <_ZNK8Internal13DCF77_Encoder28verify_leap_second_scheduledEb+0x18>
     93e:	97 81       	ldd	r25, Z+7	; 0x07
     940:	93 fb       	bst	r25, 3
     942:	99 27       	eor	r25, r25
     944:	90 f9       	bld	r25, 0
     946:	81 81       	ldd	r24, Z+1	; 0x01
     948:	81 30       	cpi	r24, 0x01	; 1
     94a:	81 f4       	brne	.+32     	; 0x96c <_ZNK8Internal13DCF77_Encoder28verify_leap_second_scheduledEb+0x3e>
     94c:	84 81       	ldd	r24, Z+4	; 0x04
     94e:	81 11       	cpse	r24, r1
     950:	06 c0       	rjmp	.+12     	; 0x95e <_ZNK8Internal13DCF77_Encoder28verify_leap_second_scheduledEb+0x30>
     952:	81 e0       	ldi	r24, 0x01	; 1
     954:	25 81       	ldd	r18, Z+5	; 0x05
     956:	21 11       	cpse	r18, r1
     958:	07 c0       	rjmp	.+14     	; 0x968 <_ZNK8Internal13DCF77_Encoder28verify_leap_second_scheduledEb+0x3a>
     95a:	80 e0       	ldi	r24, 0x00	; 0
     95c:	05 c0       	rjmp	.+10     	; 0x968 <_ZNK8Internal13DCF77_Encoder28verify_leap_second_scheduledEb+0x3a>
     95e:	81 30       	cpi	r24, 0x01	; 1
     960:	e1 f7       	brne	.-8      	; 0x95a <_ZNK8Internal13DCF77_Encoder28verify_leap_second_scheduledEb+0x2c>
     962:	25 81       	ldd	r18, Z+5	; 0x05
     964:	21 11       	cpse	r18, r1
     966:	f9 cf       	rjmp	.-14     	; 0x95a <_ZNK8Internal13DCF77_Encoder28verify_leap_second_scheduledEb+0x2c>
     968:	89 23       	and	r24, r25
     96a:	08 95       	ret
     96c:	87 30       	cpi	r24, 0x07	; 7
     96e:	21 f0       	breq	.+8      	; 0x978 <_ZNK8Internal13DCF77_Encoder28verify_leap_second_scheduledEb+0x4a>
     970:	84 30       	cpi	r24, 0x04	; 4
     972:	11 f0       	breq	.+4      	; 0x978 <_ZNK8Internal13DCF77_Encoder28verify_leap_second_scheduledEb+0x4a>
     974:	80 31       	cpi	r24, 0x10	; 16
     976:	39 f4       	brne	.+14     	; 0x986 <_ZNK8Internal13DCF77_Encoder28verify_leap_second_scheduledEb+0x58>
     978:	84 81       	ldd	r24, Z+4	; 0x04
     97a:	81 30       	cpi	r24, 0x01	; 1
     97c:	59 f3       	breq	.-42     	; 0x954 <_ZNK8Internal13DCF77_Encoder28verify_leap_second_scheduledEb+0x26>
     97e:	82 30       	cpi	r24, 0x02	; 2
     980:	61 f7       	brne	.-40     	; 0x95a <_ZNK8Internal13DCF77_Encoder28verify_leap_second_scheduledEb+0x2c>
     982:	81 e0       	ldi	r24, 0x01	; 1
     984:	ee cf       	rjmp	.-36     	; 0x962 <_ZNK8Internal13DCF77_Encoder28verify_leap_second_scheduledEb+0x34>
     986:	80 e0       	ldi	r24, 0x00	; 0
     988:	08 95       	ret

0000098a <_ZNK8Internal13DCF77_Encoder11get_weekdayEv>:
     98a:	fc 01       	movw	r30, r24
     98c:	62 81       	ldd	r22, Z+2	; 0x02
     98e:	62 33       	cpi	r22, 0x32	; 50
     990:	08 f0       	brcs	.+2      	; 0x994 <_ZNK8Internal13DCF77_Encoder11get_weekdayEv+0xa>
     992:	49 c0       	rjmp	.+146    	; 0xa26 <_ZNK8Internal13DCF77_Encoder11get_weekdayEv+0x9c>
     994:	91 81       	ldd	r25, Z+1	; 0x01
     996:	93 31       	cpi	r25, 0x13	; 19
     998:	08 f0       	brcs	.+2      	; 0x99c <_ZNK8Internal13DCF77_Encoder11get_weekdayEv+0x12>
     99a:	45 c0       	rjmp	.+138    	; 0xa26 <_ZNK8Internal13DCF77_Encoder11get_weekdayEv+0x9c>
     99c:	80 81       	ld	r24, Z
     99e:	8a 39       	cpi	r24, 0x9A	; 154
     9a0:	08 f0       	brcs	.+2      	; 0x9a4 <_ZNK8Internal13DCF77_Encoder11get_weekdayEv+0x1a>
     9a2:	41 c0       	rjmp	.+130    	; 0xa26 <_ZNK8Internal13DCF77_Encoder11get_weekdayEv+0x9c>
     9a4:	86 2f       	mov	r24, r22
     9a6:	82 95       	swap	r24
     9a8:	8f 70       	andi	r24, 0x0F	; 15
     9aa:	2a e0       	ldi	r18, 0x0A	; 10
     9ac:	6f 70       	andi	r22, 0x0F	; 15
     9ae:	36 2f       	mov	r19, r22
     9b0:	82 9f       	mul	r24, r18
     9b2:	30 0d       	add	r19, r0
     9b4:	11 24       	eor	r1, r1
     9b6:	49 2f       	mov	r20, r25
     9b8:	93 30       	cpi	r25, 0x03	; 3
     9ba:	58 f5       	brcc	.+86     	; 0xa12 <_ZNK8Internal13DCF77_Encoder11get_weekdayEv+0x88>
     9bc:	50 e0       	ldi	r21, 0x00	; 0
     9be:	46 5f       	subi	r20, 0xF6	; 246
     9c0:	5f 4f       	sbci	r21, 0xFF	; 255
     9c2:	20 81       	ld	r18, Z
     9c4:	82 2f       	mov	r24, r18
     9c6:	82 95       	swap	r24
     9c8:	8f 70       	andi	r24, 0x0F	; 15
     9ca:	2f 70       	andi	r18, 0x0F	; 15
     9cc:	6a e0       	ldi	r22, 0x0A	; 10
     9ce:	86 9f       	mul	r24, r22
     9d0:	20 0d       	add	r18, r0
     9d2:	11 24       	eor	r1, r1
     9d4:	81 e0       	ldi	r24, 0x01	; 1
     9d6:	93 30       	cpi	r25, 0x03	; 3
     9d8:	08 f0       	brcs	.+2      	; 0x9dc <_ZNK8Internal13DCF77_Encoder11get_weekdayEv+0x52>
     9da:	80 e0       	ldi	r24, 0x00	; 0
     9dc:	28 1b       	sub	r18, r24
     9de:	6a e1       	ldi	r22, 0x1A	; 26
     9e0:	64 9f       	mul	r22, r20
     9e2:	c0 01       	movw	r24, r0
     9e4:	65 9f       	mul	r22, r21
     9e6:	90 0d       	add	r25, r0
     9e8:	11 24       	eor	r1, r1
     9ea:	02 97       	sbiw	r24, 0x02	; 2
     9ec:	6a e0       	ldi	r22, 0x0A	; 10
     9ee:	70 e0       	ldi	r23, 0x00	; 0
     9f0:	0e 94 ea 26 	call	0x4dd4	; 0x4dd4 <__udivmodhi4>
     9f4:	82 2f       	mov	r24, r18
     9f6:	83 0f       	add	r24, r19
     9f8:	26 95       	lsr	r18
     9fa:	26 95       	lsr	r18
     9fc:	82 0f       	add	r24, r18
     9fe:	86 0f       	add	r24, r22
     a00:	87 30       	cpi	r24, 0x07	; 7
     a02:	90 f0       	brcs	.+36     	; 0xa28 <_ZNK8Internal13DCF77_Encoder11get_weekdayEv+0x9e>
     a04:	87 50       	subi	r24, 0x07	; 7
     a06:	68 2f       	mov	r22, r24
     a08:	66 95       	lsr	r22
     a0a:	66 95       	lsr	r22
     a0c:	66 95       	lsr	r22
     a0e:	87 70       	andi	r24, 0x07	; 7
     a10:	f6 cf       	rjmp	.-20     	; 0x9fe <_ZNK8Internal13DCF77_Encoder11get_weekdayEv+0x74>
     a12:	4f 70       	andi	r20, 0x0F	; 15
     a14:	89 2f       	mov	r24, r25
     a16:	82 95       	swap	r24
     a18:	8f 70       	andi	r24, 0x0F	; 15
     a1a:	82 9f       	mul	r24, r18
     a1c:	40 0d       	add	r20, r0
     a1e:	11 24       	eor	r1, r1
     a20:	42 50       	subi	r20, 0x02	; 2
     a22:	55 0b       	sbc	r21, r21
     a24:	ce cf       	rjmp	.-100    	; 0x9c2 <_ZNK8Internal13DCF77_Encoder11get_weekdayEv+0x38>
     a26:	8f ef       	ldi	r24, 0xFF	; 255
     a28:	08 95       	ret

00000a2a <_ZN8Internal13DCF77_Encoder20autoset_control_bitsEv>:
     a2a:	0f 93       	push	r16
     a2c:	1f 93       	push	r17
     a2e:	cf 93       	push	r28
     a30:	df 93       	push	r29
     a32:	ec 01       	movw	r28, r24
     a34:	aa df       	rcall	.-172    	; 0x98a <_ZNK8Internal13DCF77_Encoder11get_weekdayEv>
     a36:	81 11       	cpse	r24, r1
     a38:	01 c0       	rjmp	.+2      	; 0xa3c <_ZN8Internal13DCF77_Encoder20autoset_control_bitsEv+0x12>
     a3a:	87 e0       	ldi	r24, 0x07	; 7
     a3c:	8b 83       	std	Y+3, r24	; 0x03
     a3e:	19 81       	ldd	r17, Y+1	; 0x01
     a40:	0a 81       	ldd	r16, Y+2	; 0x02
     a42:	13 30       	cpi	r17, 0x03	; 3
     a44:	c8 f4       	brcc	.+50     	; 0xa78 <_ZN8Internal13DCF77_Encoder20autoset_control_bitsEv+0x4e>
     a46:	8f 81       	ldd	r24, Y+7	; 0x07
     a48:	8e 7f       	andi	r24, 0xFE	; 254
     a4a:	8f 83       	std	Y+7, r24	; 0x07
     a4c:	05 32       	cpi	r16, 0x25	; 37
     a4e:	28 f0       	brcs	.+10     	; 0xa5a <_ZN8Internal13DCF77_Encoder20autoset_control_bitsEv+0x30>
     a50:	ce 01       	movw	r24, r28
     a52:	9b df       	rcall	.-202    	; 0x98a <_ZNK8Internal13DCF77_Encoder11get_weekdayEv>
     a54:	88 23       	and	r24, r24
     a56:	09 f4       	brne	.+2      	; 0xa5a <_ZN8Internal13DCF77_Encoder20autoset_control_bitsEv+0x30>
     a58:	43 c0       	rjmp	.+134    	; 0xae0 <_ZN8Internal13DCF77_Encoder20autoset_control_bitsEv+0xb6>
     a5a:	8f 81       	ldd	r24, Y+7	; 0x07
     a5c:	8b 7f       	andi	r24, 0xFB	; 251
     a5e:	8f 83       	std	Y+7, r24	; 0x07
     a60:	60 e0       	ldi	r22, 0x00	; 0
     a62:	ce 01       	movw	r24, r28
     a64:	64 df       	rcall	.-312    	; 0x92e <_ZNK8Internal13DCF77_Encoder28verify_leap_second_scheduledEb>
     a66:	9f 81       	ldd	r25, Y+7	; 0x07
     a68:	80 fb       	bst	r24, 0
     a6a:	93 f9       	bld	r25, 3
     a6c:	9f 83       	std	Y+7, r25	; 0x07
     a6e:	df 91       	pop	r29
     a70:	cf 91       	pop	r28
     a72:	1f 91       	pop	r17
     a74:	0f 91       	pop	r16
     a76:	08 95       	ret
     a78:	13 30       	cpi	r17, 0x03	; 3
     a7a:	a9 f4       	brne	.+42     	; 0xaa6 <_ZN8Internal13DCF77_Encoder20autoset_control_bitsEv+0x7c>
     a7c:	05 32       	cpi	r16, 0x25	; 37
     a7e:	18 f3       	brcs	.-58     	; 0xa46 <_ZN8Internal13DCF77_Encoder20autoset_control_bitsEv+0x1c>
     a80:	ce 01       	movw	r24, r28
     a82:	83 df       	rcall	.-250    	; 0x98a <_ZNK8Internal13DCF77_Encoder11get_weekdayEv>
     a84:	88 23       	and	r24, r24
     a86:	49 f0       	breq	.+18     	; 0xa9a <_ZN8Internal13DCF77_Encoder20autoset_control_bitsEv+0x70>
     a88:	20 2f       	mov	r18, r16
     a8a:	28 1b       	sub	r18, r24
     a8c:	33 0b       	sbc	r19, r19
     a8e:	25 32       	cpi	r18, 0x25	; 37
     a90:	31 05       	cpc	r19, r1
     a92:	cc f2       	brlt	.-78     	; 0xa46 <_ZN8Internal13DCF77_Encoder20autoset_control_bitsEv+0x1c>
     a94:	8f 81       	ldd	r24, Y+7	; 0x07
     a96:	81 60       	ori	r24, 0x01	; 1
     a98:	d8 cf       	rjmp	.-80     	; 0xa4a <_ZN8Internal13DCF77_Encoder20autoset_control_bitsEv+0x20>
     a9a:	91 e0       	ldi	r25, 0x01	; 1
     a9c:	8c 81       	ldd	r24, Y+4	; 0x04
     a9e:	82 30       	cpi	r24, 0x02	; 2
     aa0:	d0 f4       	brcc	.+52     	; 0xad6 <_ZN8Internal13DCF77_Encoder20autoset_control_bitsEv+0xac>
     aa2:	90 e0       	ldi	r25, 0x00	; 0
     aa4:	18 c0       	rjmp	.+48     	; 0xad6 <_ZN8Internal13DCF77_Encoder20autoset_control_bitsEv+0xac>
     aa6:	10 31       	cpi	r17, 0x10	; 16
     aa8:	a8 f3       	brcs	.-22     	; 0xa94 <_ZN8Internal13DCF77_Encoder20autoset_control_bitsEv+0x6a>
     aaa:	10 31       	cpi	r17, 0x10	; 16
     aac:	61 f6       	brne	.-104    	; 0xa46 <_ZN8Internal13DCF77_Encoder20autoset_control_bitsEv+0x1c>
     aae:	05 32       	cpi	r16, 0x25	; 37
     ab0:	88 f3       	brcs	.-30     	; 0xa94 <_ZN8Internal13DCF77_Encoder20autoset_control_bitsEv+0x6a>
     ab2:	ce 01       	movw	r24, r28
     ab4:	6a df       	rcall	.-300    	; 0x98a <_ZNK8Internal13DCF77_Encoder11get_weekdayEv>
     ab6:	88 23       	and	r24, r24
     ab8:	39 f0       	breq	.+14     	; 0xac8 <_ZN8Internal13DCF77_Encoder20autoset_control_bitsEv+0x9e>
     aba:	20 2f       	mov	r18, r16
     abc:	28 1b       	sub	r18, r24
     abe:	33 0b       	sbc	r19, r19
     ac0:	25 32       	cpi	r18, 0x25	; 37
     ac2:	31 05       	cpc	r19, r1
     ac4:	3c f3       	brlt	.-50     	; 0xa94 <_ZN8Internal13DCF77_Encoder20autoset_control_bitsEv+0x6a>
     ac6:	bf cf       	rjmp	.-130    	; 0xa46 <_ZN8Internal13DCF77_Encoder20autoset_control_bitsEv+0x1c>
     ac8:	8c 81       	ldd	r24, Y+4	; 0x04
     aca:	82 30       	cpi	r24, 0x02	; 2
     acc:	09 f4       	brne	.+2      	; 0xad0 <_ZN8Internal13DCF77_Encoder20autoset_control_bitsEv+0xa6>
     ace:	c0 cf       	rjmp	.-128    	; 0xa50 <_ZN8Internal13DCF77_Encoder20autoset_control_bitsEv+0x26>
     ad0:	91 e0       	ldi	r25, 0x01	; 1
     ad2:	82 30       	cpi	r24, 0x02	; 2
     ad4:	30 f7       	brcc	.-52     	; 0xaa2 <_ZN8Internal13DCF77_Encoder20autoset_control_bitsEv+0x78>
     ad6:	8f 81       	ldd	r24, Y+7	; 0x07
     ad8:	90 fb       	bst	r25, 0
     ada:	80 f9       	bld	r24, 0
     adc:	8f 83       	std	Y+7, r24	; 0x07
     ade:	b8 cf       	rjmp	.-144    	; 0xa50 <_ZN8Internal13DCF77_Encoder20autoset_control_bitsEv+0x26>
     ae0:	13 30       	cpi	r17, 0x03	; 3
     ae2:	a1 f4       	brne	.+40     	; 0xb0c <_ZN8Internal13DCF77_Encoder20autoset_control_bitsEv+0xe2>
     ae4:	8f 81       	ldd	r24, Y+7	; 0x07
     ae6:	2c 81       	ldd	r18, Y+4	; 0x04
     ae8:	98 2f       	mov	r25, r24
     aea:	91 70       	andi	r25, 0x01	; 1
     aec:	80 ff       	sbrs	r24, 0
     aee:	07 c0       	rjmp	.+14     	; 0xafe <_ZN8Internal13DCF77_Encoder20autoset_control_bitsEv+0xd4>
     af0:	23 30       	cpi	r18, 0x03	; 3
     af2:	b1 f4       	brne	.+44     	; 0xb20 <_ZN8Internal13DCF77_Encoder20autoset_control_bitsEv+0xf6>
     af4:	91 e0       	ldi	r25, 0x01	; 1
     af6:	2d 81       	ldd	r18, Y+5	; 0x05
     af8:	22 23       	and	r18, r18
     afa:	99 f0       	breq	.+38     	; 0xb22 <_ZN8Internal13DCF77_Encoder20autoset_control_bitsEv+0xf8>
     afc:	11 c0       	rjmp	.+34     	; 0xb20 <_ZN8Internal13DCF77_Encoder20autoset_control_bitsEv+0xf6>
     afe:	21 30       	cpi	r18, 0x01	; 1
     b00:	81 f4       	brne	.+32     	; 0xb22 <_ZN8Internal13DCF77_Encoder20autoset_control_bitsEv+0xf8>
     b02:	91 e0       	ldi	r25, 0x01	; 1
     b04:	2d 81       	ldd	r18, Y+5	; 0x05
     b06:	21 11       	cpse	r18, r1
     b08:	0c c0       	rjmp	.+24     	; 0xb22 <_ZN8Internal13DCF77_Encoder20autoset_control_bitsEv+0xf8>
     b0a:	0a c0       	rjmp	.+20     	; 0xb20 <_ZN8Internal13DCF77_Encoder20autoset_control_bitsEv+0xf6>
     b0c:	10 31       	cpi	r17, 0x10	; 16
     b0e:	79 f4       	brne	.+30     	; 0xb2e <_ZN8Internal13DCF77_Encoder20autoset_control_bitsEv+0x104>
     b10:	8f 81       	ldd	r24, Y+7	; 0x07
     b12:	2c 81       	ldd	r18, Y+4	; 0x04
     b14:	98 2f       	mov	r25, r24
     b16:	91 70       	andi	r25, 0x01	; 1
     b18:	80 ff       	sbrs	r24, 0
     b1a:	06 c0       	rjmp	.+12     	; 0xb28 <_ZN8Internal13DCF77_Encoder20autoset_control_bitsEv+0xfe>
     b1c:	22 30       	cpi	r18, 0x02	; 2
     b1e:	89 f3       	breq	.-30     	; 0xb02 <_ZN8Internal13DCF77_Encoder20autoset_control_bitsEv+0xd8>
     b20:	90 e0       	ldi	r25, 0x00	; 0
     b22:	90 fb       	bst	r25, 0
     b24:	82 f9       	bld	r24, 2
     b26:	9b cf       	rjmp	.-202    	; 0xa5e <_ZN8Internal13DCF77_Encoder20autoset_control_bitsEv+0x34>
     b28:	22 30       	cpi	r18, 0x02	; 2
     b2a:	d9 f7       	brne	.-10     	; 0xb22 <_ZN8Internal13DCF77_Encoder20autoset_control_bitsEv+0xf8>
     b2c:	e3 cf       	rjmp	.-58     	; 0xaf4 <_ZN8Internal13DCF77_Encoder20autoset_control_bitsEv+0xca>
     b2e:	13 31       	cpi	r17, 0x13	; 19
     b30:	08 f4       	brcc	.+2      	; 0xb34 <_ZN8Internal13DCF77_Encoder20autoset_control_bitsEv+0x10a>
     b32:	93 cf       	rjmp	.-218    	; 0xa5a <_ZN8Internal13DCF77_Encoder20autoset_control_bitsEv+0x30>
     b34:	95 cf       	rjmp	.-214    	; 0xa60 <_ZN8Internal13DCF77_Encoder20autoset_control_bitsEv+0x36>

00000b36 <_ZNK8Internal13DCF77_Encoder14days_per_monthEv>:
     b36:	dc 01       	movw	r26, r24
     b38:	11 96       	adiw	r26, 0x01	; 1
     b3a:	ec 91       	ld	r30, X
     b3c:	e1 50       	subi	r30, 0x01	; 1
     b3e:	e2 31       	cpi	r30, 0x12	; 18
     b40:	48 f5       	brcc	.+82     	; 0xb94 <_ZNK8Internal13DCF77_Encoder14days_per_monthEv+0x5e>
     b42:	f0 e0       	ldi	r31, 0x00	; 0
     b44:	ea 55       	subi	r30, 0x5A	; 90
     b46:	fa 4f       	sbci	r31, 0xFA	; 250
     b48:	0c 94 2d 27 	jmp	0x4e5a	; 0x4e5a <__tablejump2__>
     b4c:	cc 05       	cpc	r28, r12
     b4e:	ba 05       	cpc	r27, r10
     b50:	cc 05       	cpc	r28, r12
     b52:	b8 05       	cpc	r27, r8
     b54:	cc 05       	cpc	r28, r12
     b56:	b8 05       	cpc	r27, r8
     b58:	cc 05       	cpc	r28, r12
     b5a:	cc 05       	cpc	r28, r12
     b5c:	b8 05       	cpc	r27, r8
     b5e:	ca 05       	cpc	r28, r10
     b60:	ca 05       	cpc	r28, r10
     b62:	ca 05       	cpc	r28, r10
     b64:	ca 05       	cpc	r28, r10
     b66:	ca 05       	cpc	r28, r10
     b68:	ca 05       	cpc	r28, r10
     b6a:	cc 05       	cpc	r28, r12
     b6c:	b8 05       	cpc	r27, r8
     b6e:	cc 05       	cpc	r28, r12
     b70:	8e e1       	ldi	r24, 0x1E	; 30
     b72:	08 95       	ret
     b74:	fc 01       	movw	r30, r24
     b76:	80 81       	ld	r24, Z
     b78:	88 23       	and	r24, r24
     b7a:	81 f0       	breq	.+32     	; 0xb9c <_ZNK8Internal13DCF77_Encoder14days_per_monthEv+0x66>
     b7c:	98 2f       	mov	r25, r24
     b7e:	92 95       	swap	r25
     b80:	9f 70       	andi	r25, 0x0F	; 15
     b82:	8f 70       	andi	r24, 0x0F	; 15
     b84:	fa e0       	ldi	r31, 0x0A	; 10
     b86:	9f 9f       	mul	r25, r31
     b88:	80 0d       	add	r24, r0
     b8a:	11 24       	eor	r1, r1
     b8c:	83 70       	andi	r24, 0x03	; 3
     b8e:	31 f4       	brne	.+12     	; 0xb9c <_ZNK8Internal13DCF77_Encoder14days_per_monthEv+0x66>
     b90:	8d e1       	ldi	r24, 0x1D	; 29
     b92:	08 95       	ret
     b94:	80 e0       	ldi	r24, 0x00	; 0
     b96:	08 95       	ret
     b98:	8f e1       	ldi	r24, 0x1F	; 31
     b9a:	08 95       	ret
     b9c:	8c e1       	ldi	r24, 0x1C	; 28
     b9e:	08 95       	ret

00000ba0 <_ZN8Internal18DCF77_Flag_Decoder9cummulateERab>:
     ba0:	fc 01       	movw	r30, r24
     ba2:	90 81       	ld	r25, Z
     ba4:	66 23       	and	r22, r22
     ba6:	39 f0       	breq	.+14     	; 0xbb6 <_ZN8Internal18DCF77_Flag_Decoder9cummulateERab+0x16>
     ba8:	21 e0       	ldi	r18, 0x01	; 1
     baa:	9f 37       	cpi	r25, 0x7F	; 127
     bac:	09 f4       	brne	.+2      	; 0xbb0 <_ZN8Internal18DCF77_Flag_Decoder9cummulateERab+0x10>
     bae:	20 e0       	ldi	r18, 0x00	; 0
     bb0:	92 0f       	add	r25, r18
     bb2:	90 83       	st	Z, r25
     bb4:	08 95       	ret
     bb6:	81 e0       	ldi	r24, 0x01	; 1
     bb8:	92 38       	cpi	r25, 0x82	; 130
     bba:	0c f4       	brge	.+2      	; 0xbbe <_ZN8Internal18DCF77_Flag_Decoder9cummulateERab+0x1e>
     bbc:	80 e0       	ldi	r24, 0x00	; 0
     bbe:	98 1b       	sub	r25, r24
     bc0:	f8 cf       	rjmp	.-16     	; 0xbb2 <_ZN8Internal18DCF77_Flag_Decoder9cummulateERab+0x12>

00000bc2 <_ZN8Internal16Arithmetic_Tools6parityEh>:
     bc2:	98 2f       	mov	r25, r24
     bc4:	9f 70       	andi	r25, 0x0F	; 15
     bc6:	82 95       	swap	r24
     bc8:	8f 70       	andi	r24, 0x0F	; 15
     bca:	98 27       	eor	r25, r24
     bcc:	89 2f       	mov	r24, r25
     bce:	83 70       	andi	r24, 0x03	; 3
     bd0:	96 95       	lsr	r25
     bd2:	96 95       	lsr	r25
     bd4:	98 27       	eor	r25, r24
     bd6:	89 2f       	mov	r24, r25
     bd8:	81 70       	andi	r24, 0x01	; 1
     bda:	96 95       	lsr	r25
     bdc:	89 27       	eor	r24, r25
     bde:	08 95       	ret

00000be0 <_ZN3BCD10int_to_bcdEh>:
     be0:	28 2f       	mov	r18, r24
     be2:	6a e0       	ldi	r22, 0x0A	; 10
     be4:	0e 94 d1 26 	call	0x4da2	; 0x4da2 <__udivmodqi4>
     be8:	96 ef       	ldi	r25, 0xF6	; 246
     bea:	89 9f       	mul	r24, r25
     bec:	20 0d       	add	r18, r0
     bee:	11 24       	eor	r1, r1
     bf0:	82 95       	swap	r24
     bf2:	80 7f       	andi	r24, 0xF0	; 240
     bf4:	2f 70       	andi	r18, 0x0F	; 15
     bf6:	82 2b       	or	r24, r18
     bf8:	08 95       	ret

00000bfa <_ZN8Internal7Binning7DecoderIhLj12EE14get_time_valueEv.constprop.45>:
     bfa:	80 91 58 04 	lds	r24, 0x0458	; 0x800458 <_ZN8Internal22DCF77_Clock_ControllerI13ConfigurationNS_23DCF77_Frequency_ControlEE13Month_DecoderE+0xe>
     bfe:	90 91 57 04 	lds	r25, 0x0457	; 0x800457 <_ZN8Internal22DCF77_Clock_ControllerI13ConfigurationNS_23DCF77_Frequency_ControlEE13Month_DecoderE+0xd>
     c02:	89 1b       	sub	r24, r25
     c04:	99 0b       	sbc	r25, r25
     c06:	02 97       	sbiw	r24, 0x02	; 2
     c08:	74 f0       	brlt	.+28     	; 0xc26 <_ZN8Internal7Binning7DecoderIhLj12EE14get_time_valueEv.constprop.45+0x2c>
     c0a:	80 91 59 04 	lds	r24, 0x0459	; 0x800459 <_ZN8Internal22DCF77_Clock_ControllerI13ConfigurationNS_23DCF77_Frequency_ControlEE13Month_DecoderE+0xf>
     c0e:	90 91 56 04 	lds	r25, 0x0456	; 0x800456 <_ZN8Internal22DCF77_Clock_ControllerI13ConfigurationNS_23DCF77_Frequency_ControlEE13Month_DecoderE+0xc>
     c12:	89 0f       	add	r24, r25
     c14:	99 27       	eor	r25, r25
     c16:	99 1f       	adc	r25, r25
     c18:	01 96       	adiw	r24, 0x01	; 1
     c1a:	6c e0       	ldi	r22, 0x0C	; 12
     c1c:	70 e0       	ldi	r23, 0x00	; 0
     c1e:	0e 94 ea 26 	call	0x4dd4	; 0x4dd4 <__udivmodhi4>
     c22:	8f 5f       	subi	r24, 0xFF	; 255
     c24:	dd cf       	rjmp	.-70     	; 0xbe0 <_ZN3BCD10int_to_bcdEh>
     c26:	8f ef       	ldi	r24, 0xFF	; 255
     c28:	08 95       	ret

00000c2a <_ZN8Internal7Binning7DecoderIhLj31EE14get_time_valueEv.constprop.42>:
     c2a:	80 91 48 04 	lds	r24, 0x0448	; 0x800448 <_ZN8Internal22DCF77_Clock_ControllerI13ConfigurationNS_23DCF77_Frequency_ControlEE11Day_DecoderE+0x21>
     c2e:	90 91 47 04 	lds	r25, 0x0447	; 0x800447 <_ZN8Internal22DCF77_Clock_ControllerI13ConfigurationNS_23DCF77_Frequency_ControlEE11Day_DecoderE+0x20>
     c32:	89 1b       	sub	r24, r25
     c34:	99 0b       	sbc	r25, r25
     c36:	02 97       	sbiw	r24, 0x02	; 2
     c38:	74 f0       	brlt	.+28     	; 0xc56 <_ZN8Internal7Binning7DecoderIhLj31EE14get_time_valueEv.constprop.42+0x2c>
     c3a:	80 91 49 04 	lds	r24, 0x0449	; 0x800449 <_ZN8Internal22DCF77_Clock_ControllerI13ConfigurationNS_23DCF77_Frequency_ControlEE11Day_DecoderE+0x22>
     c3e:	90 91 46 04 	lds	r25, 0x0446	; 0x800446 <_ZN8Internal22DCF77_Clock_ControllerI13ConfigurationNS_23DCF77_Frequency_ControlEE11Day_DecoderE+0x1f>
     c42:	89 0f       	add	r24, r25
     c44:	99 27       	eor	r25, r25
     c46:	99 1f       	adc	r25, r25
     c48:	01 96       	adiw	r24, 0x01	; 1
     c4a:	6f e1       	ldi	r22, 0x1F	; 31
     c4c:	70 e0       	ldi	r23, 0x00	; 0
     c4e:	0e 94 ea 26 	call	0x4dd4	; 0x4dd4 <__udivmodhi4>
     c52:	8f 5f       	subi	r24, 0xFF	; 255
     c54:	c5 cf       	rjmp	.-118    	; 0xbe0 <_ZN3BCD10int_to_bcdEh>
     c56:	8f ef       	ldi	r24, 0xFF	; 255
     c58:	08 95       	ret

00000c5a <_ZN8Internal7Binning7DecoderIhLj7EE14get_time_valueEv.constprop.39>:
     c5a:	80 91 25 04 	lds	r24, 0x0425	; 0x800425 <_ZN8Internal22DCF77_Clock_ControllerI13ConfigurationNS_23DCF77_Frequency_ControlEE15Weekday_DecoderE+0x9>
     c5e:	90 91 24 04 	lds	r25, 0x0424	; 0x800424 <_ZN8Internal22DCF77_Clock_ControllerI13ConfigurationNS_23DCF77_Frequency_ControlEE15Weekday_DecoderE+0x8>
     c62:	89 1b       	sub	r24, r25
     c64:	99 0b       	sbc	r25, r25
     c66:	02 97       	sbiw	r24, 0x02	; 2
     c68:	74 f0       	brlt	.+28     	; 0xc86 <_ZN8Internal7Binning7DecoderIhLj7EE14get_time_valueEv.constprop.39+0x2c>
     c6a:	80 91 26 04 	lds	r24, 0x0426	; 0x800426 <_ZN8Internal22DCF77_Clock_ControllerI13ConfigurationNS_23DCF77_Frequency_ControlEE15Weekday_DecoderE+0xa>
     c6e:	90 91 23 04 	lds	r25, 0x0423	; 0x800423 <_ZN8Internal22DCF77_Clock_ControllerI13ConfigurationNS_23DCF77_Frequency_ControlEE15Weekday_DecoderE+0x7>
     c72:	89 0f       	add	r24, r25
     c74:	99 27       	eor	r25, r25
     c76:	99 1f       	adc	r25, r25
     c78:	01 96       	adiw	r24, 0x01	; 1
     c7a:	67 e0       	ldi	r22, 0x07	; 7
     c7c:	70 e0       	ldi	r23, 0x00	; 0
     c7e:	0e 94 ea 26 	call	0x4dd4	; 0x4dd4 <__udivmodhi4>
     c82:	8f 5f       	subi	r24, 0xFF	; 255
     c84:	ad cf       	rjmp	.-166    	; 0xbe0 <_ZN3BCD10int_to_bcdEh>
     c86:	8f ef       	ldi	r24, 0xFF	; 255
     c88:	08 95       	ret

00000c8a <_ZN8Internal7Binning7DecoderIhLj24EE14get_time_valueEv.constprop.36>:
     c8a:	80 91 1a 04 	lds	r24, 0x041A	; 0x80041a <_ZN8Internal22DCF77_Clock_ControllerI13ConfigurationNS_23DCF77_Frequency_ControlEE12Hour_DecoderE+0x1a>
     c8e:	90 91 19 04 	lds	r25, 0x0419	; 0x800419 <_ZN8Internal22DCF77_Clock_ControllerI13ConfigurationNS_23DCF77_Frequency_ControlEE12Hour_DecoderE+0x19>
     c92:	89 1b       	sub	r24, r25
     c94:	99 0b       	sbc	r25, r25
     c96:	02 97       	sbiw	r24, 0x02	; 2
     c98:	6c f0       	brlt	.+26     	; 0xcb4 <_ZN8Internal7Binning7DecoderIhLj24EE14get_time_valueEv.constprop.36+0x2a>
     c9a:	80 91 1b 04 	lds	r24, 0x041B	; 0x80041b <_ZN8Internal22DCF77_Clock_ControllerI13ConfigurationNS_23DCF77_Frequency_ControlEE12Hour_DecoderE+0x1b>
     c9e:	90 91 18 04 	lds	r25, 0x0418	; 0x800418 <_ZN8Internal22DCF77_Clock_ControllerI13ConfigurationNS_23DCF77_Frequency_ControlEE12Hour_DecoderE+0x18>
     ca2:	89 0f       	add	r24, r25
     ca4:	99 27       	eor	r25, r25
     ca6:	99 1f       	adc	r25, r25
     ca8:	01 96       	adiw	r24, 0x01	; 1
     caa:	68 e1       	ldi	r22, 0x18	; 24
     cac:	70 e0       	ldi	r23, 0x00	; 0
     cae:	0e 94 ea 26 	call	0x4dd4	; 0x4dd4 <__udivmodhi4>
     cb2:	96 cf       	rjmp	.-212    	; 0xbe0 <_ZN3BCD10int_to_bcdEh>
     cb4:	8f ef       	ldi	r24, 0xFF	; 255
     cb6:	08 95       	ret

00000cb8 <_ZN8Internal7Binning7DecoderIhLj60EE14get_time_valueEv.constprop.27>:
     cb8:	80 91 b6 03 	lds	r24, 0x03B6	; 0x8003b6 <_ZN8Internal22DCF77_Clock_ControllerI13ConfigurationNS_23DCF77_Frequency_ControlEE14Minute_DecoderE+0x3e>
     cbc:	90 91 b5 03 	lds	r25, 0x03B5	; 0x8003b5 <_ZN8Internal22DCF77_Clock_ControllerI13ConfigurationNS_23DCF77_Frequency_ControlEE14Minute_DecoderE+0x3d>
     cc0:	89 1b       	sub	r24, r25
     cc2:	99 0b       	sbc	r25, r25
     cc4:	02 97       	sbiw	r24, 0x02	; 2
     cc6:	6c f0       	brlt	.+26     	; 0xce2 <_ZN8Internal7Binning7DecoderIhLj60EE14get_time_valueEv.constprop.27+0x2a>
     cc8:	80 91 b7 03 	lds	r24, 0x03B7	; 0x8003b7 <_ZN8Internal22DCF77_Clock_ControllerI13ConfigurationNS_23DCF77_Frequency_ControlEE14Minute_DecoderE+0x3f>
     ccc:	90 91 b4 03 	lds	r25, 0x03B4	; 0x8003b4 <_ZN8Internal22DCF77_Clock_ControllerI13ConfigurationNS_23DCF77_Frequency_ControlEE14Minute_DecoderE+0x3c>
     cd0:	89 0f       	add	r24, r25
     cd2:	99 27       	eor	r25, r25
     cd4:	99 1f       	adc	r25, r25
     cd6:	01 96       	adiw	r24, 0x01	; 1
     cd8:	6c e3       	ldi	r22, 0x3C	; 60
     cda:	70 e0       	ldi	r23, 0x00	; 0
     cdc:	0e 94 ea 26 	call	0x4dd4	; 0x4dd4 <__udivmodhi4>
     ce0:	7f cf       	rjmp	.-258    	; 0xbe0 <_ZN3BCD10int_to_bcdEh>
     ce2:	8f ef       	ldi	r24, 0xFF	; 255
     ce4:	08 95       	ret

00000ce6 <_ZN8Internal7Binning7DecoderIhLj10EE14get_time_valueEv>:
     ce6:	fc 01       	movw	r30, r24
     ce8:	84 85       	ldd	r24, Z+12	; 0x0c
     cea:	93 85       	ldd	r25, Z+11	; 0x0b
     cec:	89 1b       	sub	r24, r25
     cee:	99 0b       	sbc	r25, r25
     cf0:	02 97       	sbiw	r24, 0x02	; 2
     cf2:	5c f0       	brlt	.+22     	; 0xd0a <_ZN8Internal7Binning7DecoderIhLj10EE14get_time_valueEv+0x24>
     cf4:	85 85       	ldd	r24, Z+13	; 0x0d
     cf6:	92 85       	ldd	r25, Z+10	; 0x0a
     cf8:	89 0f       	add	r24, r25
     cfa:	99 27       	eor	r25, r25
     cfc:	99 1f       	adc	r25, r25
     cfe:	01 96       	adiw	r24, 0x01	; 1
     d00:	6a e0       	ldi	r22, 0x0A	; 10
     d02:	70 e0       	ldi	r23, 0x00	; 0
     d04:	0e 94 ea 26 	call	0x4dd4	; 0x4dd4 <__udivmodhi4>
     d08:	6b cf       	rjmp	.-298    	; 0xbe0 <_ZN3BCD10int_to_bcdEh>
     d0a:	8f ef       	ldi	r24, 0xFF	; 255
     d0c:	08 95       	ret

00000d0e <_ZN8Internal18DCF77_Year_Decoder14get_time_valueEv.constprop.29>:
     d0e:	cf 93       	push	r28
     d10:	8a e5       	ldi	r24, 0x5A	; 90
     d12:	94 e0       	ldi	r25, 0x04	; 4
     d14:	e8 df       	rcall	.-48     	; 0xce6 <_ZN8Internal7Binning7DecoderIhLj10EE14get_time_valueEv>
     d16:	c8 2f       	mov	r28, r24
     d18:	88 e6       	ldi	r24, 0x68	; 104
     d1a:	94 e0       	ldi	r25, 0x04	; 4
     d1c:	e4 df       	rcall	.-56     	; 0xce6 <_ZN8Internal7Binning7DecoderIhLj10EE14get_time_valueEv>
     d1e:	cf 3f       	cpi	r28, 0xFF	; 255
     d20:	39 f0       	breq	.+14     	; 0xd30 <_ZN8Internal18DCF77_Year_Decoder14get_time_valueEv.constprop.29+0x22>
     d22:	8f 3f       	cpi	r24, 0xFF	; 255
     d24:	19 f0       	breq	.+6      	; 0xd2c <_ZN8Internal18DCF77_Year_Decoder14get_time_valueEv.constprop.29+0x1e>
     d26:	82 95       	swap	r24
     d28:	80 7f       	andi	r24, 0xF0	; 240
     d2a:	8c 0f       	add	r24, r28
     d2c:	cf 91       	pop	r28
     d2e:	08 95       	ret
     d30:	8f ef       	ldi	r24, 0xFF	; 255
     d32:	fc cf       	rjmp	.-8      	; 0xd2c <_ZN8Internal18DCF77_Year_Decoder14get_time_valueEv.constprop.29+0x1e>

00000d34 <_ZN8Internal22DCF77_Clock_ControllerI13ConfigurationNS_23DCF77_Frequency_ControlEE17set_DCF77_EncoderERNS_13DCF77_EncoderE>:
     d34:	cf 93       	push	r28
     d36:	df 93       	push	r29
     d38:	ec 01       	movw	r28, r24
     d3a:	49 da       	rcall	.-2926   	; 0x1ce <_ZN8Internal20DCF77_Second_Decoder14get_time_valueEv.constprop.33>
     d3c:	8e 83       	std	Y+6, r24	; 0x06
     d3e:	bc df       	rcall	.-136    	; 0xcb8 <_ZN8Internal7Binning7DecoderIhLj60EE14get_time_valueEv.constprop.27>
     d40:	8d 83       	std	Y+5, r24	; 0x05
     d42:	a3 df       	rcall	.-186    	; 0xc8a <_ZN8Internal7Binning7DecoderIhLj24EE14get_time_valueEv.constprop.36>
     d44:	8c 83       	std	Y+4, r24	; 0x04
     d46:	89 df       	rcall	.-238    	; 0xc5a <_ZN8Internal7Binning7DecoderIhLj7EE14get_time_valueEv.constprop.39>
     d48:	8b 83       	std	Y+3, r24	; 0x03
     d4a:	6f df       	rcall	.-290    	; 0xc2a <_ZN8Internal7Binning7DecoderIhLj31EE14get_time_valueEv.constprop.42>
     d4c:	8a 83       	std	Y+2, r24	; 0x02
     d4e:	55 df       	rcall	.-342    	; 0xbfa <_ZN8Internal7Binning7DecoderIhLj12EE14get_time_valueEv.constprop.45>
     d50:	89 83       	std	Y+1, r24	; 0x01
     d52:	dd df       	rcall	.-70     	; 0xd0e <_ZN8Internal18DCF77_Year_Decoder14get_time_valueEv.constprop.29>
     d54:	88 83       	st	Y, r24
     d56:	8f 81       	ldd	r24, Y+7	; 0x07
     d58:	90 91 6f 03 	lds	r25, 0x036F	; 0x80036f <_ZN8Internal22DCF77_Clock_ControllerI13ConfigurationNS_23DCF77_Frequency_ControlEE12Flag_DecoderE>
     d5c:	90 fb       	bst	r25, 0
     d5e:	81 f9       	bld	r24, 1
     d60:	8f 83       	std	Y+7, r24	; 0x07
     d62:	91 e0       	ldi	r25, 0x01	; 1
     d64:	80 91 70 03 	lds	r24, 0x0370	; 0x800370 <_ZN8Internal22DCF77_Clock_ControllerI13ConfigurationNS_23DCF77_Frequency_ControlEE12Flag_DecoderE+0x1>
     d68:	18 16       	cp	r1, r24
     d6a:	0c f0       	brlt	.+2      	; 0xd6e <_ZN8Internal22DCF77_Clock_ControllerI13ConfigurationNS_23DCF77_Frequency_ControlEE17set_DCF77_EncoderERNS_13DCF77_EncoderE+0x3a>
     d6c:	90 e0       	ldi	r25, 0x00	; 0
     d6e:	8f 81       	ldd	r24, Y+7	; 0x07
     d70:	90 fb       	bst	r25, 0
     d72:	82 f9       	bld	r24, 2
     d74:	90 91 71 03 	lds	r25, 0x0371	; 0x800371 <_ZN8Internal22DCF77_Clock_ControllerI13ConfigurationNS_23DCF77_Frequency_ControlEE12Flag_DecoderE+0x2>
     d78:	8e 7f       	andi	r24, 0xFE	; 254
     d7a:	97 ff       	sbrs	r25, 7
     d7c:	81 60       	ori	r24, 0x01	; 1
     d7e:	8f 83       	std	Y+7, r24	; 0x07
     d80:	91 e0       	ldi	r25, 0x01	; 1
     d82:	80 91 72 03 	lds	r24, 0x0372	; 0x800372 <_ZN8Internal22DCF77_Clock_ControllerI13ConfigurationNS_23DCF77_Frequency_ControlEE12Flag_DecoderE+0x3>
     d86:	18 16       	cp	r1, r24
     d88:	0c f0       	brlt	.+2      	; 0xd8c <_ZN8Internal22DCF77_Clock_ControllerI13ConfigurationNS_23DCF77_Frequency_ControlEE17set_DCF77_EncoderERNS_13DCF77_EncoderE+0x58>
     d8a:	90 e0       	ldi	r25, 0x00	; 0
     d8c:	8f 81       	ldd	r24, Y+7	; 0x07
     d8e:	90 fb       	bst	r25, 0
     d90:	83 f9       	bld	r24, 3
     d92:	8f 83       	std	Y+7, r24	; 0x07
     d94:	df 91       	pop	r29
     d96:	cf 91       	pop	r28
     d98:	08 95       	ret

00000d9a <_ZN11DCF77_Clock17read_current_timeERN5Clock6time_tE>:
     d9a:	df 92       	push	r13
     d9c:	ef 92       	push	r14
     d9e:	ff 92       	push	r15
     da0:	0f 93       	push	r16
     da2:	1f 93       	push	r17
     da4:	cf 93       	push	r28
     da6:	df 93       	push	r29
     da8:	cd b7       	in	r28, 0x3d	; 61
     daa:	de b7       	in	r29, 0x3e	; 62
     dac:	28 97       	sbiw	r28, 0x08	; 8
     dae:	0f b6       	in	r0, 0x3f	; 63
     db0:	f8 94       	cli
     db2:	de bf       	out	0x3e, r29	; 62
     db4:	0f be       	out	0x3f, r0	; 63
     db6:	cd bf       	out	0x3d, r28	; 61
     db8:	8c 01       	movw	r16, r24
     dba:	2f b7       	in	r18, 0x3f	; 63
     dbc:	f8 94       	cli
     dbe:	88 e0       	ldi	r24, 0x08	; 8
     dc0:	ec e5       	ldi	r30, 0x5C	; 92
     dc2:	f3 e0       	ldi	r31, 0x03	; 3
     dc4:	de 01       	movw	r26, r28
     dc6:	11 96       	adiw	r26, 0x01	; 1
     dc8:	01 90       	ld	r0, Z+
     dca:	0d 92       	st	X+, r0
     dcc:	8a 95       	dec	r24
     dce:	e1 f7       	brne	.-8      	; 0xdc8 <_ZN11DCF77_Clock17read_current_timeERN5Clock6time_tE+0x2e>
     dd0:	80 91 62 03 	lds	r24, 0x0362	; 0x800362 <_ZN8Internal22DCF77_Clock_ControllerI13ConfigurationNS_23DCF77_Frequency_ControlEE11Local_ClockE+0x8>
     dd4:	90 91 63 03 	lds	r25, 0x0363	; 0x800363 <_ZN8Internal22DCF77_Clock_ControllerI13ConfigurationNS_23DCF77_Frequency_ControlEE11Local_ClockE+0x9>
     dd8:	90 fb       	bst	r25, 0
     dda:	dd 24       	eor	r13, r13
     ddc:	d0 f8       	bld	r13, 0
     dde:	92 fb       	bst	r25, 2
     de0:	ee 24       	eor	r14, r14
     de2:	e0 f8       	bld	r14, 0
     de4:	93 fb       	bst	r25, 3
     de6:	ff 24       	eor	r15, r15
     de8:	f0 f8       	bld	r15, 0
     dea:	2f bf       	out	0x3f, r18	; 63
     dec:	f9 de       	rcall	.-526    	; 0xbe0 <_ZN3BCD10int_to_bcdEh>
     dee:	f8 01       	movw	r30, r16
     df0:	86 83       	std	Z+6, r24	; 0x06
     df2:	8e 81       	ldd	r24, Y+6	; 0x06
     df4:	85 83       	std	Z+5, r24	; 0x05
     df6:	8d 81       	ldd	r24, Y+5	; 0x05
     df8:	84 83       	std	Z+4, r24	; 0x04
     dfa:	8c 81       	ldd	r24, Y+4	; 0x04
     dfc:	83 83       	std	Z+3, r24	; 0x03
     dfe:	8b 81       	ldd	r24, Y+3	; 0x03
     e00:	82 83       	std	Z+2, r24	; 0x02
     e02:	8a 81       	ldd	r24, Y+2	; 0x02
     e04:	81 83       	std	Z+1, r24	; 0x01
     e06:	89 81       	ldd	r24, Y+1	; 0x01
     e08:	80 83       	st	Z, r24
     e0a:	d7 82       	std	Z+7, r13	; 0x07
     e0c:	f1 86       	std	Z+9, r15	; 0x09
     e0e:	e0 86       	std	Z+8, r14	; 0x08
     e10:	28 96       	adiw	r28, 0x08	; 8
     e12:	0f b6       	in	r0, 0x3f	; 63
     e14:	f8 94       	cli
     e16:	de bf       	out	0x3e, r29	; 62
     e18:	0f be       	out	0x3f, r0	; 63
     e1a:	cd bf       	out	0x3d, r28	; 61
     e1c:	df 91       	pop	r29
     e1e:	cf 91       	pop	r28
     e20:	1f 91       	pop	r17
     e22:	0f 91       	pop	r16
     e24:	ff 90       	pop	r15
     e26:	ef 90       	pop	r14
     e28:	df 90       	pop	r13
     e2a:	08 95       	ret

00000e2c <_ZN3BCD9incrementERNS_5bcd_tE>:
     e2c:	fc 01       	movw	r30, r24
     e2e:	90 81       	ld	r25, Z
     e30:	29 2f       	mov	r18, r25
     e32:	2f 70       	andi	r18, 0x0F	; 15
     e34:	90 7f       	andi	r25, 0xF0	; 240
     e36:	29 30       	cpi	r18, 0x09	; 9
     e38:	28 f4       	brcc	.+10     	; 0xe44 <_ZN3BCD9incrementERNS_5bcd_tE+0x18>
     e3a:	2f 5f       	subi	r18, 0xFF	; 255
     e3c:	2f 70       	andi	r18, 0x0F	; 15
     e3e:	92 2b       	or	r25, r18
     e40:	90 83       	st	Z, r25
     e42:	08 95       	ret
     e44:	90 83       	st	Z, r25
     e46:	92 95       	swap	r25
     e48:	9f 70       	andi	r25, 0x0F	; 15
     e4a:	99 30       	cpi	r25, 0x09	; 9
     e4c:	20 f4       	brcc	.+8      	; 0xe56 <_ZN3BCD9incrementERNS_5bcd_tE+0x2a>
     e4e:	9f 5f       	subi	r25, 0xFF	; 255
     e50:	92 95       	swap	r25
     e52:	90 7f       	andi	r25, 0xF0	; 240
     e54:	f5 cf       	rjmp	.-22     	; 0xe40 <_ZN3BCD9incrementERNS_5bcd_tE+0x14>
     e56:	10 82       	st	Z, r1
     e58:	08 95       	ret

00000e5a <_ZN8Internal13DCF77_Encoder14advance_minuteEv>:
     e5a:	0f 93       	push	r16
     e5c:	1f 93       	push	r17
     e5e:	cf 93       	push	r28
     e60:	df 93       	push	r29
     e62:	fc 01       	movw	r30, r24
     e64:	25 81       	ldd	r18, Z+5	; 0x05
     e66:	29 35       	cpi	r18, 0x59	; 89
     e68:	30 f4       	brcc	.+12     	; 0xe76 <_ZN8Internal13DCF77_Encoder14advance_minuteEv+0x1c>
     e6a:	05 96       	adiw	r24, 0x05	; 5
     e6c:	df 91       	pop	r29
     e6e:	cf 91       	pop	r28
     e70:	1f 91       	pop	r17
     e72:	0f 91       	pop	r16
     e74:	db cf       	rjmp	.-74     	; 0xe2c <_ZN3BCD9incrementERNS_5bcd_tE>
     e76:	29 35       	cpi	r18, 0x59	; 89
     e78:	a1 f4       	brne	.+40     	; 0xea2 <_ZN8Internal13DCF77_Encoder14advance_minuteEv+0x48>
     e7a:	ec 01       	movw	r28, r24
     e7c:	15 82       	std	Z+5, r1	; 0x05
     e7e:	94 81       	ldd	r25, Z+4	; 0x04
     e80:	87 81       	ldd	r24, Z+7	; 0x07
     e82:	82 ff       	sbrs	r24, 2
     e84:	17 c0       	rjmp	.+46     	; 0xeb4 <_ZN8Internal13DCF77_Encoder14advance_minuteEv+0x5a>
     e86:	80 fd       	sbrc	r24, 0
     e88:	11 c0       	rjmp	.+34     	; 0xeac <_ZN8Internal13DCF77_Encoder14advance_minuteEv+0x52>
     e8a:	91 30       	cpi	r25, 0x01	; 1
     e8c:	99 f4       	brne	.+38     	; 0xeb4 <_ZN8Internal13DCF77_Encoder14advance_minuteEv+0x5a>
     e8e:	8f 01       	movw	r16, r30
     e90:	0c 5f       	subi	r16, 0xFC	; 252
     e92:	1f 4f       	sbci	r17, 0xFF	; 255
     e94:	c8 01       	movw	r24, r16
     e96:	ca df       	rcall	.-108    	; 0xe2c <_ZN3BCD9incrementERNS_5bcd_tE>
     e98:	c8 01       	movw	r24, r16
     e9a:	c8 df       	rcall	.-112    	; 0xe2c <_ZN3BCD9incrementERNS_5bcd_tE>
     e9c:	8f 81       	ldd	r24, Y+7	; 0x07
     e9e:	81 60       	ori	r24, 0x01	; 1
     ea0:	8f 83       	std	Y+7, r24	; 0x07
     ea2:	df 91       	pop	r29
     ea4:	cf 91       	pop	r28
     ea6:	1f 91       	pop	r17
     ea8:	0f 91       	pop	r16
     eaa:	08 95       	ret
     eac:	92 30       	cpi	r25, 0x02	; 2
     eae:	11 f4       	brne	.+4      	; 0xeb4 <_ZN8Internal13DCF77_Encoder14advance_minuteEv+0x5a>
     eb0:	8e 7f       	andi	r24, 0xFE	; 254
     eb2:	f6 cf       	rjmp	.-20     	; 0xea0 <_ZN8Internal13DCF77_Encoder14advance_minuteEv+0x46>
     eb4:	93 32       	cpi	r25, 0x23	; 35
     eb6:	18 f4       	brcc	.+6      	; 0xebe <_ZN8Internal13DCF77_Encoder14advance_minuteEv+0x64>
     eb8:	ce 01       	movw	r24, r28
     eba:	04 96       	adiw	r24, 0x04	; 4
     ebc:	d7 cf       	rjmp	.-82     	; 0xe6c <_ZN8Internal13DCF77_Encoder14advance_minuteEv+0x12>
     ebe:	93 32       	cpi	r25, 0x23	; 35
     ec0:	81 f7       	brne	.-32     	; 0xea2 <_ZN8Internal13DCF77_Encoder14advance_minuteEv+0x48>
     ec2:	1c 82       	std	Y+4, r1	; 0x04
     ec4:	8b 81       	ldd	r24, Y+3	; 0x03
     ec6:	87 30       	cpi	r24, 0x07	; 7
     ec8:	98 f4       	brcc	.+38     	; 0xef0 <_ZN8Internal13DCF77_Encoder14advance_minuteEv+0x96>
     eca:	ce 01       	movw	r24, r28
     ecc:	03 96       	adiw	r24, 0x03	; 3
     ece:	ae df       	rcall	.-164    	; 0xe2c <_ZN3BCD9incrementERNS_5bcd_tE>
     ed0:	1a 81       	ldd	r17, Y+2	; 0x02
     ed2:	81 2f       	mov	r24, r17
     ed4:	82 95       	swap	r24
     ed6:	8f 70       	andi	r24, 0x0F	; 15
     ed8:	1f 70       	andi	r17, 0x0F	; 15
     eda:	fa e0       	ldi	r31, 0x0A	; 10
     edc:	8f 9f       	mul	r24, r31
     ede:	10 0d       	add	r17, r0
     ee0:	11 24       	eor	r1, r1
     ee2:	ce 01       	movw	r24, r28
     ee4:	28 de       	rcall	.-944    	; 0xb36 <_ZNK8Internal13DCF77_Encoder14days_per_monthEv>
     ee6:	18 17       	cp	r17, r24
     ee8:	40 f4       	brcc	.+16     	; 0xefa <_ZN8Internal13DCF77_Encoder14advance_minuteEv+0xa0>
     eea:	ce 01       	movw	r24, r28
     eec:	02 96       	adiw	r24, 0x02	; 2
     eee:	be cf       	rjmp	.-132    	; 0xe6c <_ZN8Internal13DCF77_Encoder14advance_minuteEv+0x12>
     ef0:	87 30       	cpi	r24, 0x07	; 7
     ef2:	71 f7       	brne	.-36     	; 0xed0 <_ZN8Internal13DCF77_Encoder14advance_minuteEv+0x76>
     ef4:	81 e0       	ldi	r24, 0x01	; 1
     ef6:	8b 83       	std	Y+3, r24	; 0x03
     ef8:	eb cf       	rjmp	.-42     	; 0xed0 <_ZN8Internal13DCF77_Encoder14advance_minuteEv+0x76>
     efa:	18 13       	cpse	r17, r24
     efc:	d2 cf       	rjmp	.-92     	; 0xea2 <_ZN8Internal13DCF77_Encoder14advance_minuteEv+0x48>
     efe:	81 e0       	ldi	r24, 0x01	; 1
     f00:	8a 83       	std	Y+2, r24	; 0x02
     f02:	99 81       	ldd	r25, Y+1	; 0x01
     f04:	92 31       	cpi	r25, 0x12	; 18
     f06:	18 f4       	brcc	.+6      	; 0xf0e <_ZN8Internal13DCF77_Encoder14advance_minuteEv+0xb4>
     f08:	ce 01       	movw	r24, r28
     f0a:	01 96       	adiw	r24, 0x01	; 1
     f0c:	af cf       	rjmp	.-162    	; 0xe6c <_ZN8Internal13DCF77_Encoder14advance_minuteEv+0x12>
     f0e:	92 31       	cpi	r25, 0x12	; 18
     f10:	41 f6       	brne	.-112    	; 0xea2 <_ZN8Internal13DCF77_Encoder14advance_minuteEv+0x48>
     f12:	89 83       	std	Y+1, r24	; 0x01
     f14:	88 81       	ld	r24, Y
     f16:	89 39       	cpi	r24, 0x99	; 153
     f18:	10 f4       	brcc	.+4      	; 0xf1e <_ZN8Internal13DCF77_Encoder14advance_minuteEv+0xc4>
     f1a:	ce 01       	movw	r24, r28
     f1c:	a7 cf       	rjmp	.-178    	; 0xe6c <_ZN8Internal13DCF77_Encoder14advance_minuteEv+0x12>
     f1e:	89 39       	cpi	r24, 0x99	; 153
     f20:	09 f0       	breq	.+2      	; 0xf24 <_ZN8Internal13DCF77_Encoder14advance_minuteEv+0xca>
     f22:	bf cf       	rjmp	.-130    	; 0xea2 <_ZN8Internal13DCF77_Encoder14advance_minuteEv+0x48>
     f24:	18 82       	st	Y, r1
     f26:	bd cf       	rjmp	.-134    	; 0xea2 <_ZN8Internal13DCF77_Encoder14advance_minuteEv+0x48>
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
