Servacek/numeri/firmver/src/night_mode.h

#ifndef NIGHT_MODE_H
#define NIGHT_MODE_H

namespace NightMode {

// Vypne displej, prepne rezimy na NIGHT.
void enter();

// Zapne displej na nakonfigurovany jas, prepne rezimy na NONE.
void exit();

// Spusti (alebo predlzi) docasne zobrazenie casu pocas nocneho rezimu.
// Volame z handlera stlacenia tlacidla aby uzivatel hned videl cas.
void startPreview();

// Vypne docase zobrazenie casu a vrati sa spat do nocneho rezimu.
void stopPreview();

// Volame z milisekundoveho handlera hlavneho loopu.
// Spravuje preview casu po stlaceni tlacidla.
void onMillisecondTick();

} // namespace NightMode

#endif // NIGHT_MODE_H
