Servacek/numeri/firmver/src/edit.h

#ifndef EDIT_H
#define EDIT_H

#include "main.h"
#include "clock.h"
#include "config.h"
#include "drivers/display.h"

namespace Edit {

// Potrebujeme dat uzivatelovi viac casu aby mohol v klude
// hladat nastavenia v prirucke a pomaly upravovat podla potrieb.
static constexpr uint16_t _EDIT_MODE_TIMEOUT_S = 5u * 60u;

bool isEditingLedBrightness();

void enter();

void exit();

//////////////////////////////
/// Konfiguracia
//////////////////////////////

void setupAllConfigurations();

//////////////////////////////
/// Sekundovy handler
//////////////////////////////

void onSecondTick();

}

#endif // EDIT_H
